gasiepgodoy/Open-Source-PLC/Hardware/KiCad Files/Components/3D/SM5819PL-TP--3DModel-STEP-56544.STEP

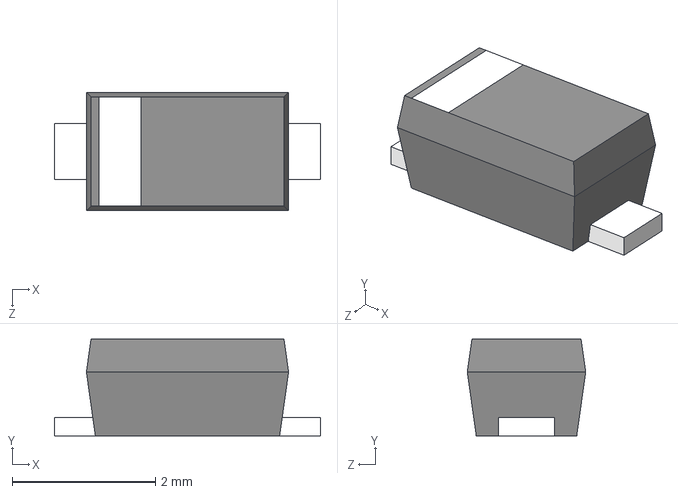
[picture p17: CAD file, 2024-05-21]
Hardware/KiCad Files/Components/3D/SM5819PL-TP--3DModel-STEP-56544.STEP
3.71 x 1.35 x 1.65 mm
