gasiepgodoy/Open-Source-PLC/Hardware/KiCad Files/Components/3D/74LCX14MTC.stp

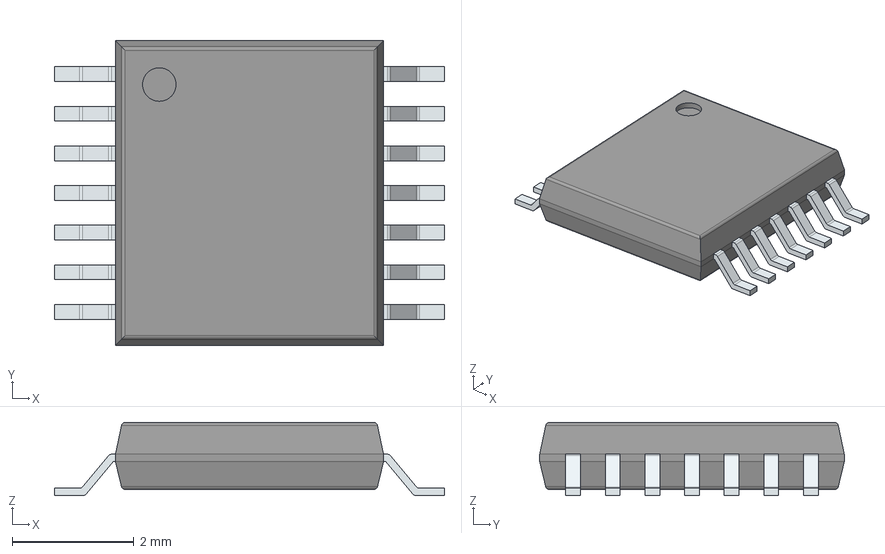
[picture p18: CAD file, 2024-05-21]
Hardware/KiCad Files/Components/3D/74LCX14MTC.stp
6.40 x 5.00 x 1.20 mm
PinsArrayLR
