gasiepgodoy/Open-Source-PLC/Hardware/KiCad Files/Components/3D/SN75LBC172A16DWR.stp

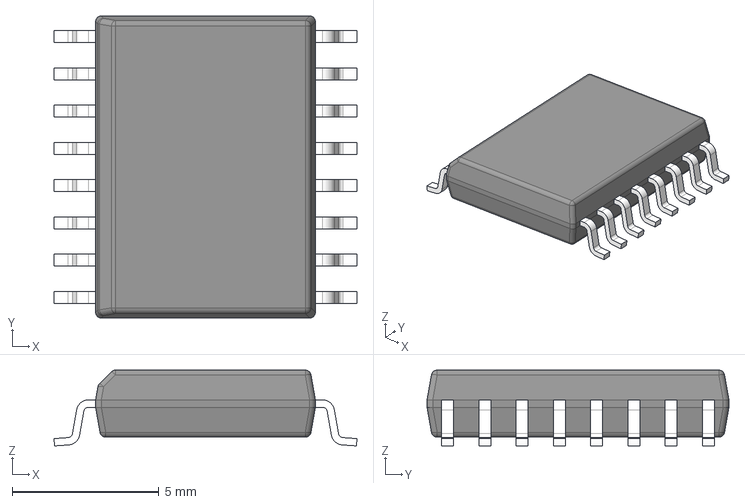
[picture p19: CAD file, 2024-05-21]
Hardware/KiCad Files/Components/3D/SN75LBC172A16DWR.stp
10.3 x 10.3 x 2.59 mm
BODY-SOIC
LEAD-DW0016 x 16
