gasiepgodoy/Open-Source-PLC/Hardware/KiCad Files/Components/3D/SC0915--3DModel-STEP-56544.STEP

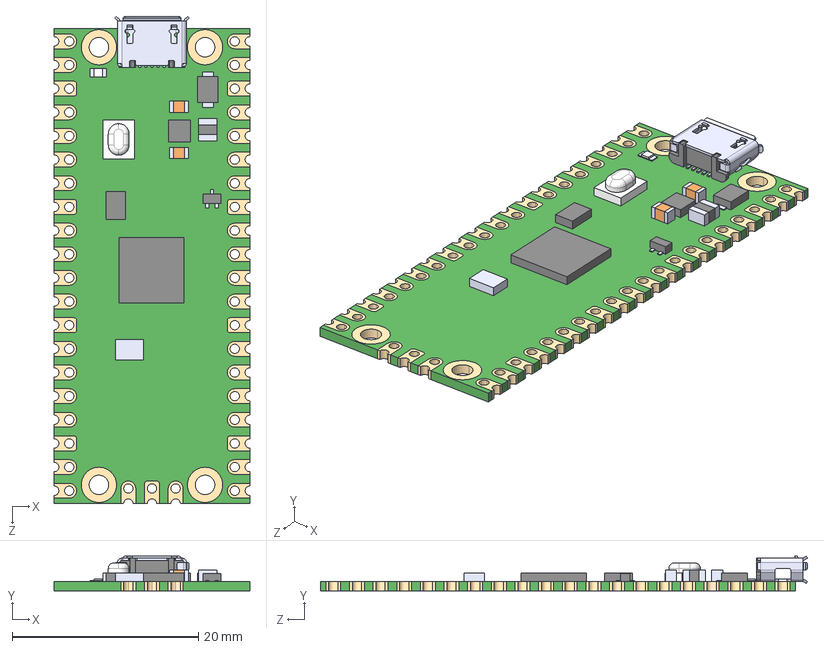
[picture p20: CAD file, 2024-05-21]
Hardware/KiCad Files/Components/3D/SC0915--3DModel-STEP-56544.STEP
21.0 x 3.73 x 52.3 mm
