gasiepgodoy/Open-Source-PLC/Hardware/KiCad Files/Components/3D/74LVX04M.STEP

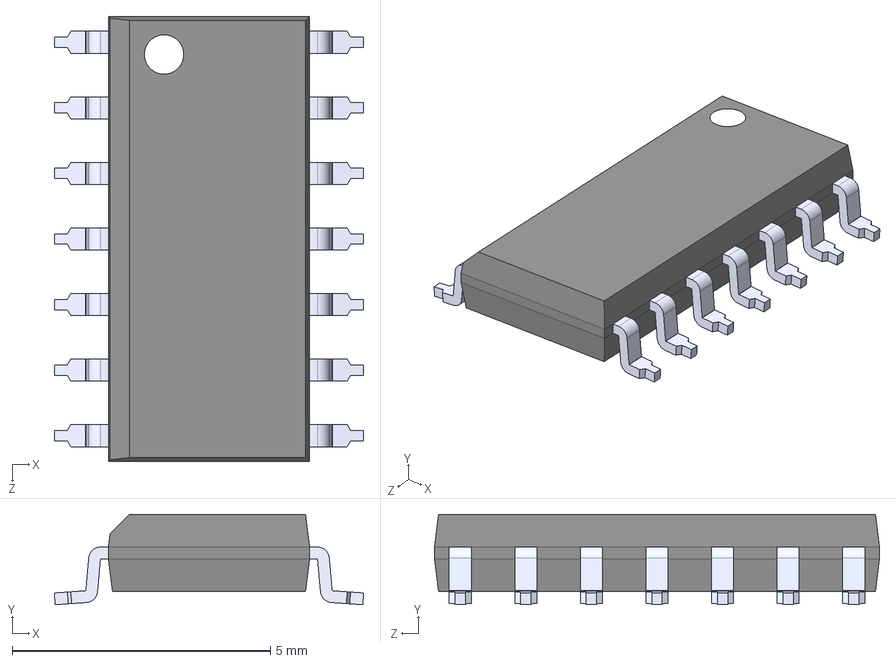
[picture p21: CAD file, 2024-05-21]
Hardware/KiCad Files/Components/3D/74LVX04M.STEP
5.99 x 1.75 x 8.62 mm
