gasiepgodoy/Open-Source-PLC/Hardware/KiCad Files/Components/3D/100SP1T2B4M6QE.step

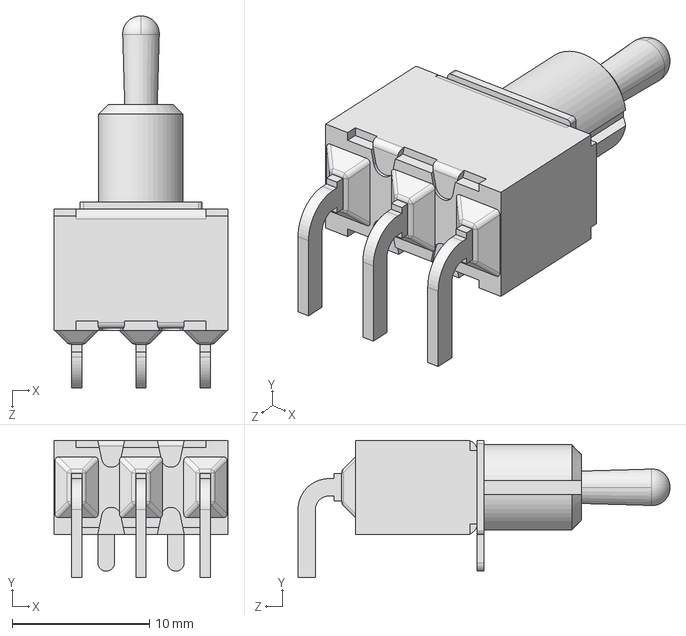
[picture p22: CAD file, 2024-05-21]
Hardware/KiCad Files/Components/3D/100SP1T2B4M6QE.step
12.7 x 10.0 x 27.2 mm
