gasiepgodoy/Open-Source-PLC/Hardware/KiCad Files/Components/3D/MBR0530T1G.stp

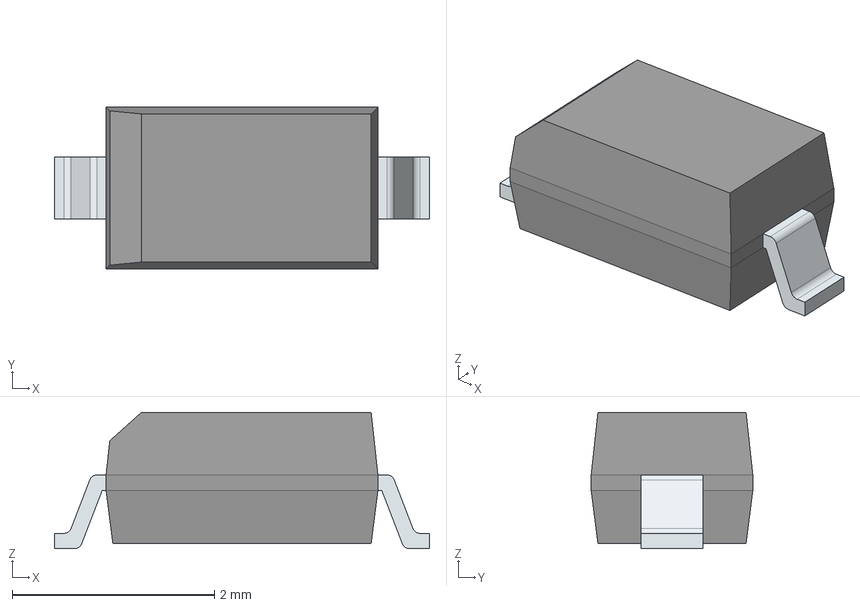
[picture p23: CAD file, 2024-05-21]
Hardware/KiCad Files/Components/3D/MBR0530T1G.stp
3.71 x 1.60 x 1.35 mm
FilletPinL
FilletPinR
