gasiepgodoy/Open-Source-PLC/Hardware/KiCad Files/Components/3D/MEM2075-00-140-01-A.stp

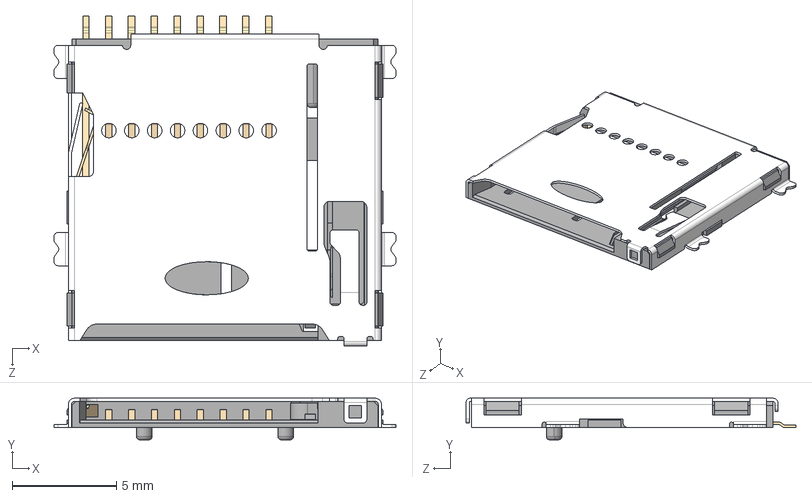
[picture p24: CAD file, 2024-05-21]
Hardware/KiCad Files/Components/3D/MEM2075-00-140-01-A.stp
16.4 x 2.00 x 15.9 mm
