gasiepgodoy/Open-Source-PLC/Hardware/KiCad Files/Components/3D/CRM2512-JW-302ELF.STEP

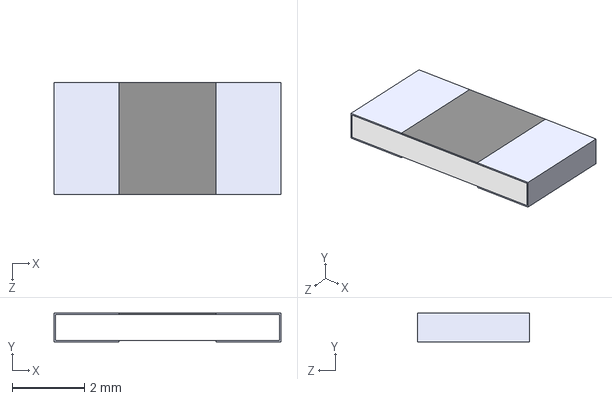
[picture p25: CAD file, 2024-05-21]
Hardware/KiCad Files/Components/3D/CRM2512-JW-302ELF.STEP
6.30 x 0.8 x 3.10 mm
