gasiepgodoy/Open-Source-PLC/Hardware/KiCad Files/Components/3D/TLP292-4_LGBTP,E.stp

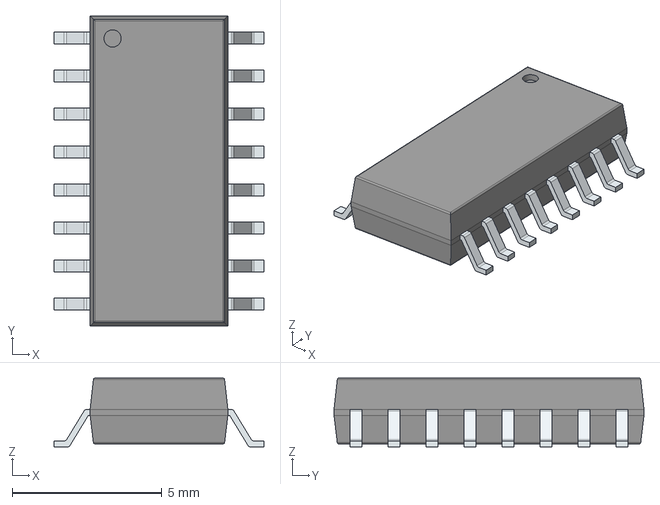
[picture p26: CAD file, 2024-05-21]
Hardware/KiCad Files/Components/3D/TLP292-4_LGBTP,E.stp
7.00 x 10.3 x 2.30 mm
PinsArrayLR
