gasiepgodoy/Open-Source-PLC/Hardware/KiCad Files/Components/3D/DMP6350SQ-7.stp

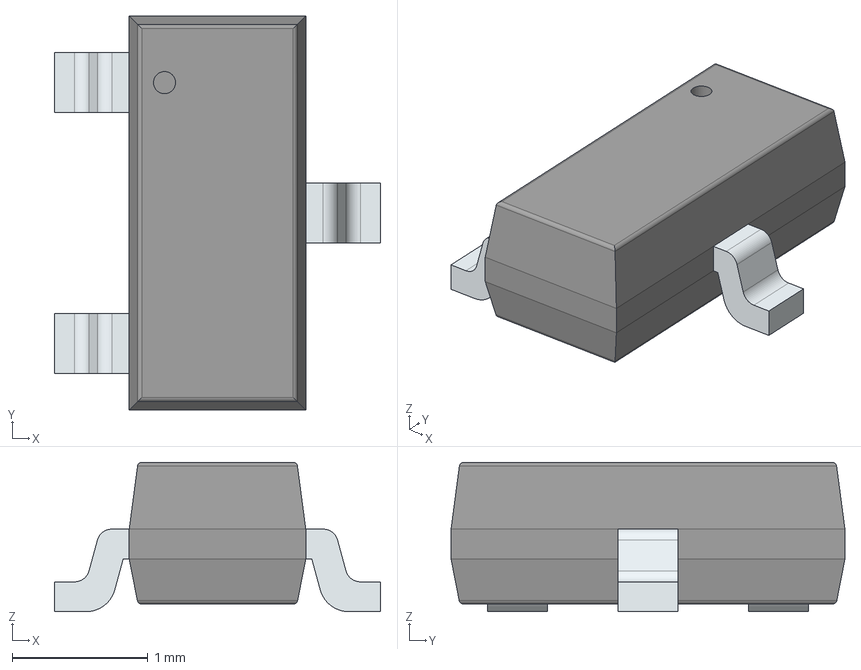
[picture p27: CAD file, 2024-05-21]
Hardware/KiCad Files/Components/3D/DMP6350SQ-7.stp
2.40 x 2.90 x 1.10 mm
PinsArrayL
FilletPinR
