gasiepgodoy/Open-Source-PLC/Hardware/KiCad Files/Components/3D/PH1-03-UA.stp

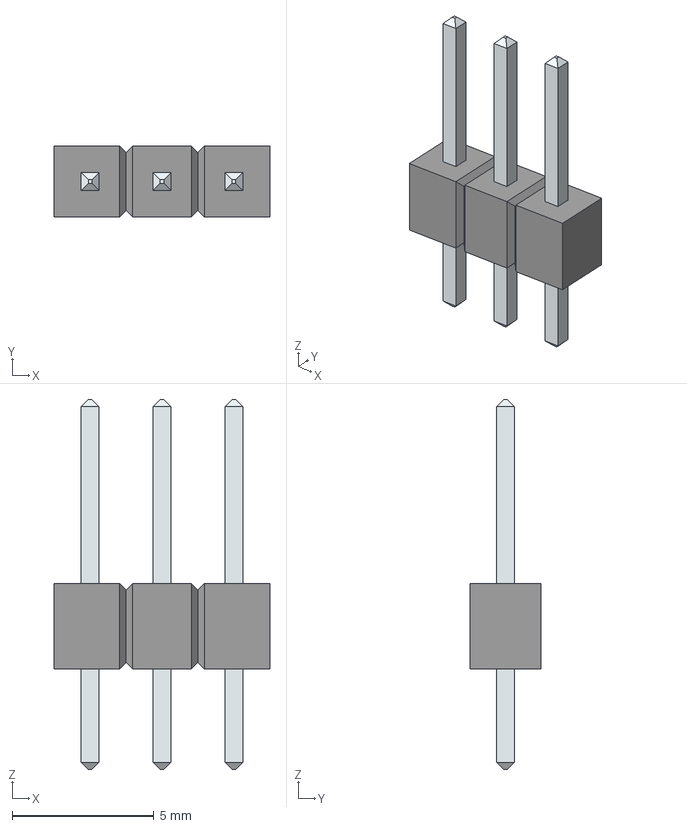
[picture p28: CAD file, 2024-05-21]
Hardware/KiCad Files/Components/3D/PH1-03-UA.stp
7.62 x 2.50 x 13.1 mm
LeadsArray
