gasiepgodoy/Open-Source-PLC/Hardware/KiCad Files/Components/3D/C1005X7R1E103K050BB.stp

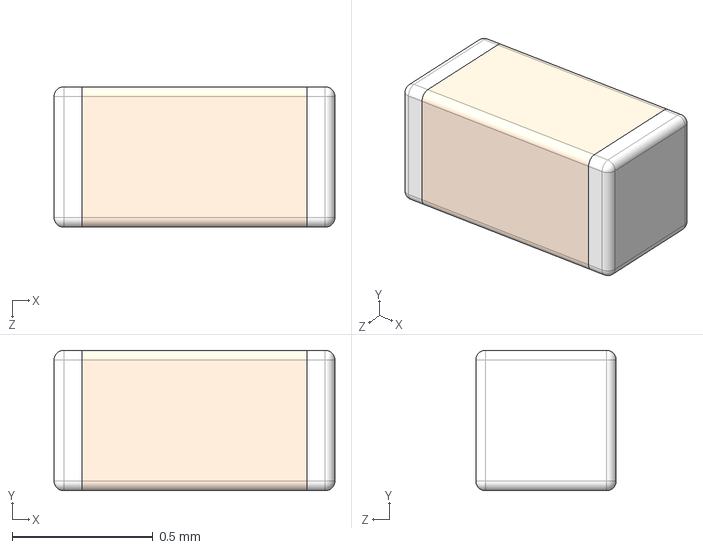
[picture p29: CAD file, 2024-05-21]
Hardware/KiCad Files/Components/3D/C1005X7R1E103K050BB.stp
1.00 x 0.5 x 0.5 mm
