gasiepgodoy/Open-Source-PLC/Hardware/KiCad Files/Components/3D/TNPW1206250RBEEN07.stp

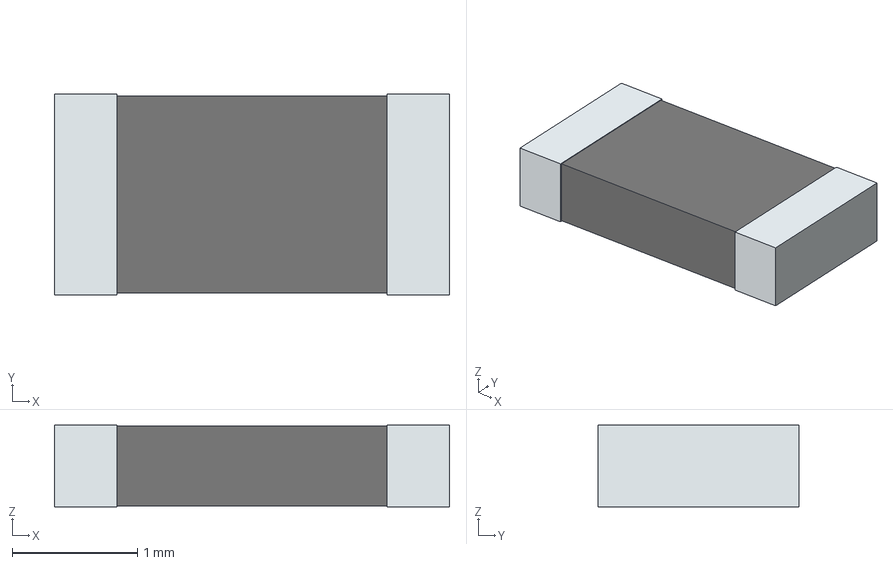
[picture p30: CAD file, 2024-05-21]
Hardware/KiCad Files/Components/3D/TNPW1206250RBEEN07.stp
3.15 x 1.60 x 0.65 mm
term1
term2
