gasiepgodoy/Open-Source-PLC/Hardware/KiCad Files/Components/3D/BLM18PG330SN1D.stp

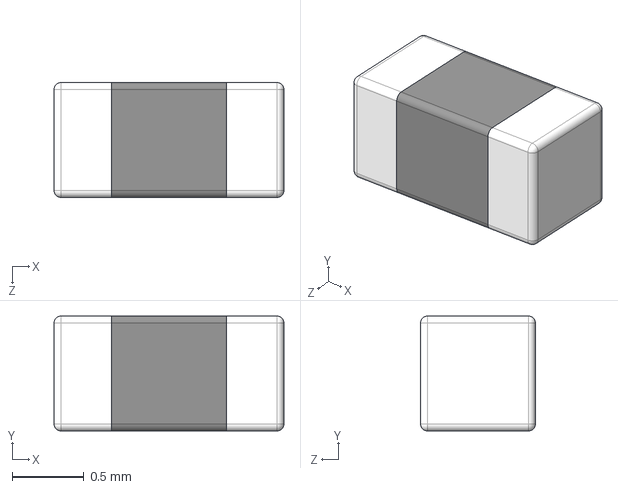
[picture p31: CAD file, 2024-05-21]
Hardware/KiCad Files/Components/3D/BLM18PG330SN1D.stp
1.60 x 0.8 x 0.8 mm
