gasiepgodoy/Open-Source-PLC/Hardware/KiCad Files/Components/3D/0603ESDA2-TR2.stp

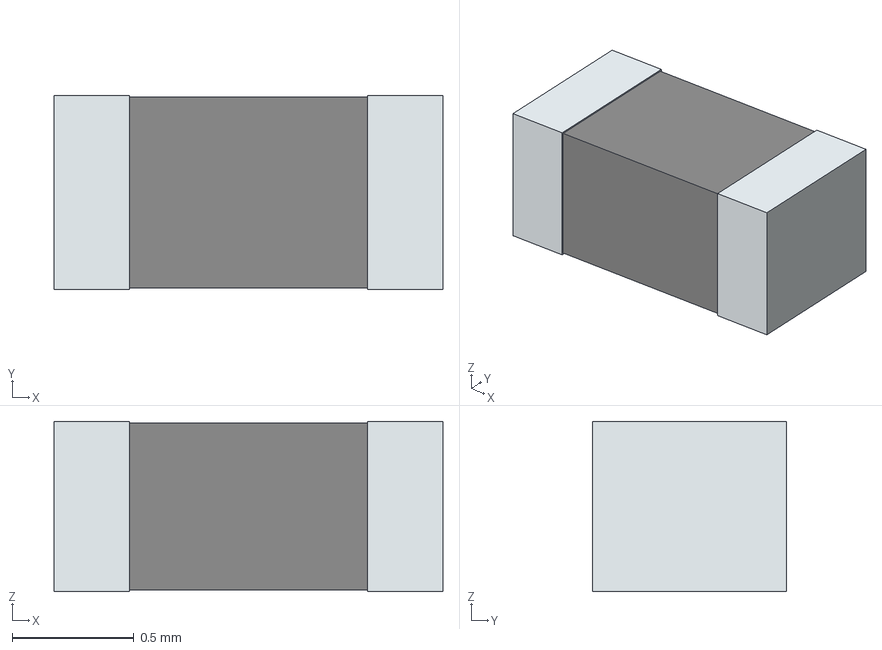
[picture p32: CAD file, 2024-05-21]
Hardware/KiCad Files/Components/3D/0603ESDA2-TR2.stp
1.60 x 0.8 x 0.7 mm
term1
term2
