gasiepgodoy/Open-Source-PLC/Hardware/KiCad Files/Components/3D/ADM3222ARUZ.stp

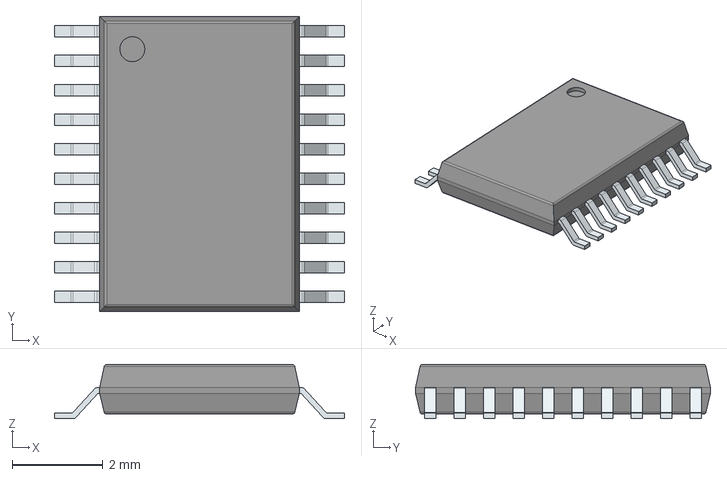
[picture p33: CAD file, 2024-05-21]
Hardware/KiCad Files/Components/3D/ADM3222ARUZ.stp
6.40 x 6.50 x 1.20 mm
PinsArrayLR
