gasiepgodoy/Open-Source-PLC/Hardware/KiCad Files/Components/3D/DDZ20ASF-7.stp

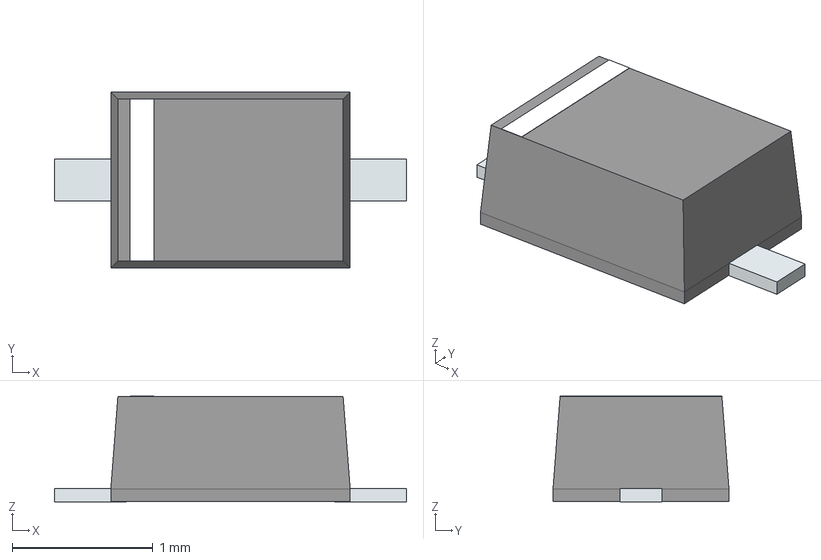
[picture p34: CAD file, 2024-05-21]
Hardware/KiCad Files/Components/3D/DDZ20ASF-7.stp
2.50 x 1.25 x 0.75 mm
PinKIdent
PinK
PinA
