gasiepgodoy/Open-Source-PLC/Hardware/KiCad Files/Components/3D/1SMA10CAT3G.stp

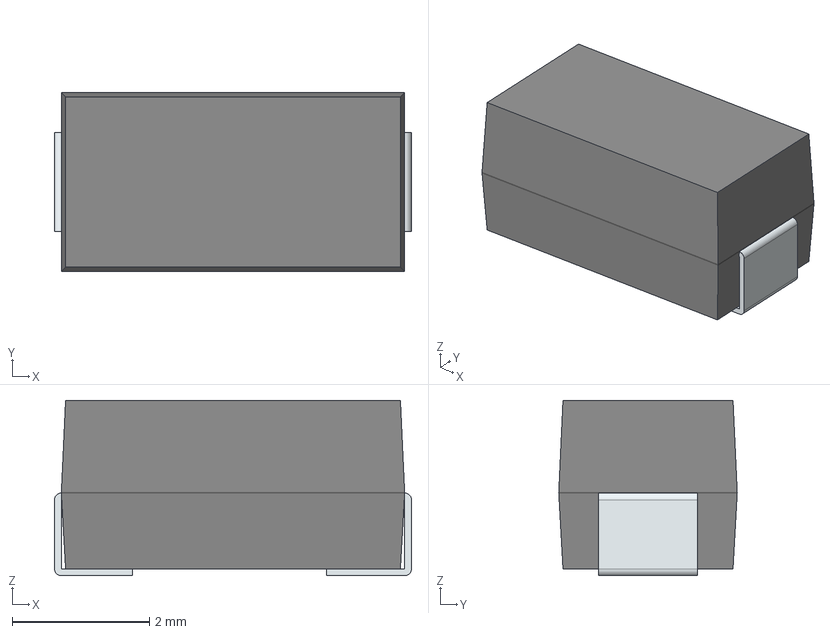
[picture p35: CAD file, 2024-05-21]
Hardware/KiCad Files/Components/3D/1SMA10CAT3G.stp
5.21 x 2.60 x 2.56 mm
FilletPin1
FilletPin2
