gasiepgodoy/Open-Source-PLC/Hardware/KiCad Files/Components/3D/UWX1C101MCL1GB.stp

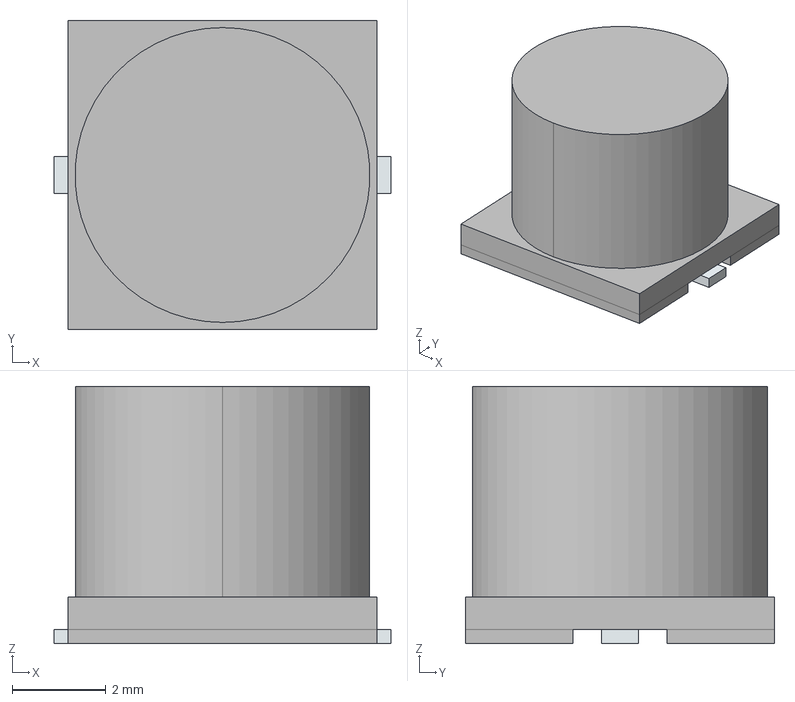
[picture p36: CAD file, 2024-05-21]
Hardware/KiCad Files/Components/3D/UWX1C101MCL1GB.stp
7.20 x 6.60 x 5.50 mm
solidBody
solidLead
solidBody1
