gasiepgodoy/Open-Source-PLC/Hardware/KiCad Files/Components/3D/DMG1029SV-7.stp

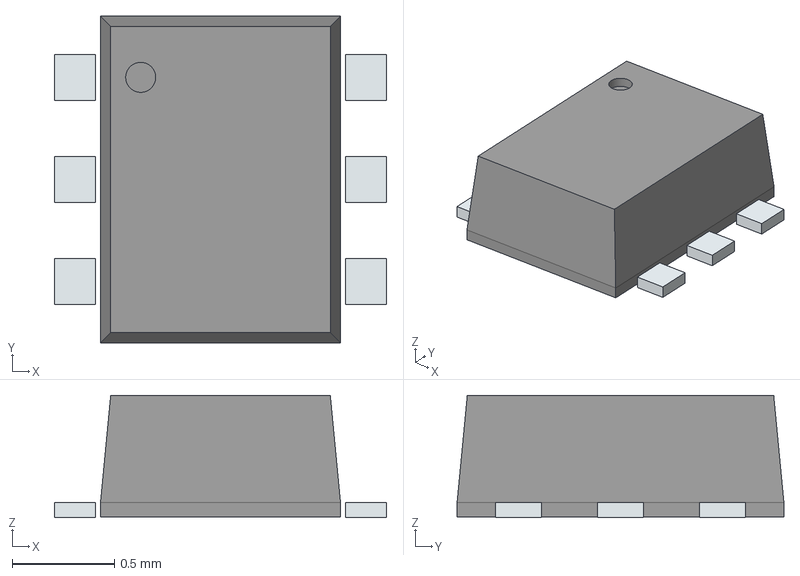
[picture p37: CAD file, 2024-05-21]
Hardware/KiCad Files/Components/3D/DMG1029SV-7.stp
1.62 x 1.60 x 0.598 mm
PinsArrayL
PinsArrayR
