gasiepgodoy/Open-Source-PLC/Hardware/KiCad Files/Components/3D/ADM3485EARZ.stp

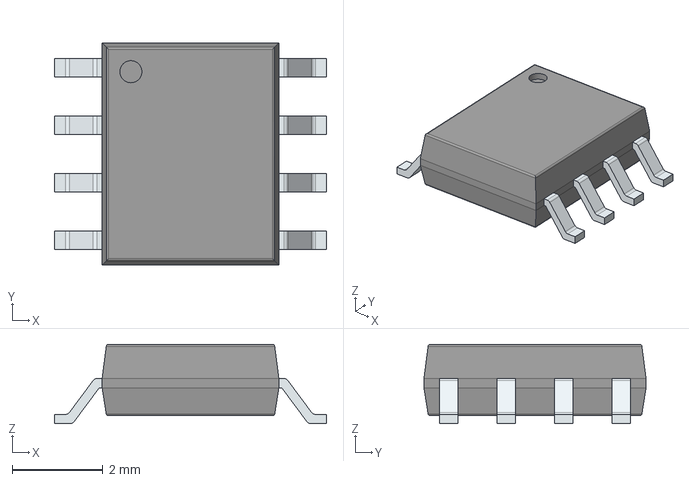
[picture p38: CAD file, 2024-05-21]
Hardware/KiCad Files/Components/3D/ADM3485EARZ.stp
6.00 x 4.90 x 1.75 mm
PinsArrayLR
