gasiepgodoy/Open-Source-PLC/Hardware/KiCad Files/Components/3D/GRM155R71H104KE14D.stp

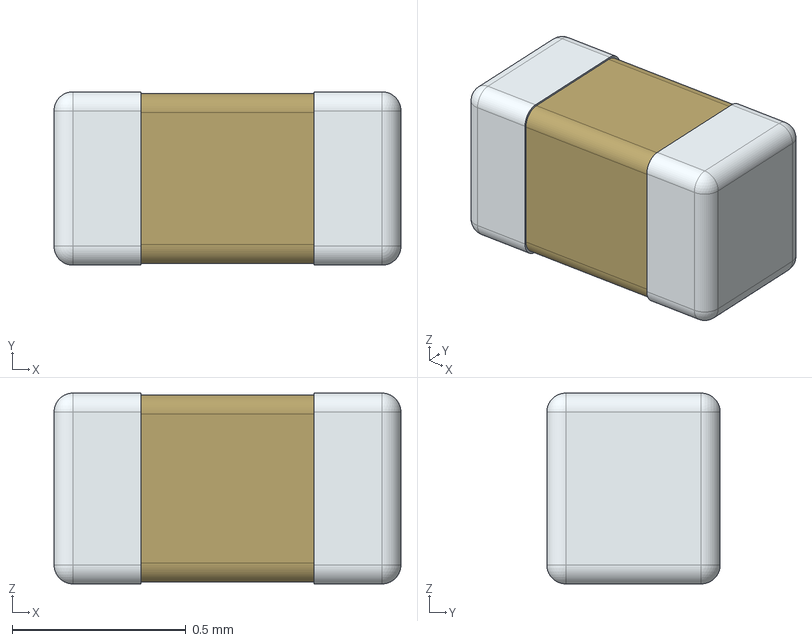
[picture p39: CAD file, 2024-05-21]
Hardware/KiCad Files/Components/3D/GRM155R71H104KE14D.stp
1.00 x 0.5 x 0.55 mm
