gasiepgodoy/Open-Source-PLC/Hardware/KiCad Files/Components/3D/P6SMB6.8CA.stp

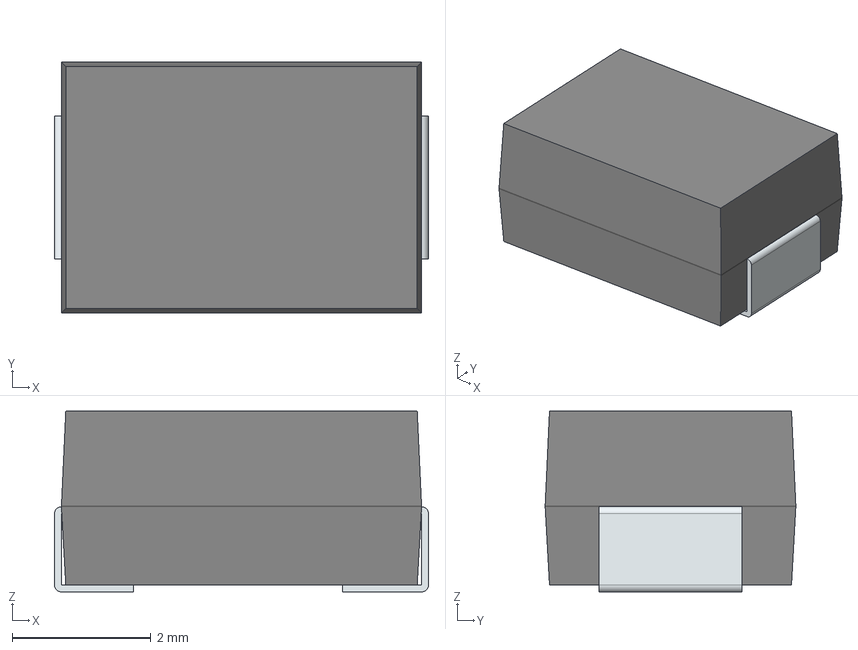
[picture p40: CAD file, 2024-05-21]
Hardware/KiCad Files/Components/3D/P6SMB6.8CA.stp
5.40 x 3.62 x 2.61 mm
FilletPin1
FilletPin2
