gasiepgodoy/Open-Source-PLC/Hardware/KiCad Files/Components/3D/B1100-13-F.stp

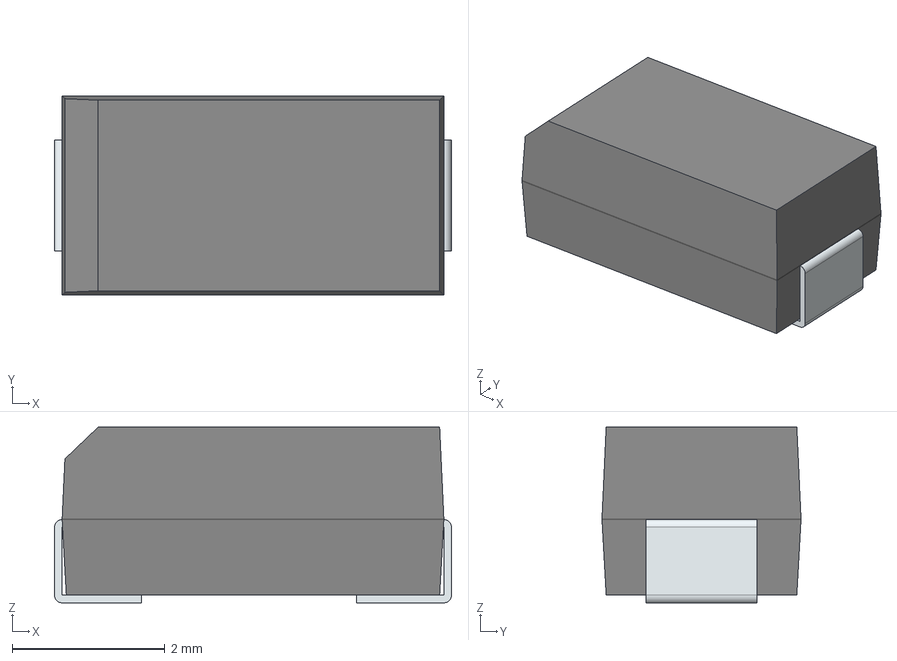
[picture p41: CAD file, 2024-05-21]
Hardware/KiCad Files/Components/3D/B1100-13-F.stp
5.20 x 2.60 x 2.30 mm
FilletPin1
FilletPin2
