gasiepgodoy/Open-Source-PLC/Hardware/KiCad Files/Components/3D/ERJ-6ENF5761V.stp

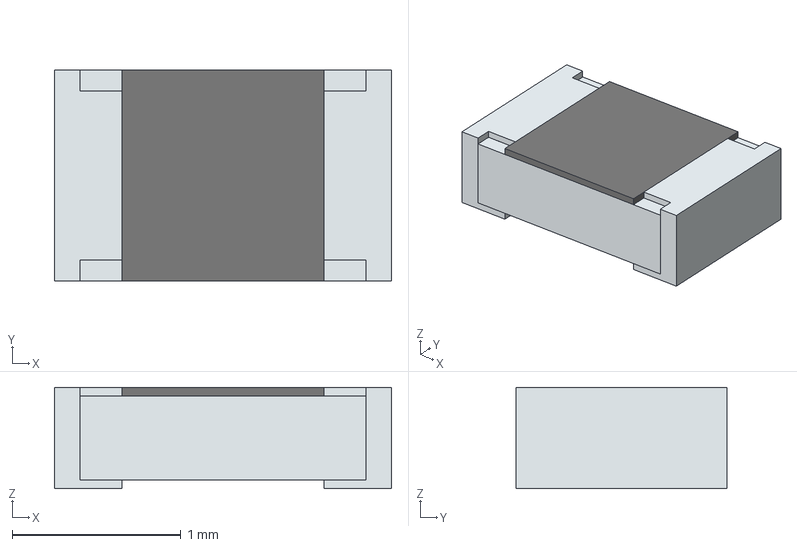
[picture p42: CAD file, 2024-05-21]
Hardware/KiCad Files/Components/3D/ERJ-6ENF5761V.stp
2.00 x 1.25 x 0.6 mm
solidBody
Terminal
solidTop
