gasiepgodoy/Open-Source-PLC/Hardware/KiCad Files/Components/3D/SN74LVC1G125DBVR.STEP

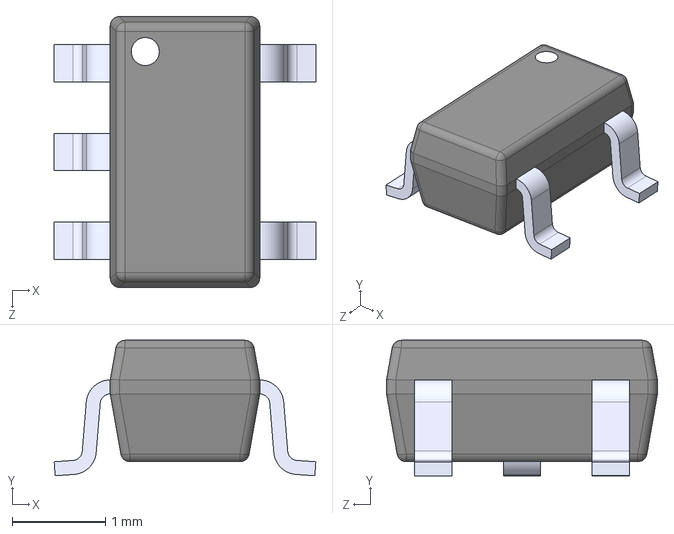
[picture p43: CAD file, 2024-05-21]
Hardware/KiCad Files/Components/3D/SN74LVC1G125DBVR.STEP
2.80 x 1.45 x 2.90 mm
