gasiepgodoy/Open-Source-PLC/Hardware/KiCad Files/Components/3D/0ZCF0100AF2A.stp

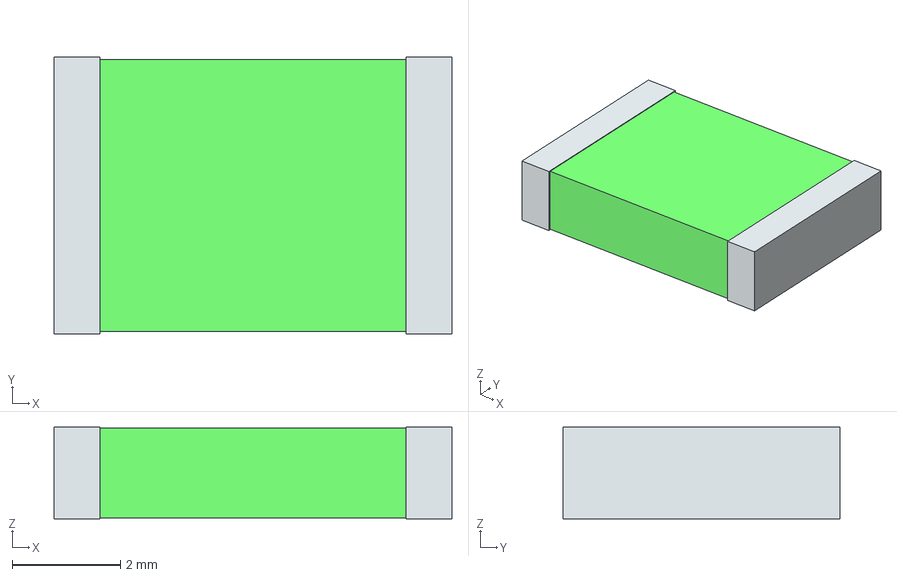
[picture p44: CAD file, 2024-05-21]
Hardware/KiCad Files/Components/3D/0ZCF0100AF2A.stp
7.36 x 5.12 x 1.70 mm
term1
term2
