gasiepgodoy/Open-Source-PLC/Hardware/KiCad Files/Components/3D/FOD2742B.stp

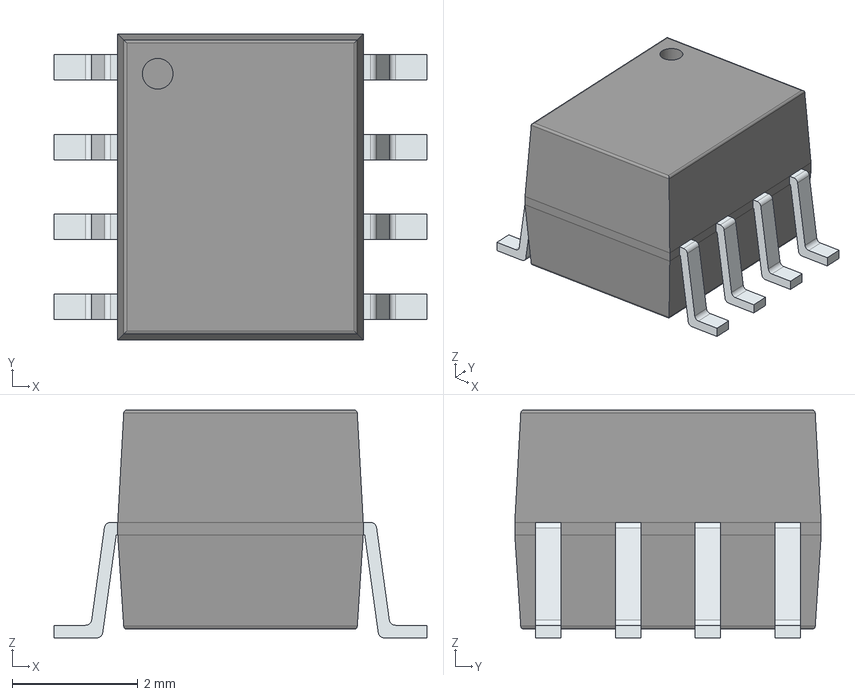
[picture p45: CAD file, 2024-05-21]
Hardware/KiCad Files/Components/3D/FOD2742B.stp
5.94 x 4.88 x 3.63 mm
PinsArrayLR
