gasiepgodoy/Open-Source-PLC/Hardware/KiCad Files/Components/3D/LTV-356T--3DModel-STEP-510211.STEP

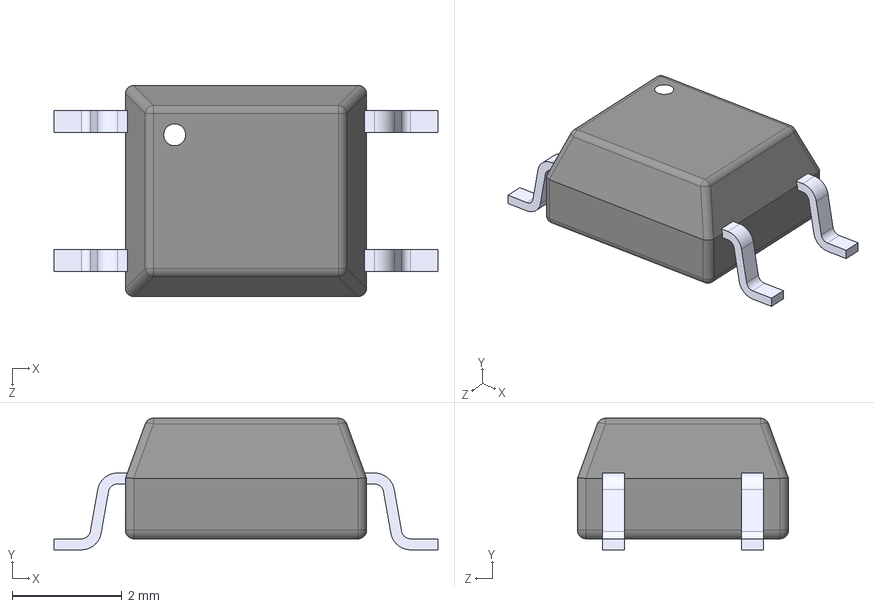
[picture p46: CAD file, 2024-05-21]
Hardware/KiCad Files/Components/3D/LTV-356T--3DModel-STEP-510211.STEP
7.00 x 2.40 x 3.85 mm
