gasiepgodoy/Open-Source-PLC/Hardware/KiCad Files/Components/3D/DLW5BTM142TQ2B.stp

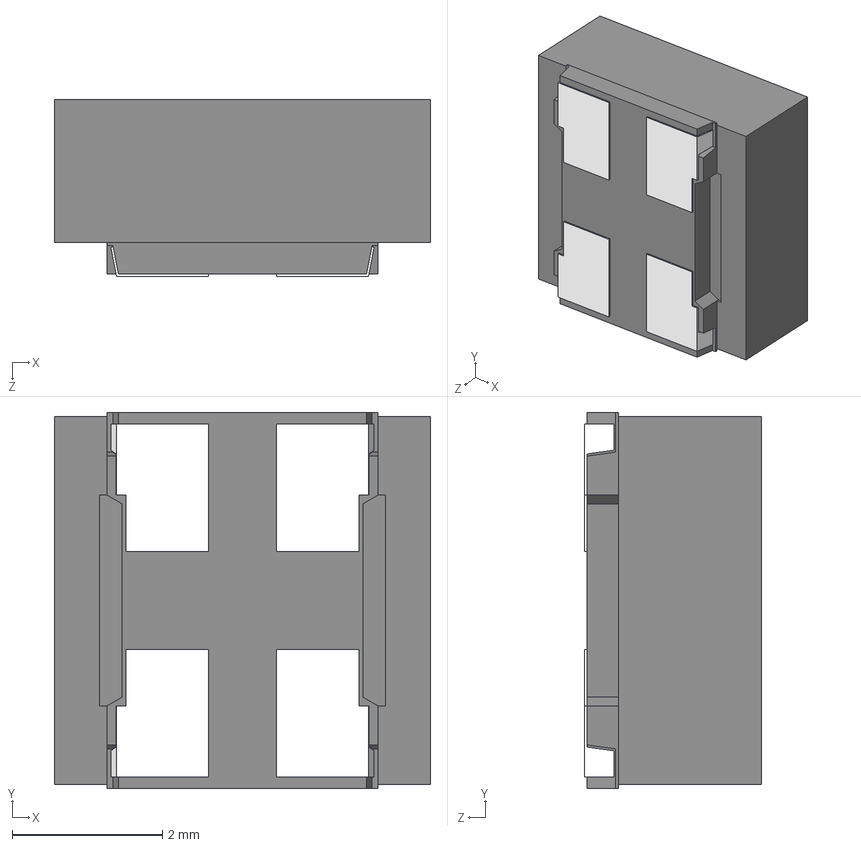
[picture p47: CAD file, 2024-05-21]
Hardware/KiCad Files/Components/3D/DLW5BTM142TQ2B.stp
5.00 x 5.00 x 2.35 mm
