gasiepgodoy/Open-Source-PLC/Hardware/KiCad Files/Components/3D/MMBT2907A-7-F.stp

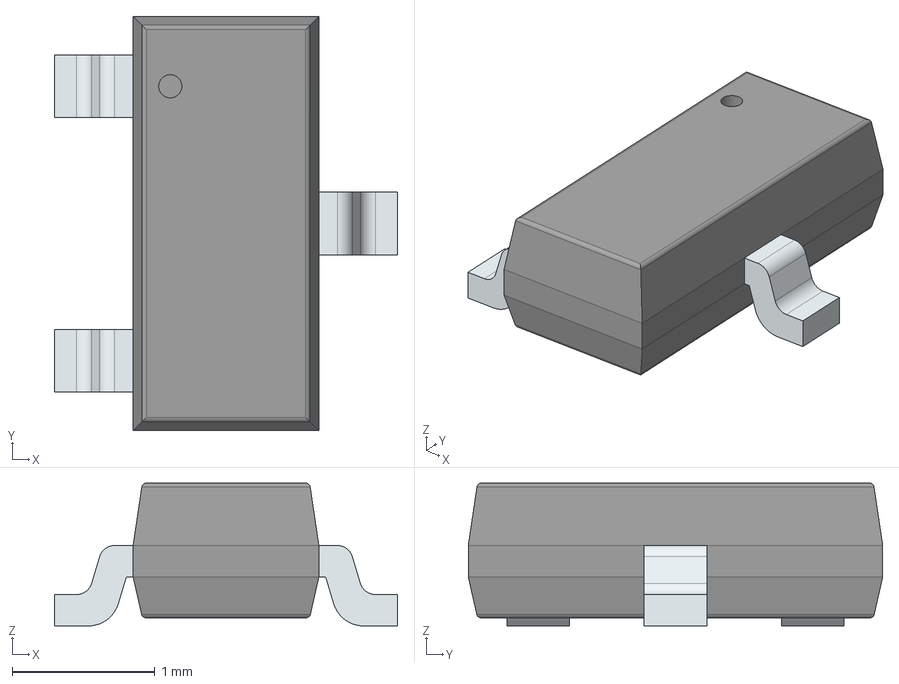
[picture p48: CAD file, 2024-05-21]
Hardware/KiCad Files/Components/3D/MMBT2907A-7-F.stp
2.40 x 2.90 x 1.00 mm
PinsArrayL
FilletPinR
