gasiepgodoy/Open-Source-PLC/Hardware/KiCad Files/Components/3D/SI8640AB-B-IS.STEP

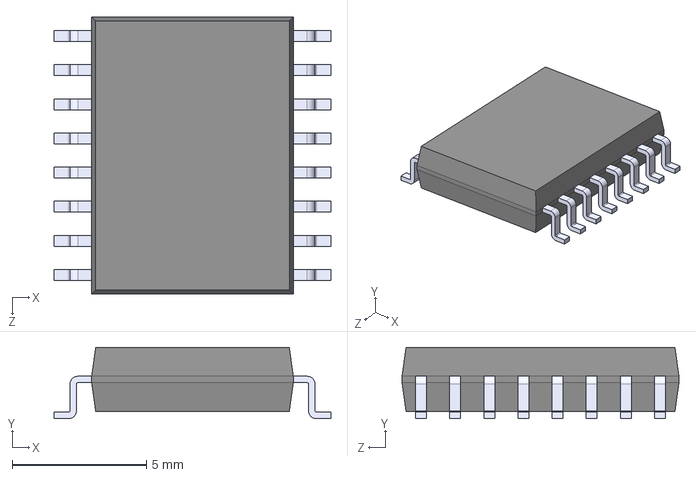
[picture p49: CAD file, 2024-05-21]
Hardware/KiCad Files/Components/3D/SI8640AB-B-IS.STEP
10.3 x 2.65 x 10.3 mm
