gasiepgodoy/Open-Source-PLC/Hardware/KiCad Files/Components/3D/SN74AHC08PW.stp

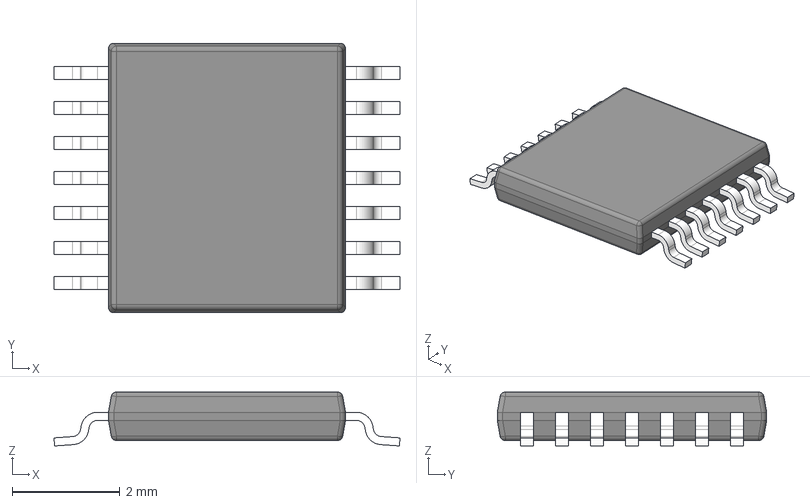
[picture p50: CAD file, 2024-05-21]
Hardware/KiCad Files/Components/3D/SN74AHC08PW.stp
6.42 x 5.00 x 1.00 mm
BODY-SO
LEAD-SO x 14
THERMALPAD-SO
PIN1-ID
