gasiepgodoy/Open-Source-PLC/Hardware/KiCad Files/Components/3D/GJ821BR61E106KE11L.stp

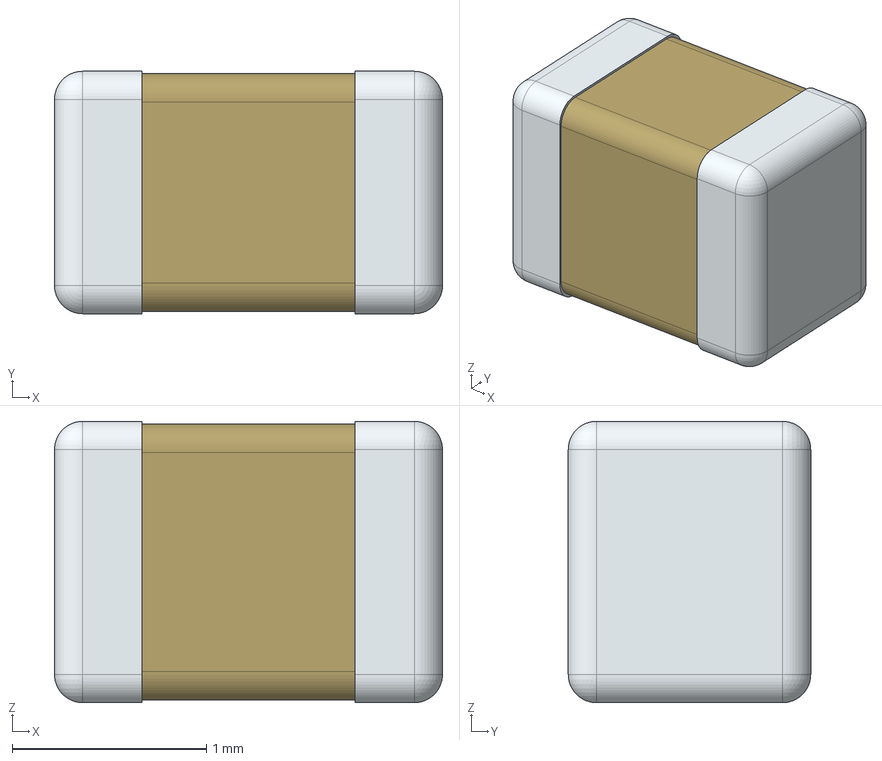
[picture p51: CAD file, 2024-05-21]
Hardware/KiCad Files/Components/3D/GJ821BR61E106KE11L.stp
2.00 x 1.25 x 1.45 mm
