gasiepgodoy/Open-Source-PLC/Hardware/KiCad Files/Components/3D/ERA-2AED331X.stp

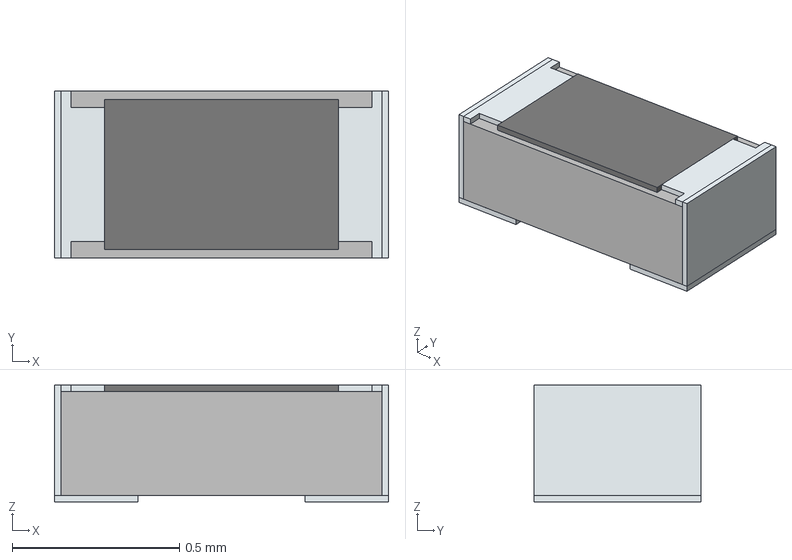
[picture p52: CAD file, 2024-05-21]
Hardware/KiCad Files/Components/3D/ERA-2AED331X.stp
1.00 x 0.5 x 0.35 mm
solidBody
solidTop
solidTerminal1
solidTerminal2
solidTerminal3
