gasiepgodoy/Open-Source-PLC/Hardware/KiCad Files/Components/3D/ECJ-2FB1E475M.stp

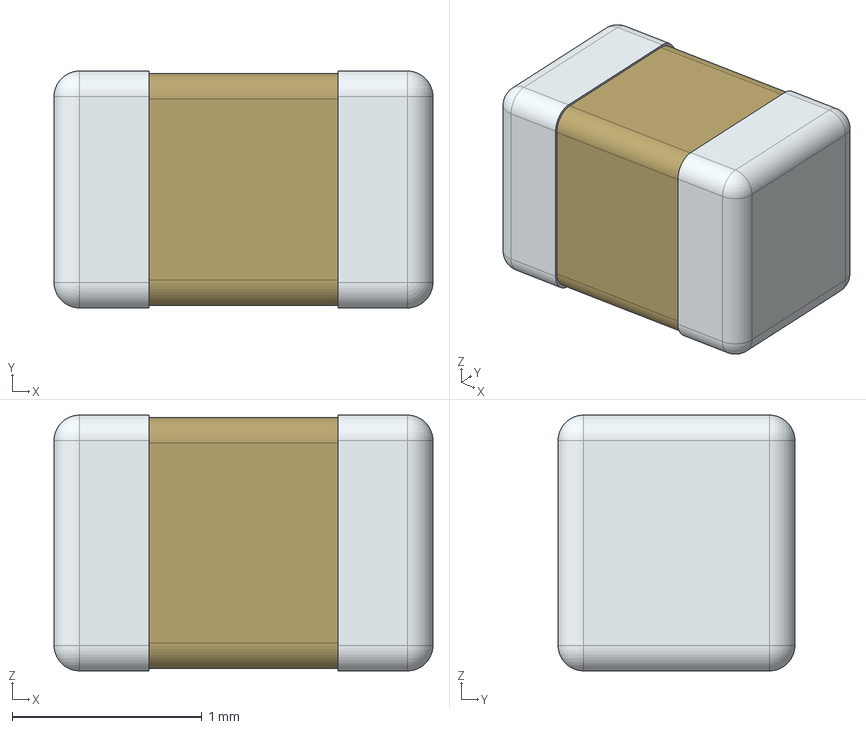
[picture p53: CAD file, 2024-05-21]
Hardware/KiCad Files/Components/3D/ECJ-2FB1E475M.stp
2.00 x 1.25 x 1.35 mm
