gasiepgodoy/Open-Source-PLC/Hardware/KiCad Files/Components/3D/SRR1240-101M.step

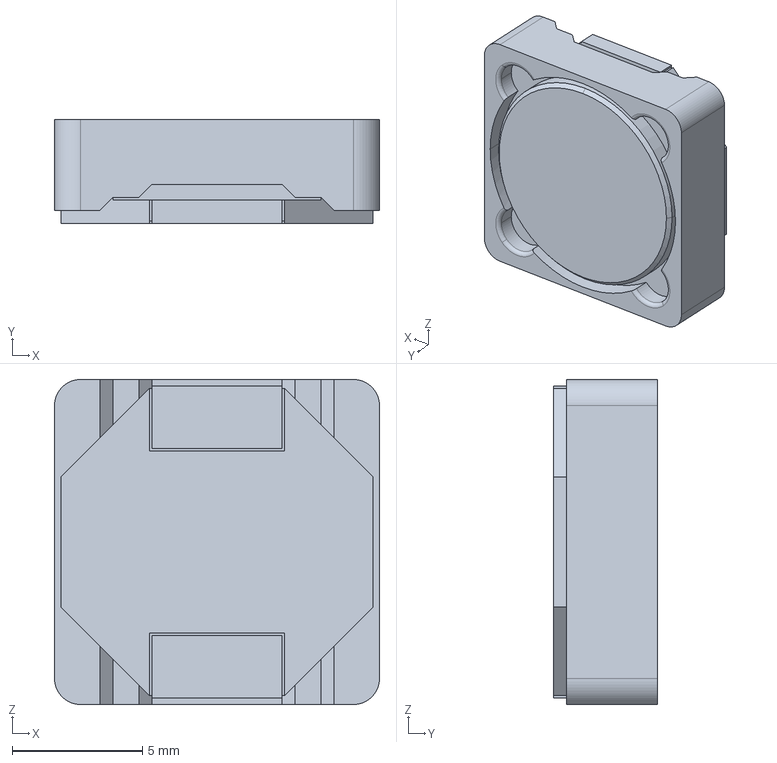
[picture p54: CAD file, 2024-05-21]
Hardware/KiCad Files/Components/3D/SRR1240-101M.step
12.5 x 4.00 x 12.5 mm
