gasiepgodoy/Open-Source-PLC/Hardware/KiCad Files/Components/3D/ZDO_SP4022_LTF.step

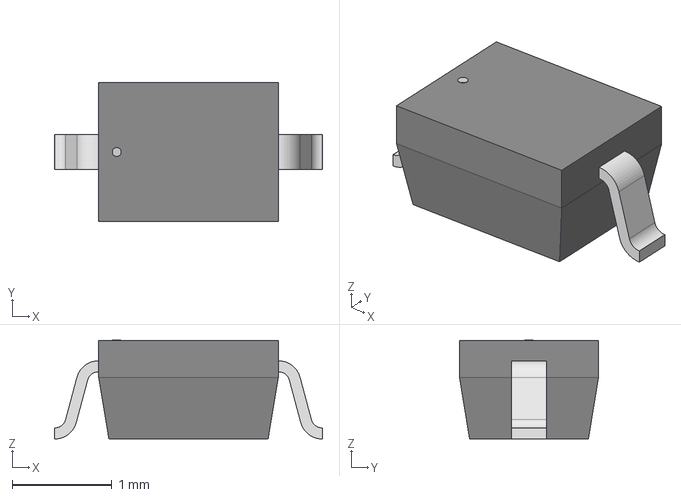
[picture p55: CAD file, 2024-05-21]
Hardware/KiCad Files/Components/3D/ZDO_SP4022_LTF.step
2.69 x 1.40 x 0.993 mm
