gasiepgodoy/Open-Source-PLC/Hardware/KiCad Files/Components/3D/ST26C32ABTR.stp

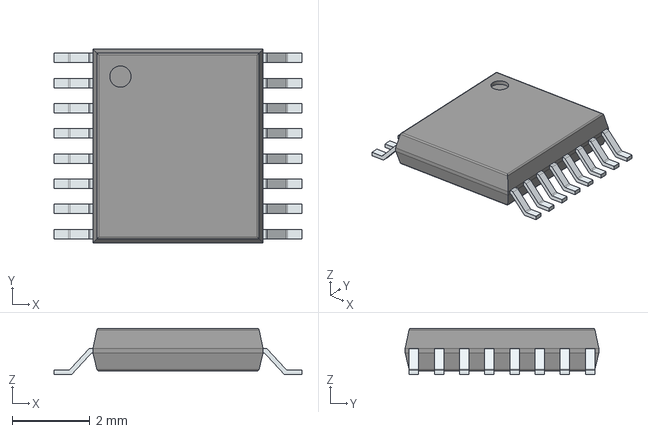
[picture p56: CAD file, 2024-05-21]
Hardware/KiCad Files/Components/3D/ST26C32ABTR.stp
6.40 x 5.00 x 1.20 mm
PinsArrayLR
