gasiepgodoy/Open-Source-PLC/Hardware/KiCad Files/Components/3D/L7805CD2T-TR.STEP

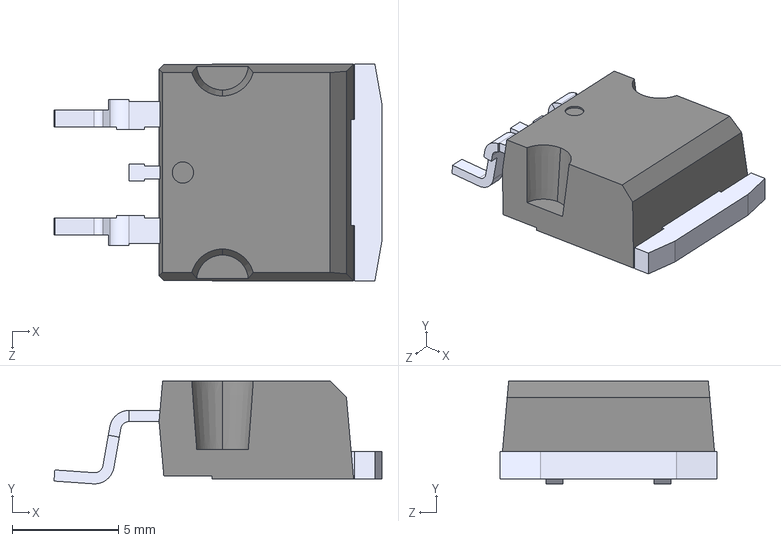
[picture p57: CAD file, 2024-05-21]
Hardware/KiCad Files/Components/3D/L7805CD2T-TR.STEP
15.4 x 4.83 x 10.2 mm
