gasiepgodoy/Open-Source-PLC/Hardware/KiCad Files/Components/3D/B240A-13-F.STEP

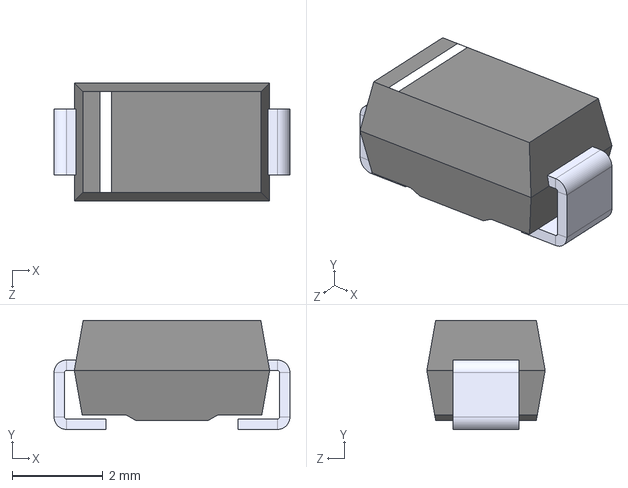
[picture p58: CAD file, 2024-05-21]
Hardware/KiCad Files/Components/3D/B240A-13-F.STEP
5.20 x 2.40 x 2.60 mm
