gasiepgodoy/Open-Source-PLC/Hardware/KiCad Files/Components/3D/M24C01-RDW6TP.STEP

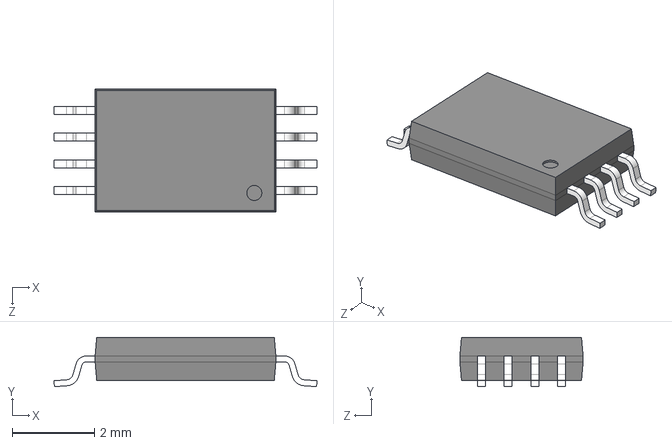
[picture p59: CAD file, 2024-05-21]
Hardware/KiCad Files/Components/3D/M24C01-RDW6TP.STEP
6.40 x 1.20 x 3.00 mm
