gasiepgodoy/Open-Source-PLC/Hardware/KiCad Files/Components/3D/TL1105RF250Q--3DModel-STEP-520916.STEP

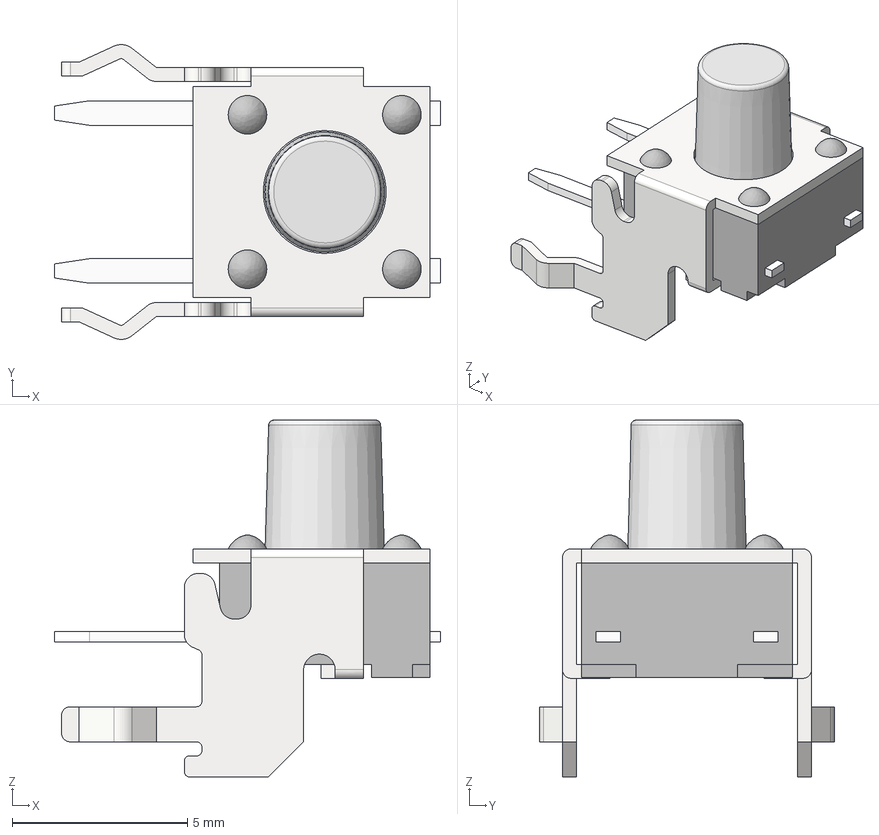
[picture p60: CAD file, 2024-05-21]
Hardware/KiCad Files/Components/3D/TL1105RF250Q--3DModel-STEP-520916.STEP
11.0 x 8.40 x 10.2 mm
