gasiepgodoy/Open-Source-PLC/Hardware/KiCad Files/Components/3D/MBRS340T3G.stp

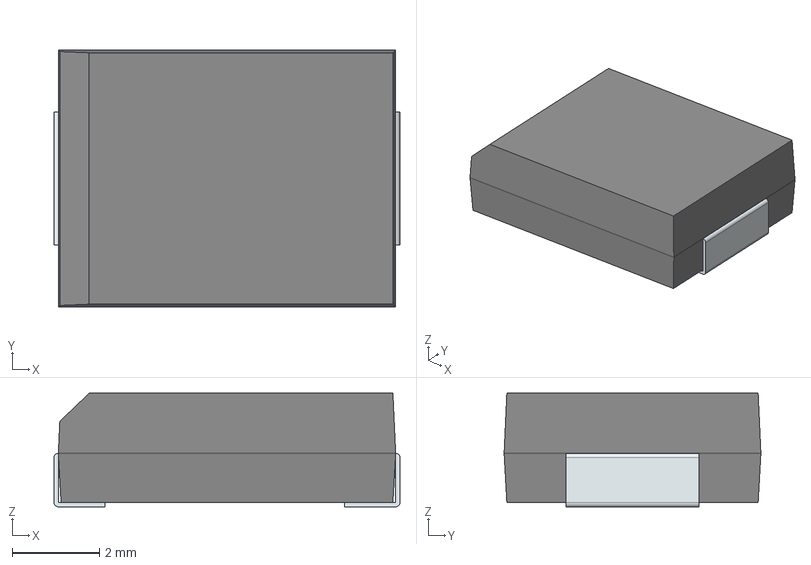
[picture p61: CAD file, 2024-05-21]
Hardware/KiCad Files/Components/3D/MBRS340T3G.stp
7.95 x 5.90 x 2.61 mm
FilletPin1
FilletPin2
