gasiepgodoy/Open-Source-PLC/Hardware/KiCad Files/Components/3D/SRU1063-220Y.stp

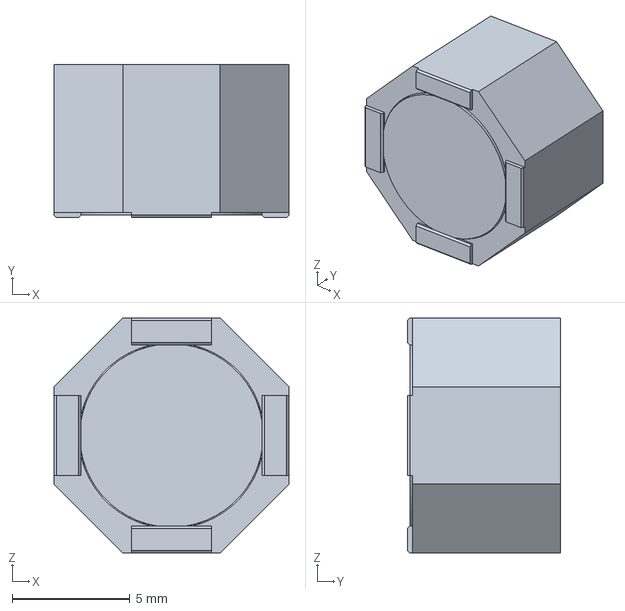
[picture p62: CAD file, 2024-05-21]
Hardware/KiCad Files/Components/3D/SRU1063-220Y.stp
10.0 x 6.50 x 10.0 mm
