gasiepgodoy/Open-Source-PLC/Hardware/KiCad Files/Components/3D/LM3485MMX_NOPB.stp

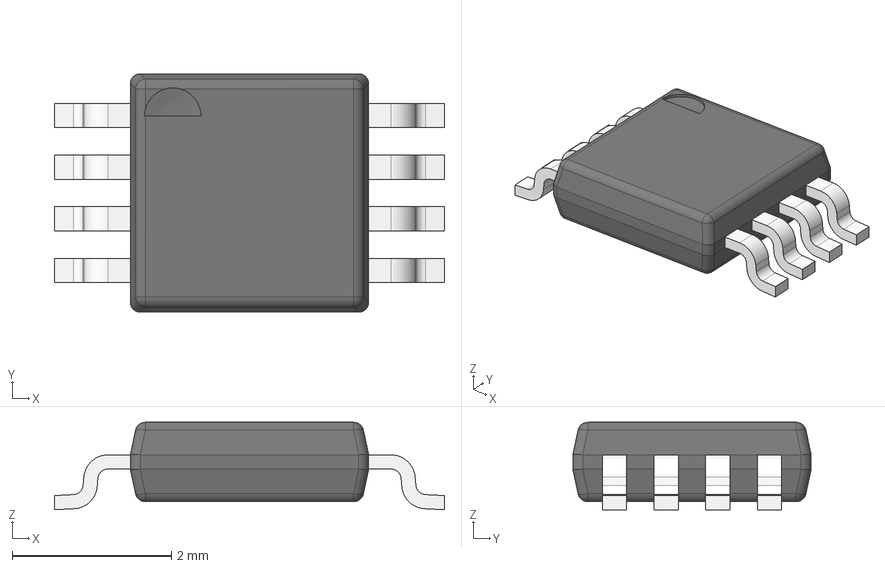
[picture p63: CAD file, 2024-05-21]
Hardware/KiCad Files/Components/3D/LM3485MMX_NOPB.stp
4.90 x 3.00 x 1.10 mm
BODY_MUA08A
LEAD_MUA08A x 8
