gasiepgodoy/Open-Source-PLC/Hardware/KiCad Files/Components/3D/FDMS4435BZ.stp

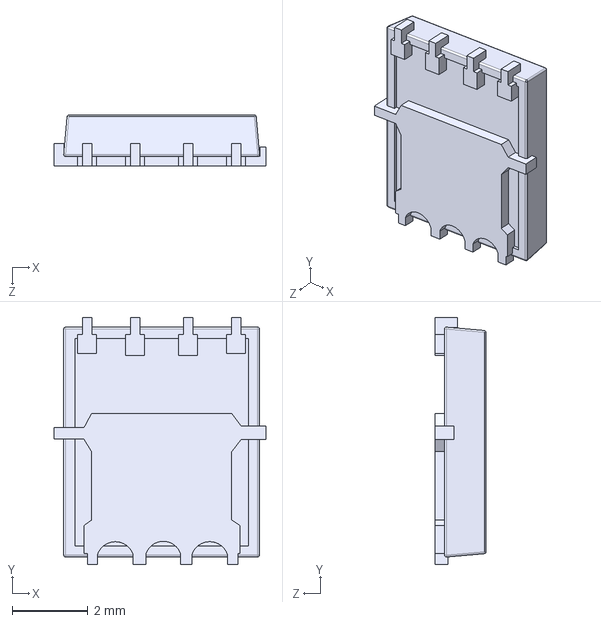
[picture p64: CAD file, 2024-05-21]
Hardware/KiCad Files/Components/3D/FDMS4435BZ.stp
5.61 x 6.53 x 1.35 mm
