gasiepgodoy/Open-Source-PLC/Hardware/KiCad Files/Components/3D/RK73H1ETTP10R0F.stp

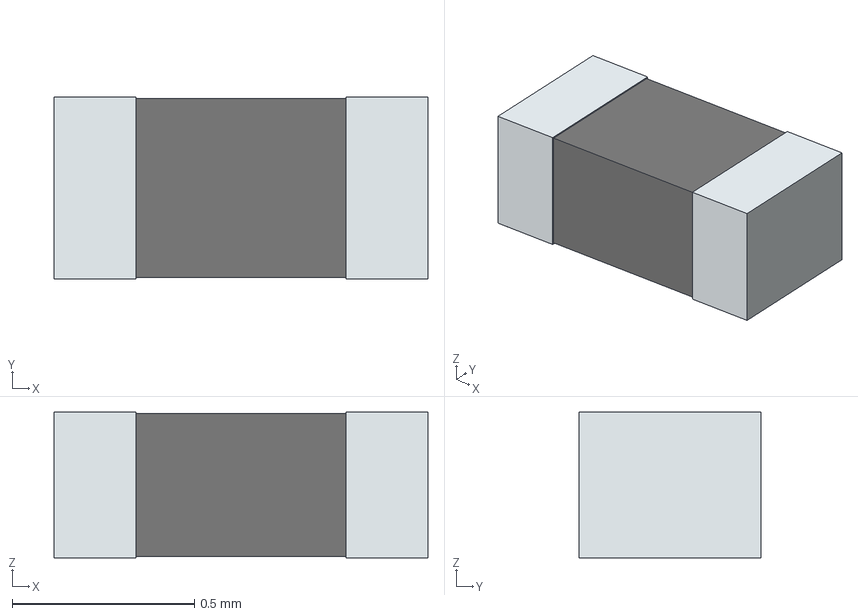
[picture p65: CAD file, 2024-05-21]
Hardware/KiCad Files/Components/3D/RK73H1ETTP10R0F.stp
1.02 x 0.5 x 0.4 mm
term1
term2
