gasiepgodoy/Open-Source-PLC/Hardware/KiCad Files/Components/3D/200MSP2T3B2M6QE--3DModel-STEP-520916.STEP

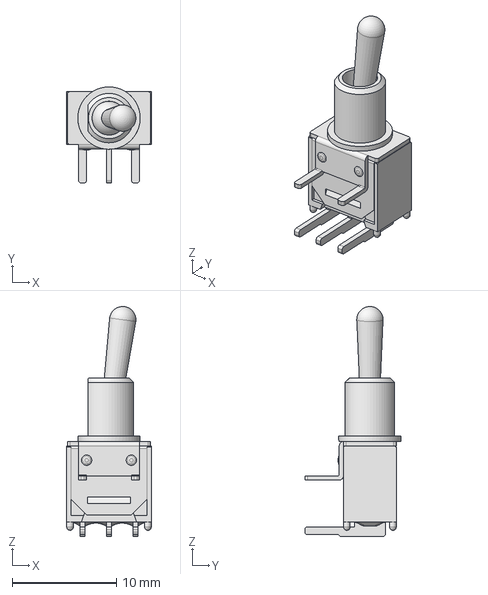
[picture p66: CAD file, 2024-05-21]
Hardware/KiCad Files/Components/3D/200MSP2T3B2M6QE--3DModel-STEP-520916.STEP
8.13 x 9.25 x 22.1 mm
