gasiepgodoy/Open-Source-PLC/Hardware/KiCad Files/Components/3D/2N7002DW.STEP

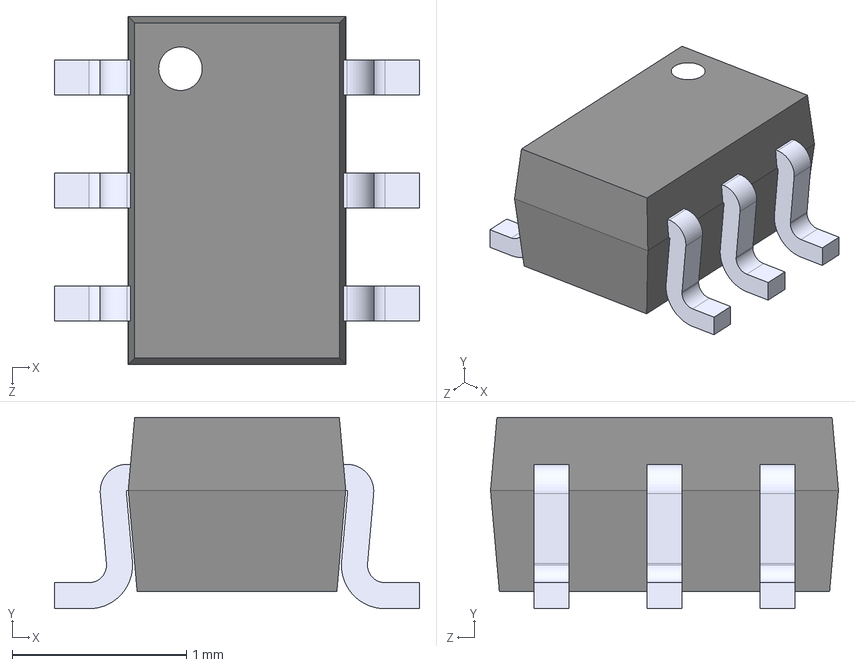
[picture p67: CAD file, 2024-05-21]
Hardware/KiCad Files/Components/3D/2N7002DW.STEP
2.10 x 1.10 x 2.00 mm
