gasiepgodoy/Open-Source-PLC/Hardware/KiCad Files/Components/3D/Si8641AB-B-IS1.stp

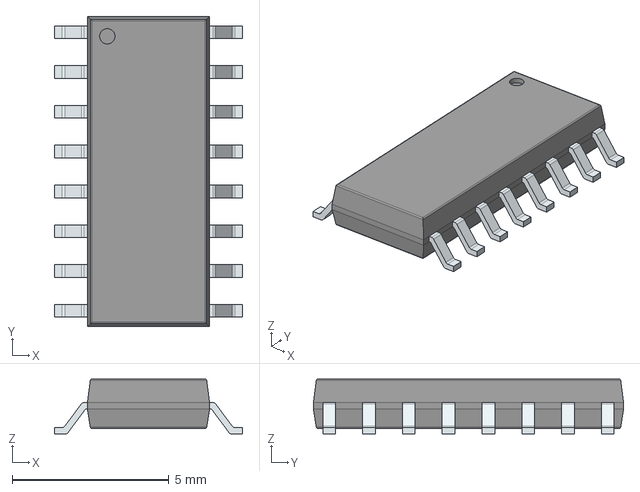
[picture p68: CAD file, 2024-05-21]
Hardware/KiCad Files/Components/3D/Si8641AB-B-IS1.stp
6.00 x 9.90 x 1.75 mm
PinsArrayLR
