gasiepgodoy/Open-Source-PLC/Hardware/KiCad Files/Components/3D/POWERFLAT_3P3X3P3_STM.step

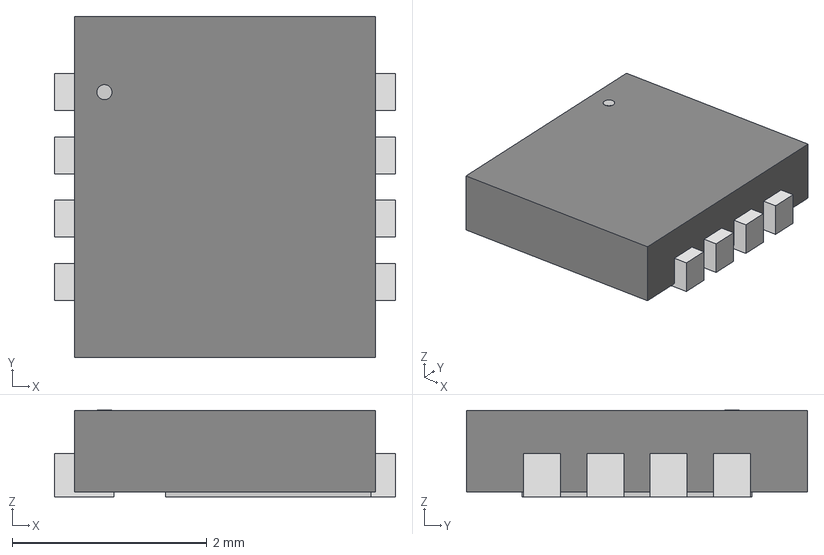
[picture p69: CAD file, 2024-05-21]
Hardware/KiCad Files/Components/3D/POWERFLAT_3P3X3P3_STM.step
3.51 x 3.51 x 0.892 mm
