gasiepgodoy/Open-Source-PLC/Hardware/KiCad Files/Components/3D/SN74LVC541APWR.stp

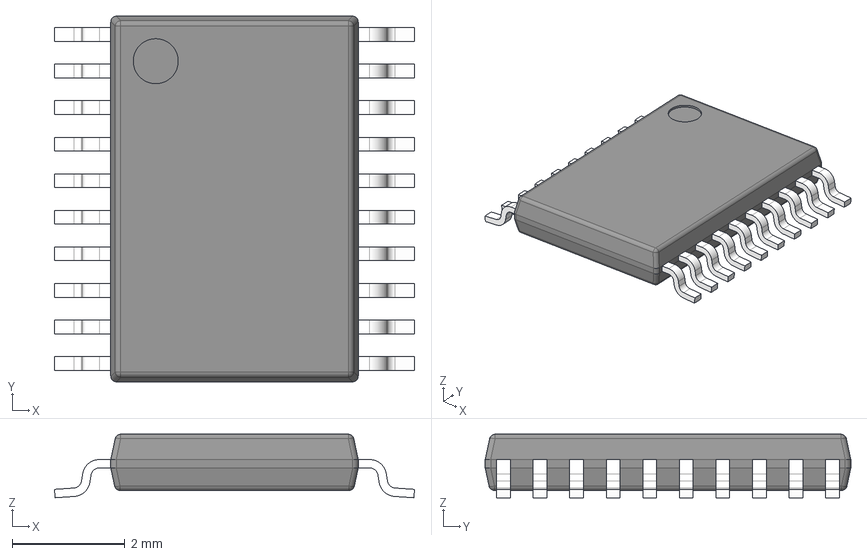
[picture p70: CAD file, 2024-05-21]
Hardware/KiCad Files/Components/3D/SN74LVC541APWR.stp
6.40 x 6.50 x 1.13 mm
BODY-TSSOP
LEAD-TSSOP x 20
PIN1
