gasiepgodoy/Open-Source-PLC/Hardware/KiCad Files/Components/3D/STL9P3LLH6.STEP

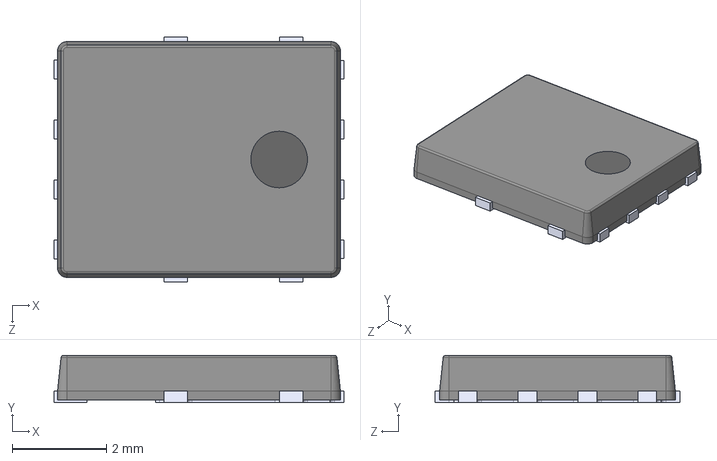
[picture p71: CAD file, 2024-05-21]
Hardware/KiCad Files/Components/3D/STL9P3LLH6.STEP
6.15 x 1.00 x 5.20 mm
