gasiepgodoy/Open-Source-PLC/Hardware/KiCad Files/Components/3D/HSMS-C197.STEP

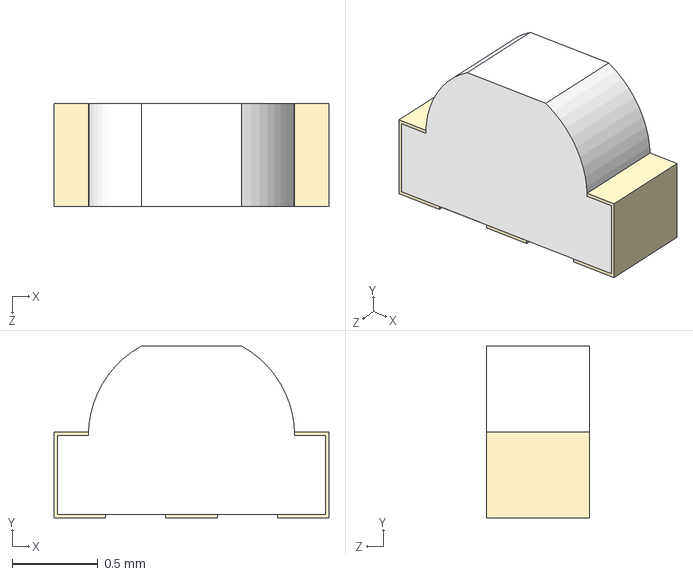
[picture p72: CAD file, 2024-05-21]
Hardware/KiCad Files/Components/3D/HSMS-C197.STEP
1.60 x 1.00 x 0.6 mm
