gasiepgodoy/Open-Source-PLC/Hardware/KiCad Files/Components/3D/0603ZD105KAT2A.stp

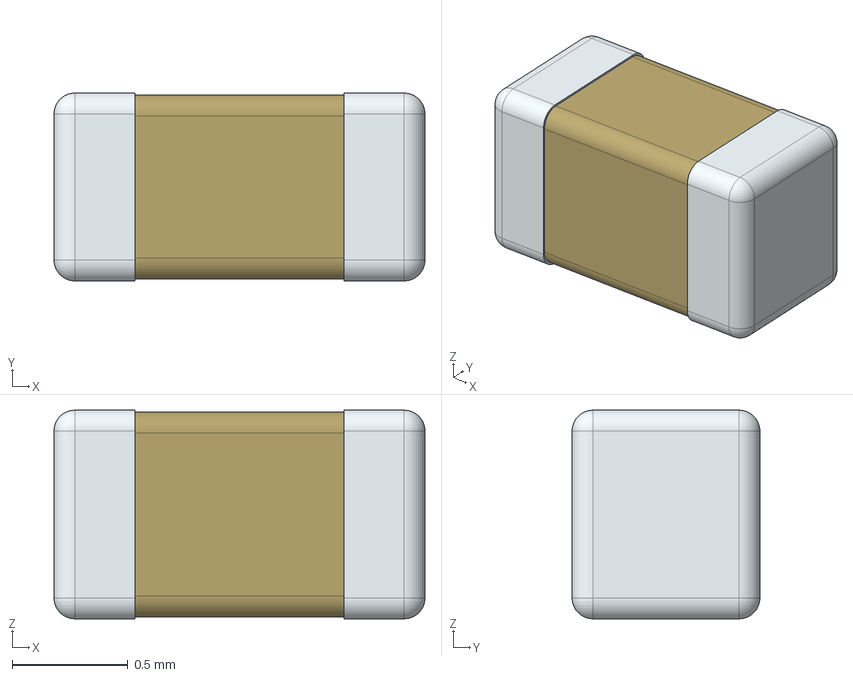
[picture p73: CAD file, 2024-05-21]
Hardware/KiCad Files/Components/3D/0603ZD105KAT2A.stp
1.60 x 0.81 x 0.9 mm
