gasiepgodoy/Open-Source-PLC/Hardware/KiCad Files/Components/3D/BLM15HG102SN1D.stp

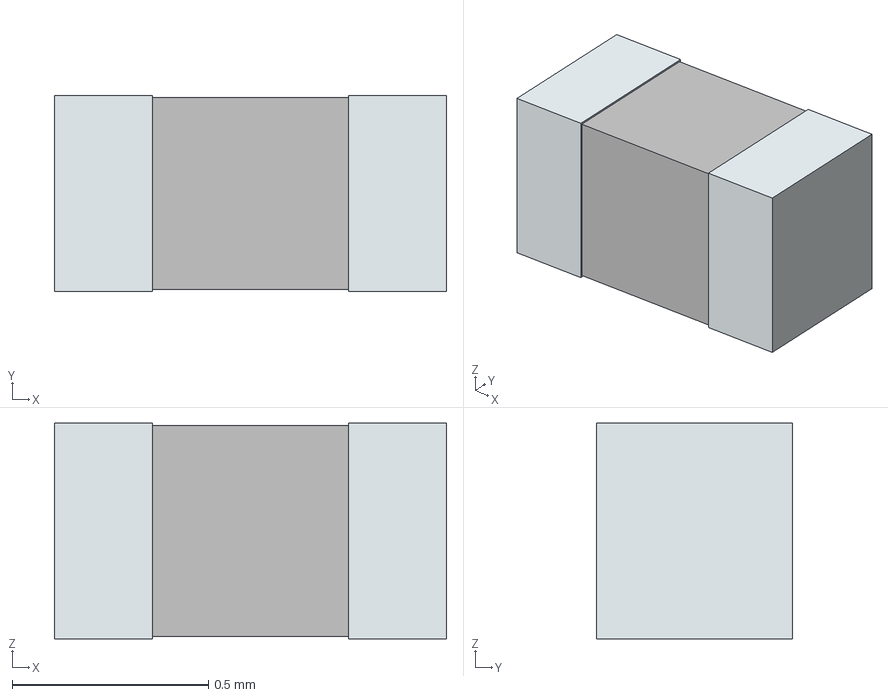
[picture p74: CAD file, 2024-05-21]
Hardware/KiCad Files/Components/3D/BLM15HG102SN1D.stp
1.00 x 0.5 x 0.55 mm
term1
term2
