gasiepgodoy/Open-Source-PLC/Hardware/KiCad Files/Components/3D/SRU2016-2R2Y.stp

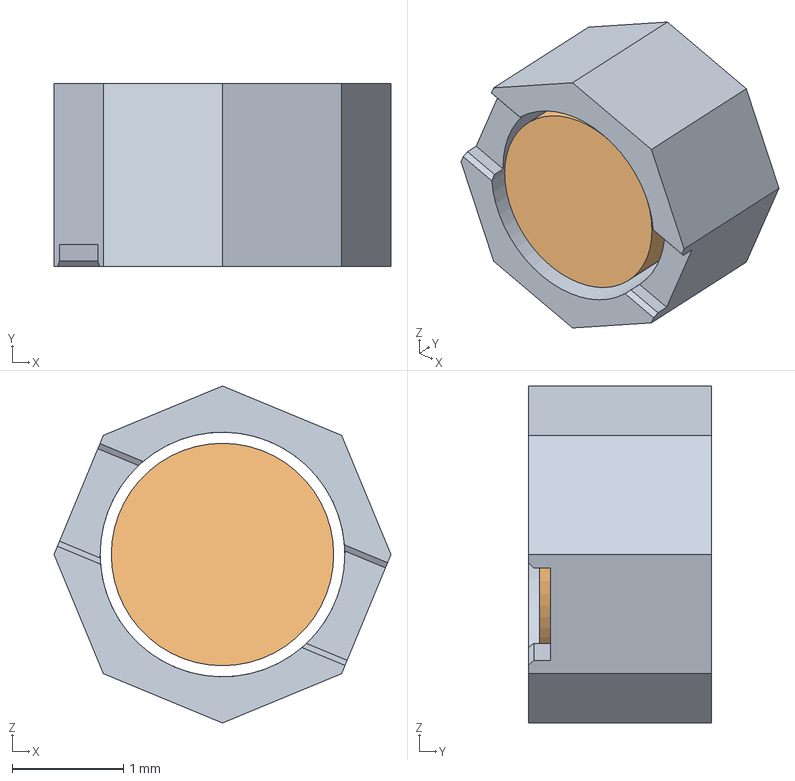
[picture p75: CAD file, 2024-05-21]
Hardware/KiCad Files/Components/3D/SRU2016-2R2Y.stp
3.03 x 1.65 x 3.03 mm
