gasiepgodoy/Open-Source-PLC/Hardware/KiCad Files/Components/3D/RR1220P-682-D.stp

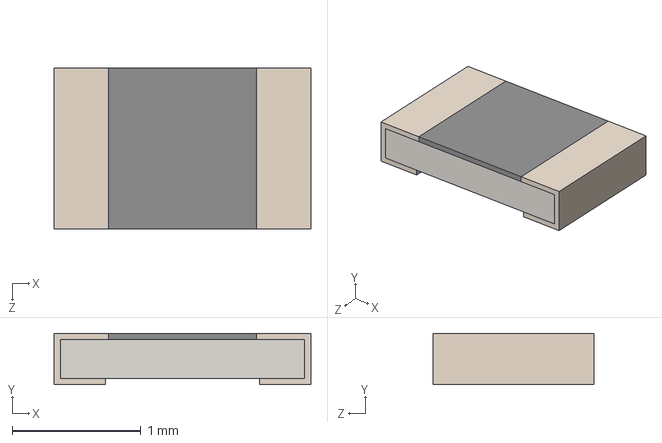
[picture p76: CAD file, 2024-05-21]
Hardware/KiCad Files/Components/3D/RR1220P-682-D.stp
2.00 x 0.4 x 1.25 mm
