gasiepgodoy/Open-Source-PLC/Hardware/KiCad Files/Components/3D/RB1-125BAG1A.stp

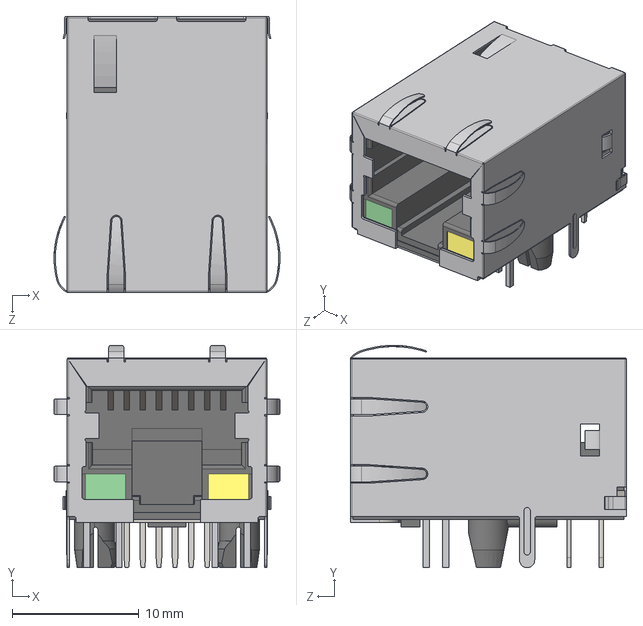
[picture p77: CAD file, 2024-05-21]
Hardware/KiCad Files/Components/3D/RB1-125BAG1A.stp
17.8 x 17.5 x 21.8 mm
