gasiepgodoy/Open-Source-PLC/Hardware/KiCad Files/Components/3D/RC0805JR-071K2L.stp

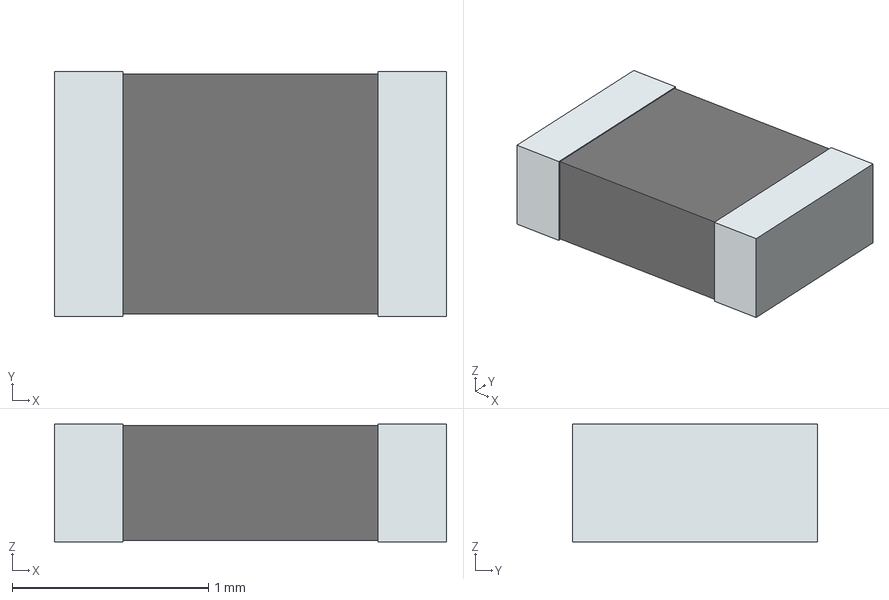
[picture p78: CAD file, 2024-05-21]
Hardware/KiCad Files/Components/3D/RC0805JR-071K2L.stp
2.00 x 1.25 x 0.6 mm
term1
term2
