gasiepgodoy/Open-Source-PLC/Hardware/KiCad Files/Components/3D/SN74HC165PW.stp

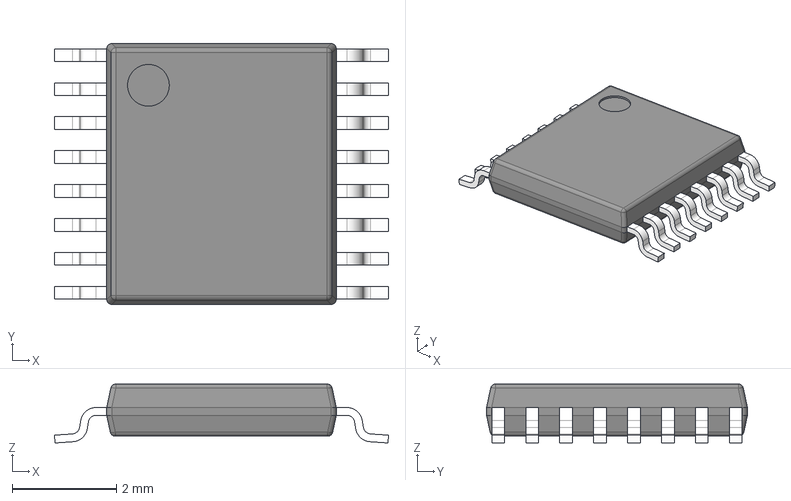
[picture p79: CAD file, 2024-05-21]
Hardware/KiCad Files/Components/3D/SN74HC165PW.stp
6.40 x 5.00 x 1.13 mm
BODY-TSSOP
LEAD-TSSOP x 16
PIN1
