gasiepgodoy/Open-Source-PLC/Hardware/KiCad Files/Components/3D/GRM188R61A106KE69J.stp

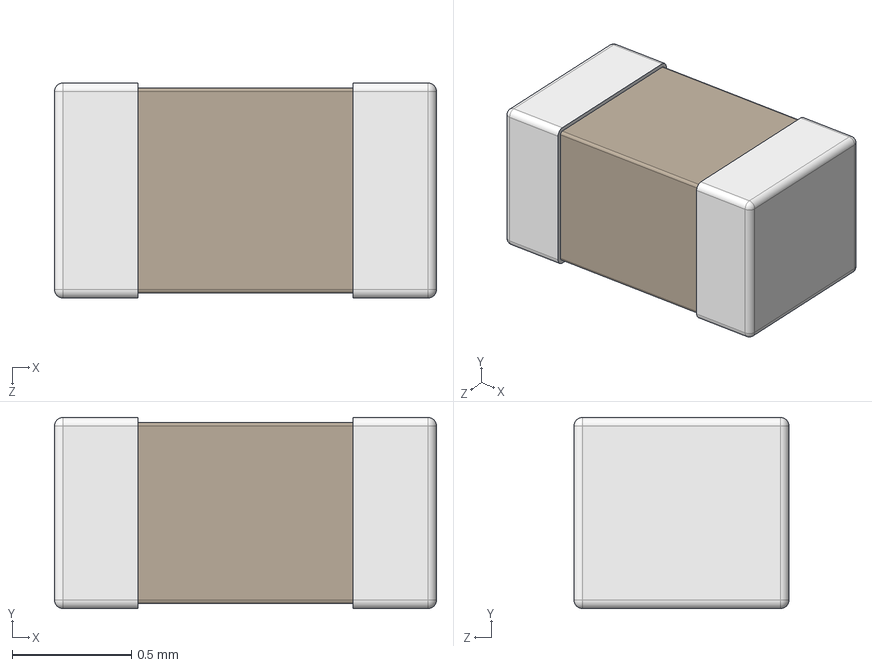
[picture p80: CAD file, 2024-05-21]
Hardware/KiCad Files/Components/3D/GRM188R61A106KE69J.stp
1.60 x 0.8 x 0.9 mm
