gasiepgodoy/Open-Source-PLC/Hardware/KiCad Files/Components/3D/AZ943-1CH-24DE.stp

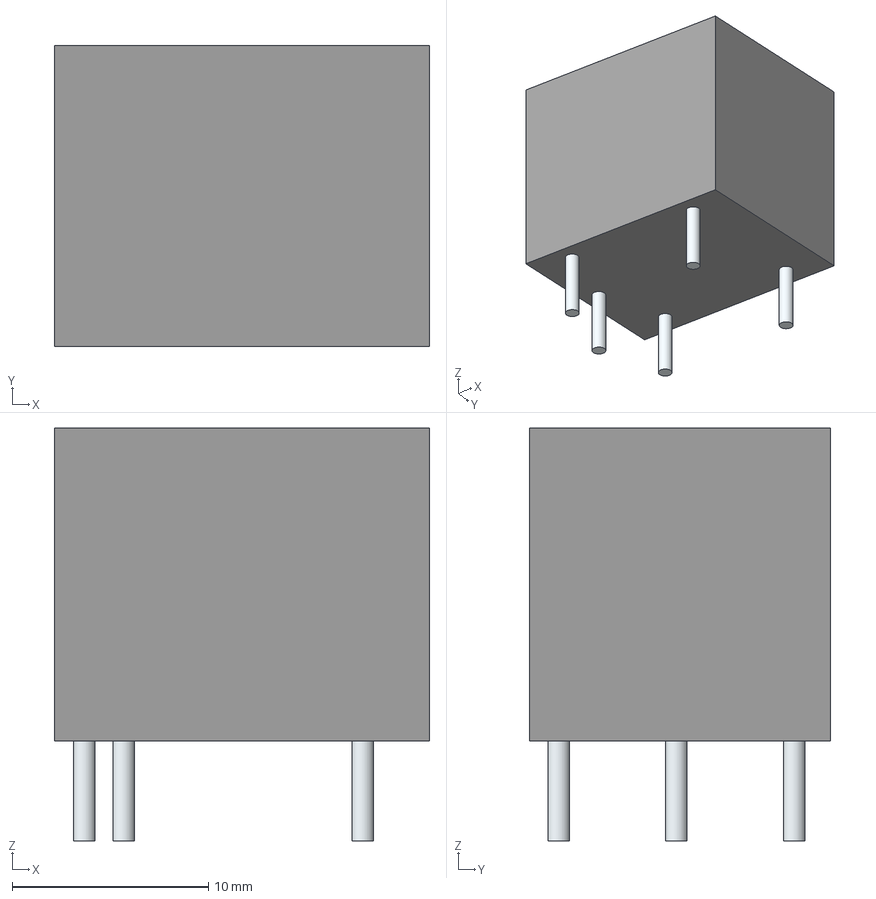
[picture p81: CAD file, 2024-05-21]
Hardware/KiCad Files/Components/3D/AZ943-1CH-24DE.stp
19.1 x 15.3 x 21.1 mm
Leads
