gasiepgodoy/Open-Source-PLC/Hardware/KiCad Files/Components/3D/VLS4020CX.stp

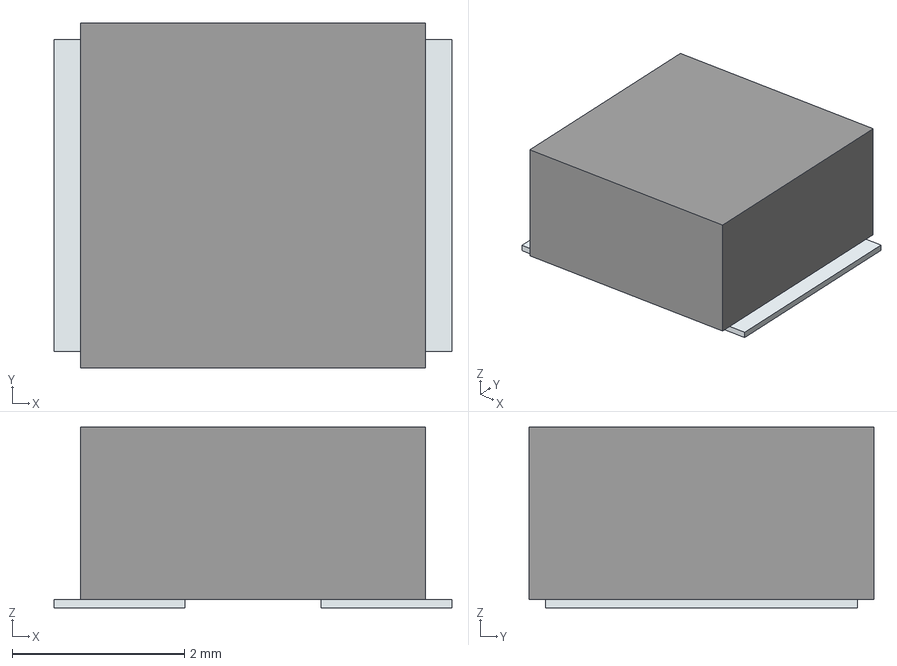
[picture p82: CAD file, 2024-05-21]
Hardware/KiCad Files/Components/3D/VLS4020CX.stp
4.62 x 4.00 x 2.10 mm
Pins
