gasiepgodoy/Open-Source-PLC/Hardware/KiCad Files/Components/3D/GRM188R71H103KA01D.stp

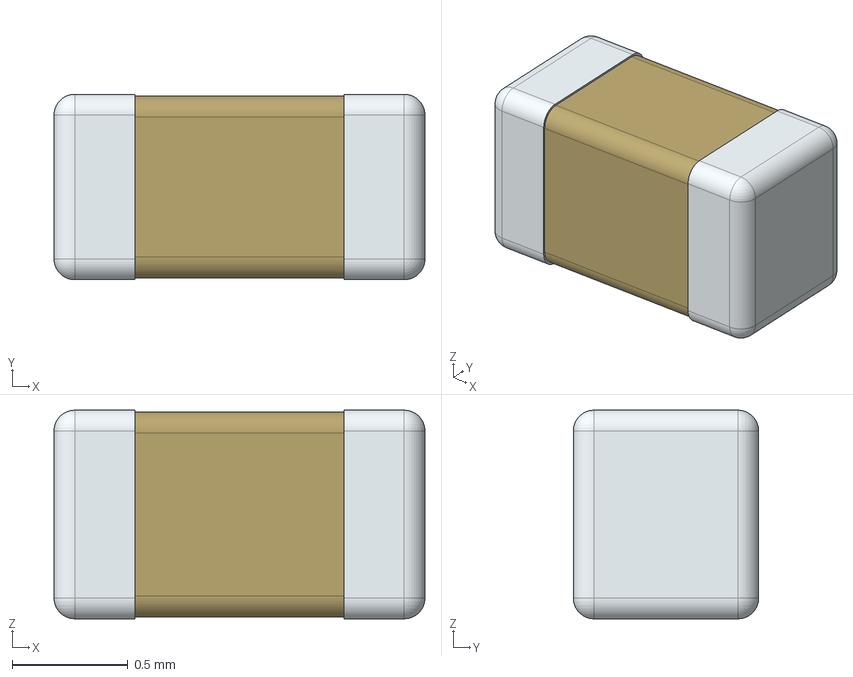
[picture p83: CAD file, 2024-05-21]
Hardware/KiCad Files/Components/3D/GRM188R71H103KA01D.stp
1.60 x 0.8 x 0.9 mm
