gasiepgodoy/Open-Source-PLC/Hardware/KiCad Files/Components/3D/LT6654AHS6-4.096TRMPBF.stp

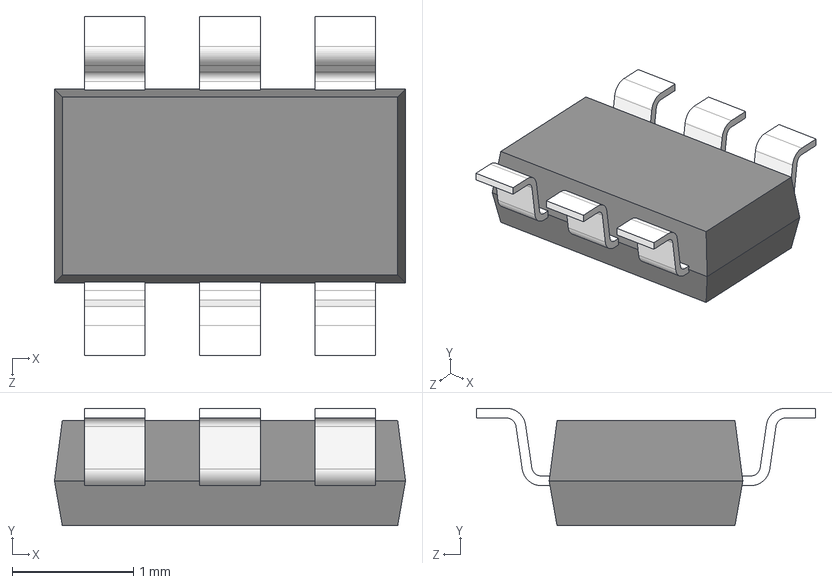
[picture p84: CAD file, 2024-05-21]
Hardware/KiCad Files/Components/3D/LT6654AHS6-4.096TRMPBF.stp
2.90 x 0.97 x 2.80 mm
