gasiepgodoy/Open-Source-PLC/Hardware/KiCad Files/Components/3D/AP3402KTTR-G1.stp

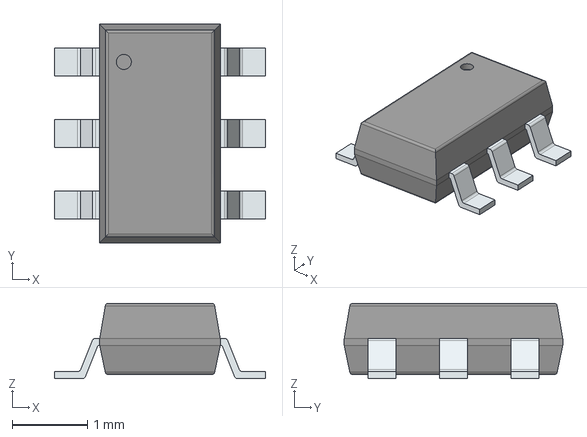
[picture p85: CAD file, 2024-05-21]
Hardware/KiCad Files/Components/3D/AP3402KTTR-G1.stp
2.80 x 2.90 x 1.00 mm
PinsArrayLR
