gasiepgodoy/Open-Source-PLC/Hardware/KiCad Files/Components/3D/RR1220P-4751-D-M.stp

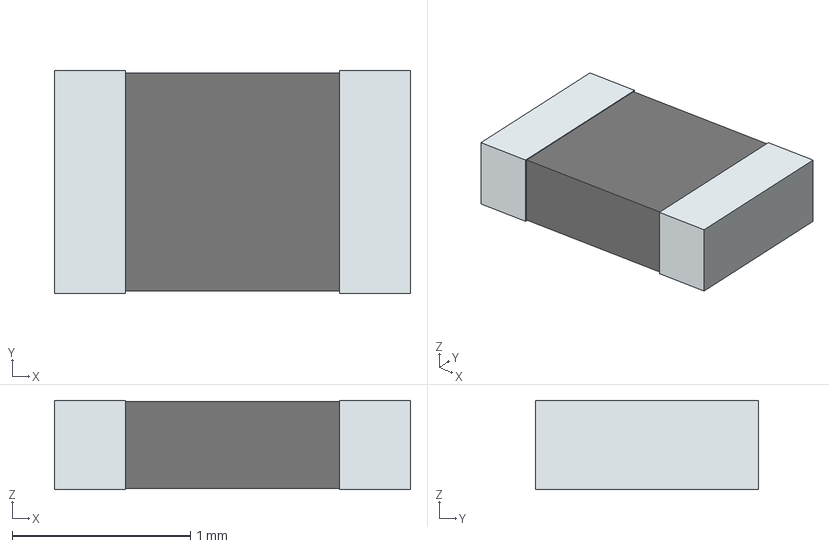
[picture p86: CAD file, 2024-05-21]
Hardware/KiCad Files/Components/3D/RR1220P-4751-D-M.stp
2.00 x 1.25 x 0.5 mm
term1
term2
