gasiepgodoy/Open-Source-PLC/Hardware/KiCad Files/Components/3D/74LVX32M.stp

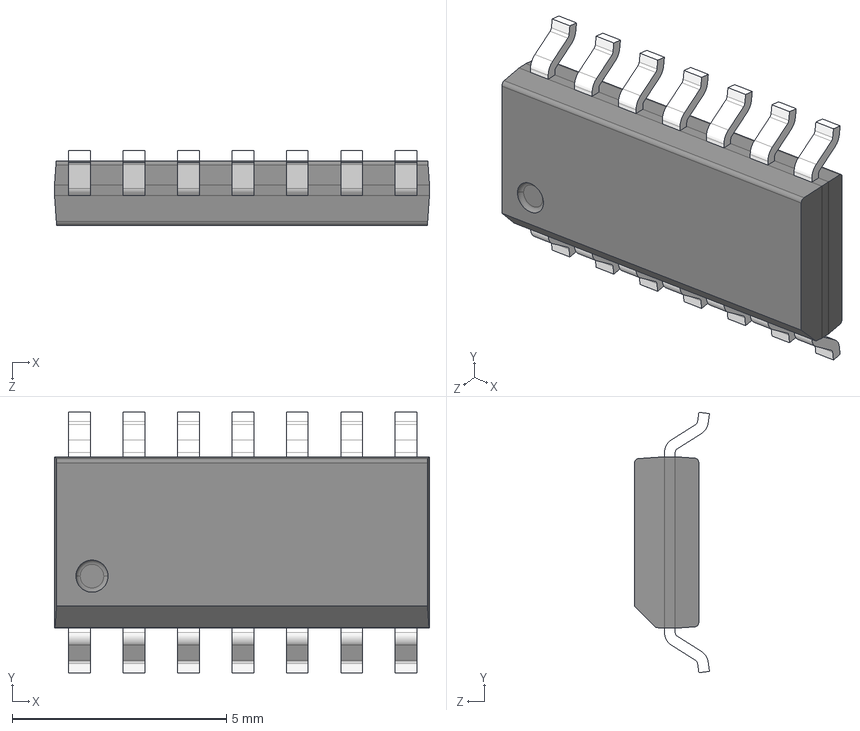
[picture p87: CAD file, 2024-05-21]
Hardware/KiCad Files/Components/3D/74LVX32M.stp
8.75 x 6.08 x 1.75 mm
