gasiepgodoy/Open-Source-PLC/Hardware/KiCad Files/Components/3D/VLS4015CX-220M-H.stp

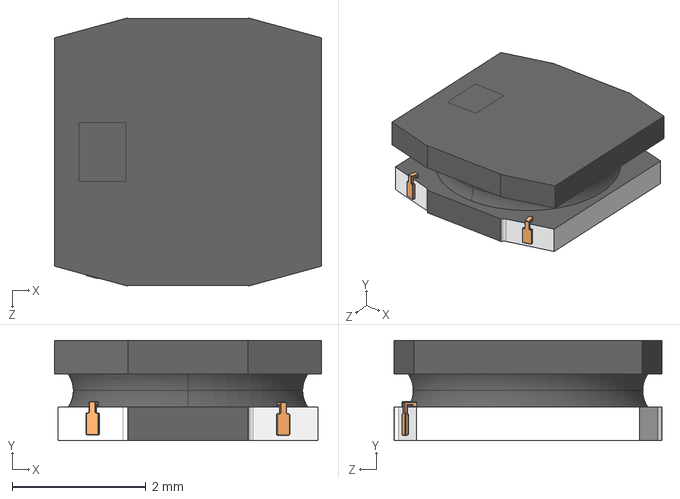
[picture p88: CAD file, 2024-05-21]
Hardware/KiCad Files/Components/3D/VLS4015CX-220M-H.stp
4.00 x 1.50 x 4.02 mm
