gasiepgodoy/Open-Source-PLC/Hardware/KiCad Files/Project/Analog_input.kicad_sch

## KiCad design Hardware/KiCad Files/Project/Analog_input.kicad_sch (2024-05-21)

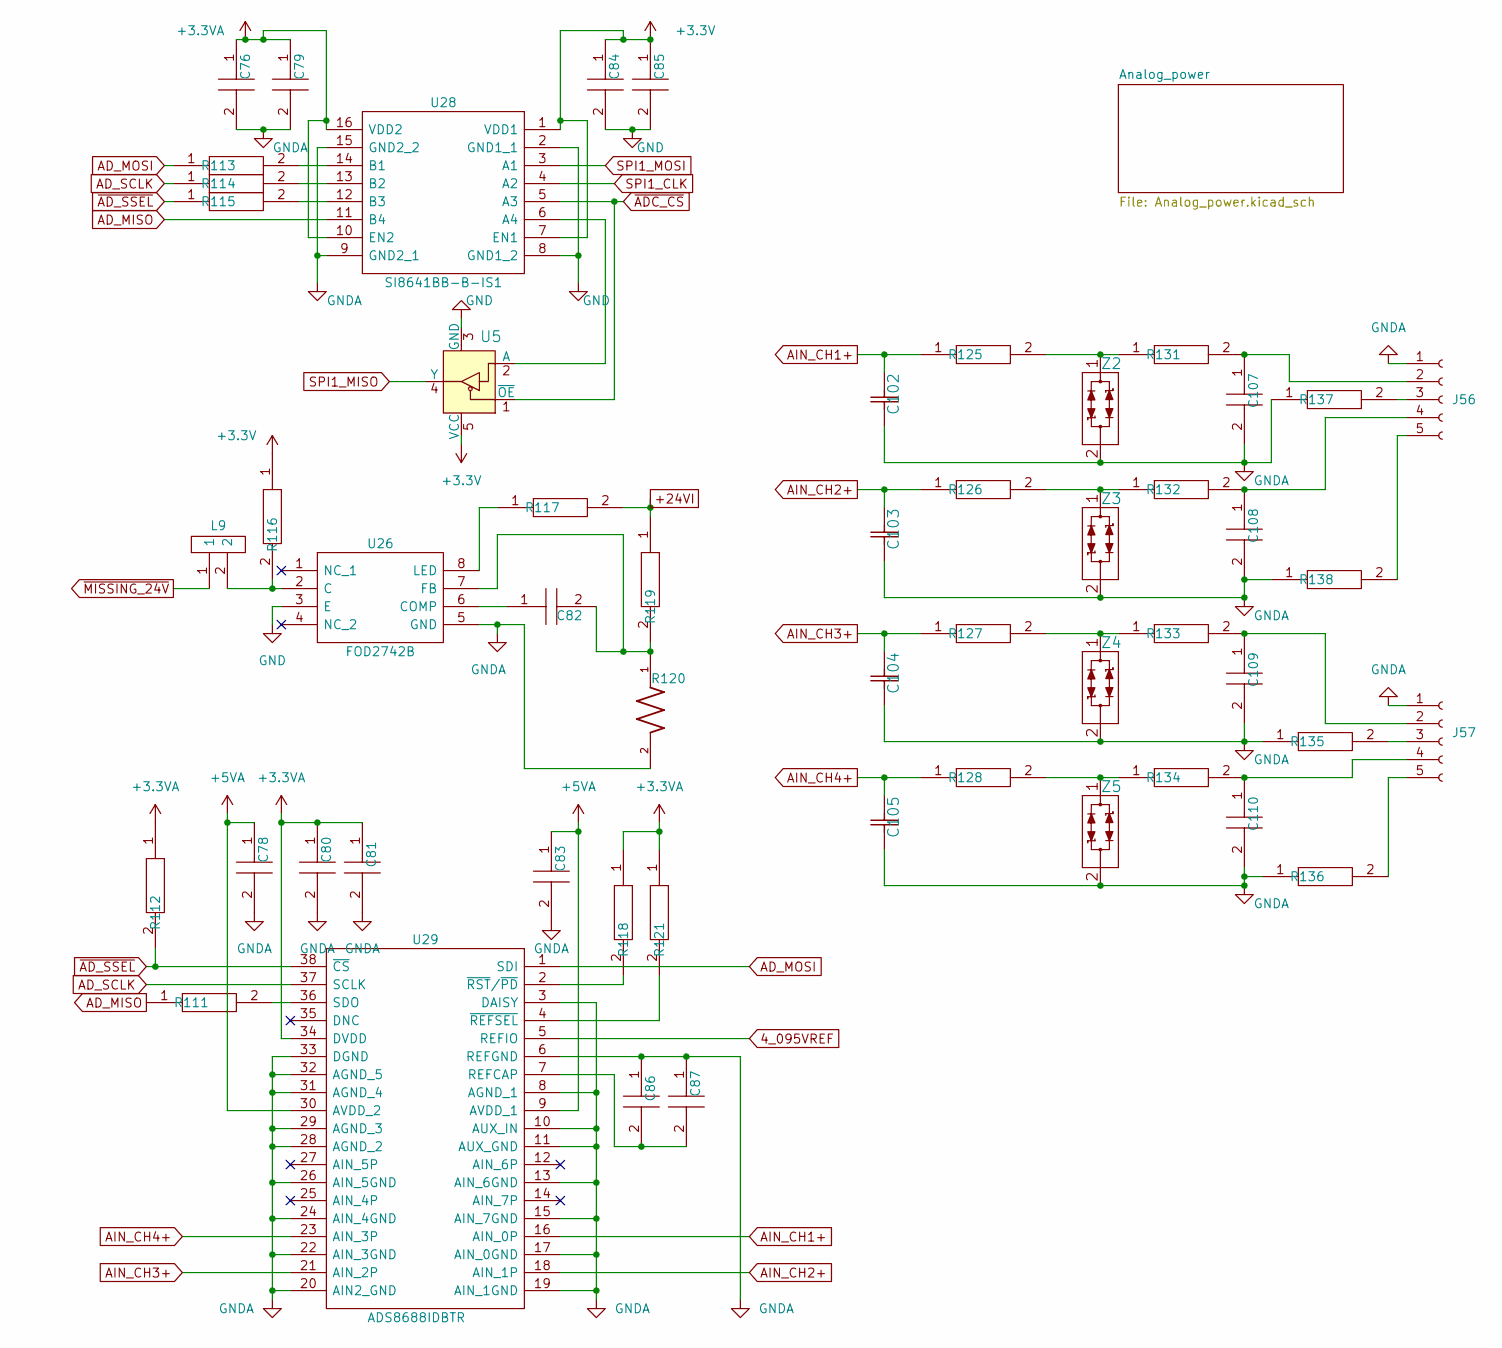
[picture p104: schematic Analog_input.kicad_sch]

Parts:
C76, C78, C80, C83, C85, C87: 0603ZD105KAT2A; C_0603_1608Metric; Manufacturer_Part_Number 0603ZD105KAT2A; Mouser Part Number 581-0603ZD105K
C79, C82, C84, C107, C108, C109, C110: GRM155R71H104KE14D; C_0402_1005Metric; Manufacturer_Part_Number GRM155R71H104KE14D; Mouser Part Number 81-GRM155R71H104KE4D
C81: GRM188R61A106KE69J; C_0603_1608Metric; Manufacturer_Part_Number GRM188R61A106KE69J; Mouser Part Number 81-GRM188R61A106KE9J
C86: CL31A226KAHNNNE; C_1206_3216Metric_Pad1.33x1.80mm_HandSolder; Manufacturer_Part_Number CL31A226KAHNNNE; Mouser Part Number 81-GRM31CR61E226KE5L
C102, C103, C104, C105: CC0603KRX7R9BB102; C_0603_1608Metric; Manufacturer_Part_Number CC0603KRX7R9BB102
J56, J57: 284512-5; SHDRRA5W82P0X350_1X5_1980X920X745P
L9: BLM21AG471SN1D; BLM21AG102BH1J; Manufacturer_Part_Number BLM21AG471SN1D; Mouser Part Number 81-BLM21AG471SN1D
R111, R113, R114, R115: RC0603FR-0733RL; R_0603_1608Metric; Manufacturer_Part_Number RC0603FR-0733RL
R112, R118, R121: ERJ-3EKF4992V; R_0603_1608Metric; Manufacturer_Part_Number ERJ-3EKF4992V; Mouser Part Number 667-ERJ-3EKF4992V
R116: RR1220P-4751-D-M; R_0805_2012Metric; Manufacturer_Part_Number RR1220P-4751-D-M
R117, R119: RR1220P-682-D; R_0805_2012Metric; Manufacturer_Part_Number RR1220P-682-D
R120: RR1220P-1151-D-M; R_0805_2012Metric
R125, R126, R127, R128: ERJ-3EKF1001V; R_0603_1608Metric; Manufacturer_Part_Number ERJ-3EKF1001V; Mouser Part Number 667-ERJ-3EKF1001V
R131, R132, R133, R134: ERJ-6ENF1000V; R_0805_2012Metric; Manufacturer_Part_Number ERJ-6ENF1000V; Mouser Part Number 667-ERJ-6ENF1000V
R135, R136, R137, R138: TNPW1206250RBEEN; R_0402_1005Metric_Pad0.72x0.64mm_HandSolder
U5: SN74LVC1G125DBVR; SOT-753; MPN SN74LVC1G125DBVR; Digi-Key_PN 296-11603-1-ND
U26: FOD2742B; SOIC127P594X363-8N; Manufacturer_Part_Number FOD2742B; Mouser Part Number 512-FOD2742B
U28: SI8641BB-B-IS1; SOIC127P600X175-16N; Manufacturer_Part_Number SI8641BB-B-IS1; Mouser Part Number 634-SI8641AB-B-IS1
U29: ADS8688IDBTR; SOP50P640X120-38N; Manufacturer_Part_Number ADS8688IDBTR; Mouser Part Number 595-ADS8688IDBTR
Z2, Z3, Z4, Z5: SP4022-01FTG-C

Connections:
4_095VREF: U29.5 (REFIO)
+3.3V: C84.1, C85.1, R116.1, U5.5 (VCC), U28.1 (VDD1), U28.7 (EN1)
+3.3VA: C76.1, C79.1, C80.1, C81.1, R112.1, R118.1, R121.1, U28.10 (EN2), U28.16 (VDD2), U29.34 (DVDD)
+5VA: C78.1, C83.1, U29.9 (AVDD_1), U29.30 (AVDD_2)
+24VI: R117.2, R119.1
AD_MISO: R111.1, U28.11 (B4)
AD_MOSI: R113.1, U29.1 (SDI)
AD_SCLK: R114.1, U29.37 (SCLK)
AIN_CH1+: C102.1, R125.1, U29.16 (AIN_0P)
AIN_CH2+: C103.1, R126.1, U29.18 (AIN_1P)
AIN_CH3+: C104.1, R127.1, U29.21 (AIN_2P)
AIN_CH4+: C105.1, R128.1, U29.23 (AIN_3P)
GND: C84.2, C85.2, U5.3 (GND), U26.3 (E), U28.2 (GND1_1), U28.8 (GND1_2)
GNDA: C76.2, C78.2, C79.2, C80.2, C81.2, C83.2, C86.1, C87.1, C102.2, C103.2, C104.2, C105.2, C107.2, C108.2, C109.2, C110.2, J56.1, J57.1, R120.2, R135.1, R136.1, R137.1, R138.1, U26.5 (GND), U28.9 (GND2_1), U28.15 (GND2_2), U29.3 (DAISY), U29.6 (REFGND), U29.8 (AGND_1), U29.10 (AUX_IN), U29.11 (AUX_GND), U29.13 (AIN_6GND), U29.15 (AIN_7GND), U29.17 (AIN_0GND), U29.19 (AIN_1GND), U29.20 (AIN2_GND), U29.22 (AIN_3GND), U29.24 (AIN_4GND), U29.26 (AIN_5GND), U29.28 (AGND_2), U29.29 (AGND_3), U29.31 (AGND_4), U29.32 (AGND_5), U29.33 (DGND), Z2.2, Z3.2, Z4.2, Z5.2
unnamed: C82.1, U26.6 (COMP)
unnamed: C82.2, R119.2, R120.1, U26.7 (FB)
unnamed: C86.2, C87.2, U29.7 (REFCAP)
unnamed: C107.1, J56.2, R131.2
unnamed: C108.1, J56.4, R132.2
unnamed: C109.1, J57.2, R133.2
unnamed: C110.1, J57.4, R134.2
unnamed: J56.3, R137.2
unnamed: J56.5, R138.2
unnamed: J57.3, R135.2
unnamed: J57.5, R136.2
unnamed: L9.2, R116.2, U26.2 (C)
unnamed: R111.2, U29.36 (SDO)
unnamed: R113.2, U28.14 (B1)
unnamed: R114.2, U28.13 (B2)
unnamed: R115.2, U28.12 (B3)
unnamed: R117.1, U26.8 (LED)
unnamed: R118.2, U29.2 (~RST/~PD)
unnamed: R121.2, U29.4 (~REFSEL)
unnamed: R125.2, R131.1, Z2.1
unnamed: R126.2, R132.1, Z3.1
unnamed: R127.2, R133.1, Z4.1
unnamed: R128.2, R134.1, Z5.1
unnamed: U5.2 (A), U28.6 (A4)
SPI1_CLK: U28.4 (A2)
SPI1_MISO: U5.4 (Y)
SPI1_MOSI: U28.3 (A1)
~ADC_CS: U5.1 (~OE), U28.5 (A3)
~AD_SSEL: R112.2, R115.1, U29.38 (~CS)
~MISSING_24V: L9.1
