gasiepgodoy/Open-Source-PLC/Hardware/KiCad Files/Project/Analog_power.kicad_sch

## KiCad design Hardware/KiCad Files/Project/Analog_power.kicad_sch (2024-05-21)

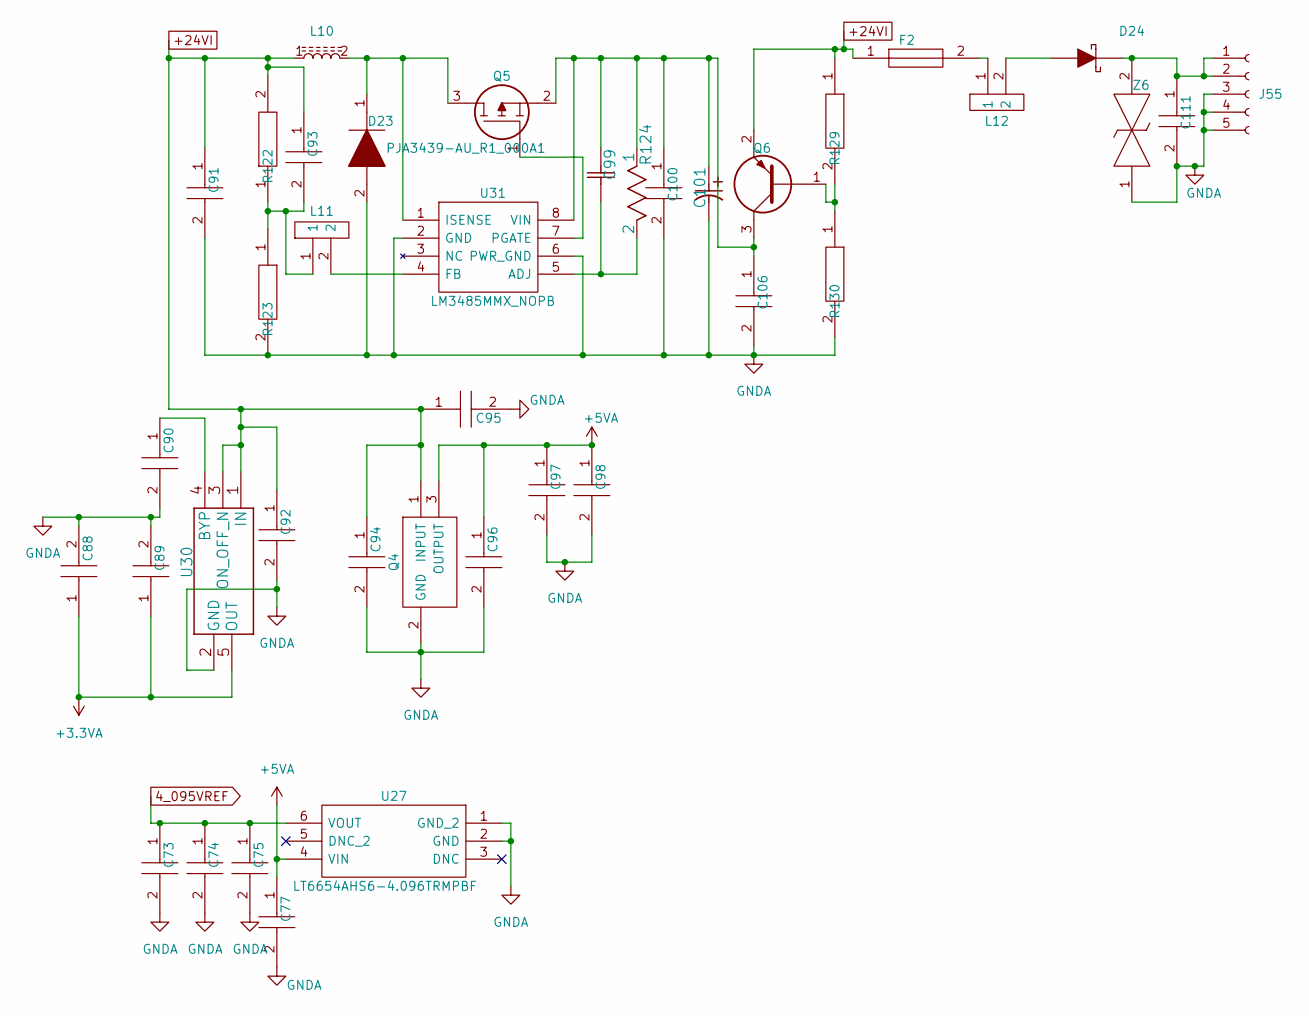
[picture p105: schematic Analog_power.kicad_sch]

Parts:
C73, C77, C100, C106: GRM155R71H104KE14D; C_0402_1005Metric; Manufacturer_Part_Number GRM155R71H104KE14D; Mouser Part Number 81-GRM155R71H104KE4D
C74, C75: CC0603KRX5R6BB475; C_0603_1608Metric; Manufacturer_Part_Number LMK107BJ475KA-T; Mouser Part Number 963-LMK107BJ475KA-T
C88, C98: 0603ZD105KAT2A; C_0603_1608Metric; Manufacturer_Part_Number 0603ZD105KAT2A; Mouser Part Number 581-0603ZD105K
C89, C92, C95, C97: 0805X475K250CT; C_0805_2012Metric; Manufacturer_Part_Number 0805X475K250CT; Mouser Part Number 667-ECJ-2FB1E475M
C90: C1005X7R1E103K050BB; C_0402_1005Metric; Manufacturer_Part_Number C1005X7R1E103K050BB; Mouser Part Number 810-C1005X7R1E103K
C91: UWX1C101MCL1GB; CP_Elec_6.3x5.4_Nichicon; Manufacturer_Part_Number UWX1C101MCL1GB; Mouser Part Number 647-UWX1C101MCL1
C93: 08055A471JAT2A; C_0805_2012Metric; Manufacturer_Part_Number 08055A471JAT2A; Mouser Part Number 581-08055A471J
C94, C96: GJ821BR61E106KE11L; CAPC2012X145N; Manufacturer_Part_Number GJ821BR61E106KE11L; Mouser Part Number 81-GJ821BR61E106KE1L
C99: CC0603KRX7R9BB102; C_0603_1608Metric; Manufacturer_Part_Number CC0603KRX7R9BB102
C101: UWD1H220MCL1GS; CP_Elec_6.3x5.8
C111: GCM21BR72A104KA37L; C_0805_2012Metric; Manufacturer_Part_Number GCM21BR72A104KA37L; Mouser Part Number 81-GCM21BR72A104KA7L
D23: B1100-13-F; DIOM5226X230N; Manufacturer_Part_Number B1100-13-F; Mouser Part Number 621-B1100-F
D24: B340-13-F; DO-214AC; Manufacturer_Part_Number B340-13-F; Mouser Part Number 863-MBRS340T3G
F2: 0ZCF0100AF2A; FUSC7451X170N; Manufacturer_Part_Number 0ZCF0100AF2A; Mouser Part Number 530-0ZCF0100AF2A
J55: 284512-5; SHDRRA5W82P0X350_1X5_1980X920X745P
L10: VLS4015CX-220M-H; VLS4015CX100MH
L11, L12: MPZ2012S331AT000; INDC2012X105N; Manufacturer_Part_Number MPZ2012S331AT; Mouser Part Number N/A
Q4: L7805CD2T-TR; L7805CD2T; Manufacturer_Part_Number L7805CD2T-TR; Mouser Part Number 511-L7805CD2T-TR
Q5: PJA3439-AU_R1_000A1; SOT95P237X112-3N; Manufacturer_Part_Number PJA3439-AU_R1_000A1; Mouser Part Number 512-FDN5618P
Q6: MMBT2907A-7-F; SOT96P240X100-3N; Manufacturer_Part_Number MMBT2907A-7-F; Mouser Part Number 621-MMBT2907A-F
R122: CPF0603B40K2E1; R_0603_1608Metric
R123, R129: RC0402FR-0710KL; R_0402_1005Metric_Pad0.72x0.64mm_HandSolder; Manufacturer_Part_Number RC0402FR-0710KL; Mouser Part Number 603-RC0402FR-0710KL
R124: ERJ-3EKF7502V; R_0603_1608Metric
R130: ERJ-3EKF4992V; R_0603_1608Metric; Manufacturer_Part_Number ERJ-3EKF4992V; Mouser Part Number 667-ERJ-3EKF4992V
U27: LT6654AHS6-4.096TRMPBF; SOT95P280X100-6N; Manufacturer_Part_Number LT6654AHS6-4.096TRMPBF
U30: LP2992IM5-3.3/NOPB; LP2992IM5-3.3&slash_NOPB
U31: LM3485MMX_NOPB; SOP65P490X110-8N; Manufacturer_Part_Number LM3485MMX/NOPB; Mouser Part Number 926-LM3485MMX/NOPB
Z6: SMAJ33CA-TR; DIONM5226X220N; Manufacturer_Part_Number SMAJ33CA-TR; Mouser Part Number 863-SZ1SMA33CAT3G

Connections:
4_095VREF: C73.1, C74.1, C75.1, U27.6 (VOUT)
+3.3VA: C88.1, C89.1, U30.5 (OUT)
+5VA: C77.1, C96.1, C97.1, C98.1, Q4.3 (OUTPUT), U27.4 (VIN)
+24VI: C91.1, C92.1, C93.1, C94.1, C95.1, F2.1, L10.1, Q4.1 (INPUT), Q6.2, R122.2, R129.1, U30.1 (IN), U30.3 (ON_OFF_N)
GNDA: C73.2, C74.2, C75.2, C77.2, C88.2, C89.2, C90.2, C91.2, C92.2, C94.2, C95.2, C96.2, C97.2, C98.2, C100.2, C101.2, C106.2, C111.2, D23.2, J55.3, J55.4, J55.5, Q4.2 (GND), R123.2, R130.2, U27.1 (GND_2), U27.2 (GND), U30.2 (GND), U31.2 (GND), U31.6 (PWR_GND), Z6.1
unnamed: C90.1, U30.4 (BYP)
unnamed: C93.2, L11.1, R122.1, R123.1
unnamed: C99.2, R124.2, U31.5 (ADJ)
unnamed: C99.1, C100.1, C101.1, C106.1, Q5.2, Q6.3, R124.1, U31.8 (VIN)
unnamed: C111.1, D24.K, J55.1, J55.2, Z6.2
unnamed: D23.1, L10.2, Q5.3, U31.1 (ISENSE)
unnamed: D24.A, L12.2
unnamed: F2.2, L12.1
unnamed: L11.2, U31.4 (FB)
unnamed: Q5.1, U31.7 (PGATE)
unnamed: Q6.1, R129.2, R130.1
