gasiepgodoy/Open-Source-PLC/Hardware/KiCad Files/Project/Communication.kicad_sch

## KiCad design Hardware/KiCad Files/Project/Communication.kicad_sch (2024-05-21)

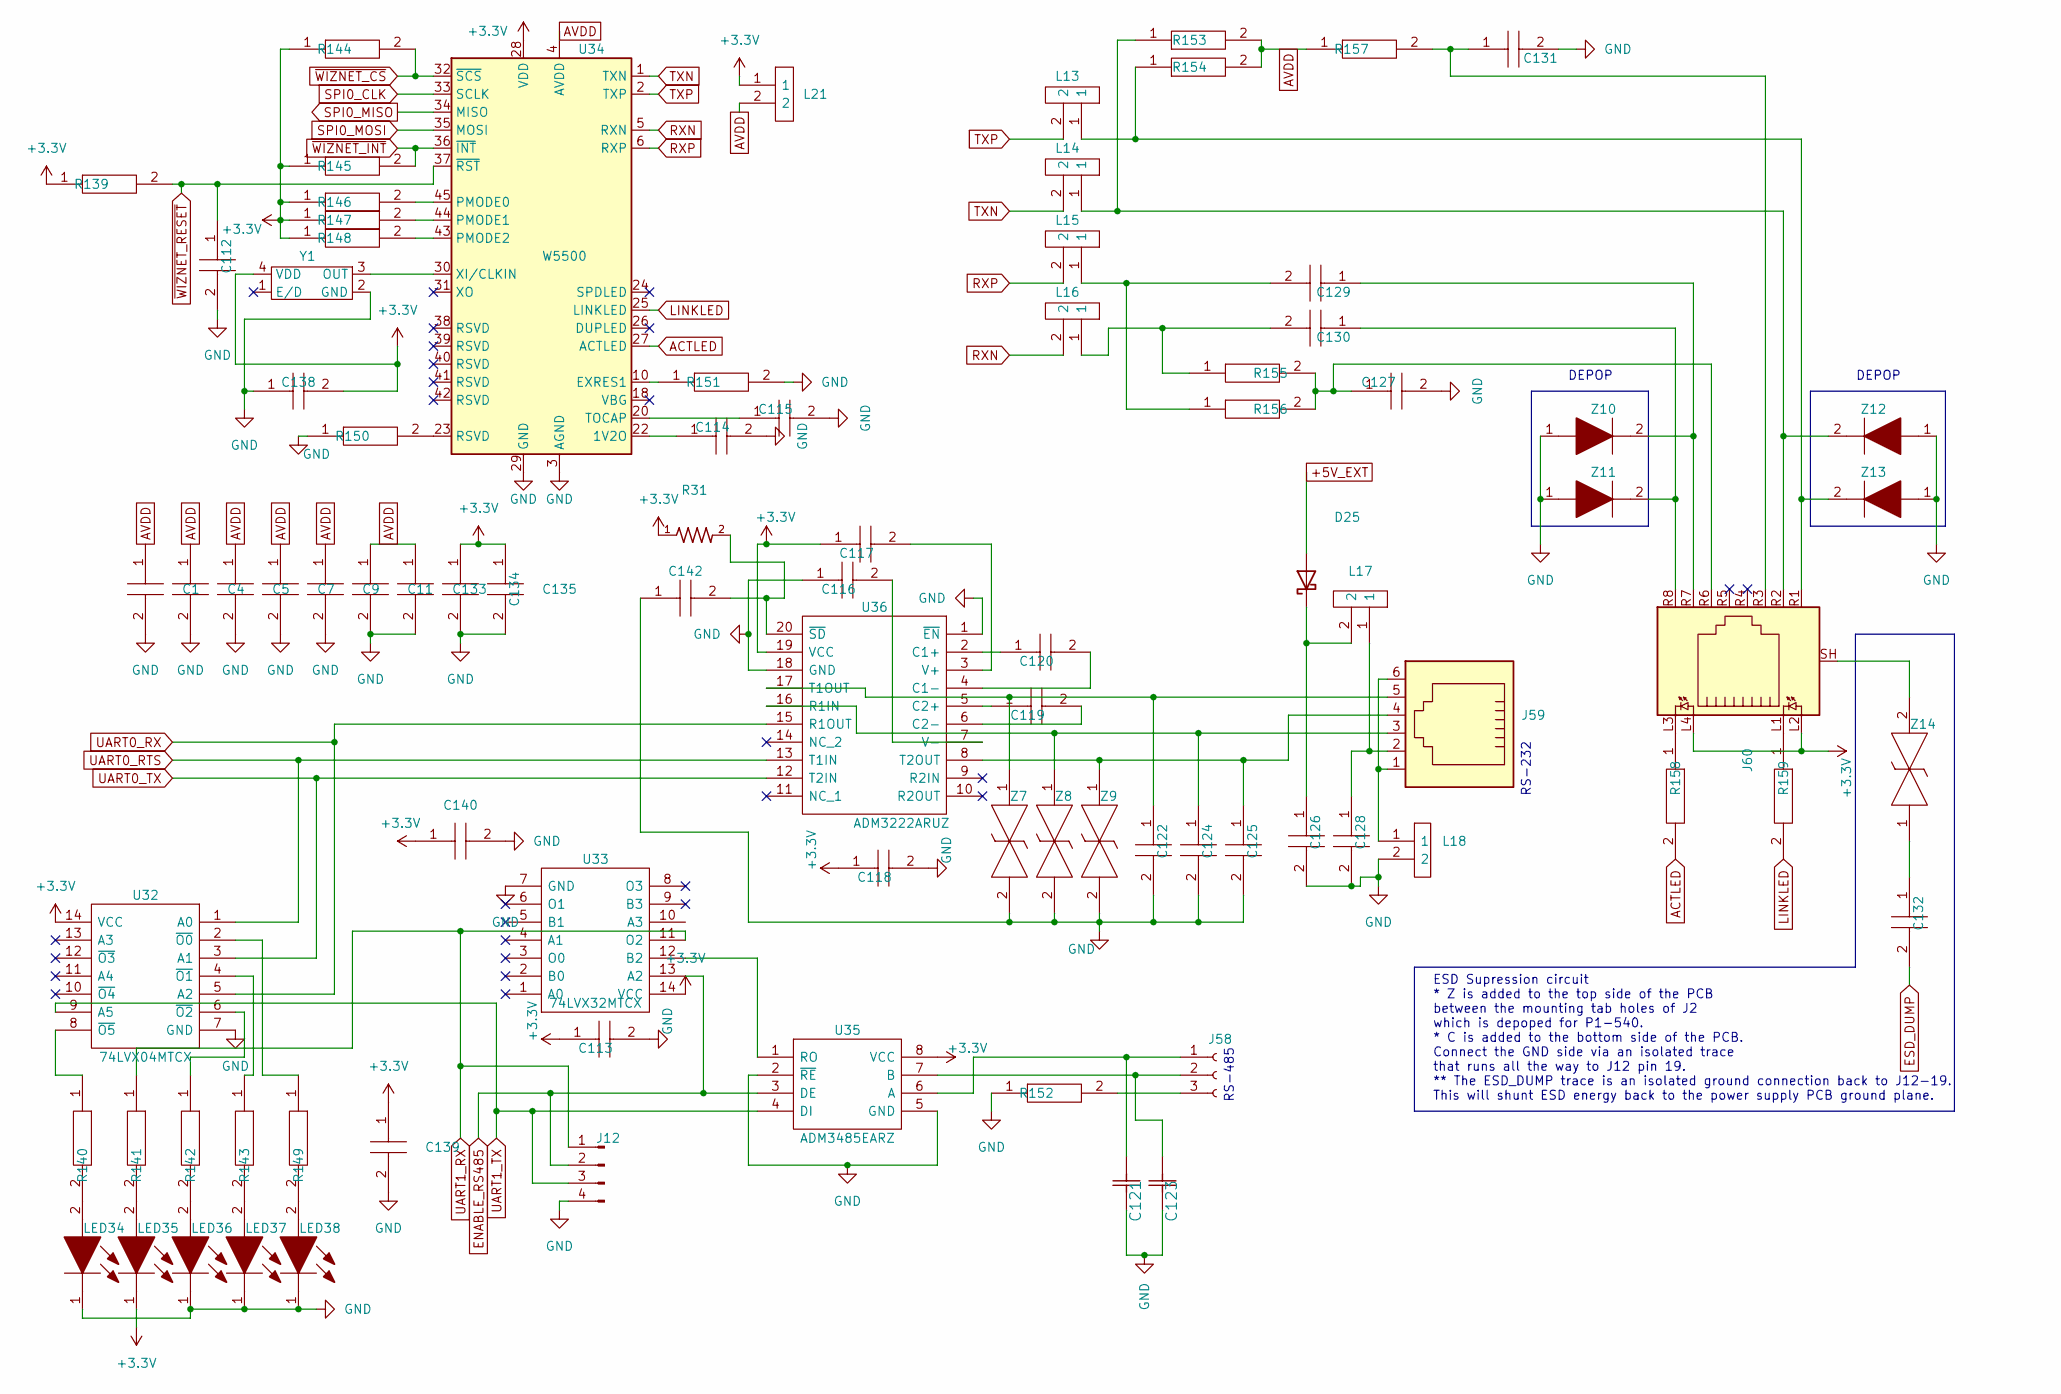
[picture p106: schematic Communication.kicad_sch]

Parts:
C1, C4, C5, C7, C9, C11, C112, C113, C116, C117, C118, C119, C120, C126, C128, C131, C135, C139, C140: GRM155R71H104KE14D; C_0402_1005Metric; Manufacturer_Part_Number GRM155R71H104KE14D; Mouser Part Number 81-GRM155R71H104KE4D
C114, C127, C129, C130, C138: C1005X7R1E103K050BB; C_0402_1005Metric; Manufacturer_Part_Number C1005X7R1E103K050BB; Mouser Part Number 810-C1005X7R1E103K
C115: CC0603KRX5R6BB475; C_0603_1608Metric; Manufacturer_Part_Number LMK107BJ475KA-T; Mouser Part Number 963-LMK107BJ475KA-T
C121, C123: CC0603KRX7R9BB102; C_0603_1608Metric; Manufacturer_Part_Number CC0603KRX7R9BB102
C122, C124, C125: CL10C470JB8NNNC; C_0402_1005Metric; Manufacturer_Part_Number GRM1552C1H470JZ01C; Mouser Part Number N/A
C132: 12061A222JAT2A; C_1206_3216Metric; Manufacturer_Part_Number 12061A222JAT2A; Mouser Part Number 581-12061A222JAT2A
C133, C134: GRM188R61A106KE69J; C_0603_1608Metric; Manufacturer_Part_Number GRM188R61A106KE69J; Mouser Part Number 81-GRM188R61A106KE9J
C142: 0603ZD105KAT2A; C_0603_1608Metric; Manufacturer_Part_Number 0603ZD105KAT2A; Mouser Part Number 581-0603ZD105K
D25: MBR0530-TP; D_SOD-123; Manufacturer_Part_Number MBR0530-TP; Mouser Part Number 863-MBR0530T1G
J12: PR20204VBNN; PinHeader_1x04_P2.54mm_Vertical
J58: 796644-3; TE_796644-3
J59: 1705950-1; RJ12_Amphenol_54601
J60: RB1-125BAG1A; RJ45_Female_RB1-125BAG1A
L13, L14, L15, L16: BLM18PG330SN1D; BLM18AG102BH1D; Manufacturer_Part_Number BLM18PG330SN1D; Mouser Part Number 81-BLM18PG330SN1D
L17, L18: BLM21PG600SN1D; BLM21AG102BH1J; Manufacturer_Part_Number BLM21PG600SN1D; Mouser Part Number 81-BLM21P600S
L21: BLM18BD221SN1D; BLM18AG102BH1D; Manufacturer_Part_Number BLM18BD221SN1D; Mouser Part Number 81-BLM18BD221SN1D
LED34, LED35, LED36, LED37, LED38: HSMG-C680; LEDC1608X60N; Manufacturer_Part_Number HSMG-C680
R31: ERA-3AEB104V; R_0603_1608Metric
R139, R144, R145, R146, R147, R148, R150: RC0402FR-0710KL; R_0402_1005Metric_Pad0.72x0.64mm_HandSolder; Manufacturer_Part_Number RC0402FR-0710KL; Mouser Part Number 603-RC0402FR-0710KL
R140, R141, R142, R143, R149: RC0603JR-07100RL; R_0603_1608Metric; Manufacturer_Part_Number RC0603JR-07100RL; Mouser Part Number 603-RC0603JR-07100RL
R151: RC0603FR-0712K4L; R_0603_1608Metric; Manufacturer_Part_Number RC0603FR-0712K4L; Mouser Part Number 603-RC0603FR-0712K4L
R152: RC0603JR-070RL; R_0603_1608Metric; Manufacturer_Part_Number RC0603JR-070RL; Mouser Part Number 603-RC0603JR-070RL
R153, R154, R155, R156: ERJ-3EKF49R9V; R_0603_1608Metric; Manufacturer_Part_Number ERJ-3EKF49R9V; Mouser Part Number 667-ERJ-3EKF49R9V
R157: RK73H1ETTP10R0F; R_0402_1005Metric_Pad0.72x0.64mm_HandSolder; Manufacturer_Part_Number RK73H1ETTP10R0F; Mouser Part Number 660-RK73H1ETTP10R0F
R158, R159: ERA-2AED331X; R_0402_1005Metric_Pad0.72x0.64mm_HandSolder; Manufacturer_Part_Number ERA-2AED331X
U32: 74LVX04MTCX; SOIC127P600X175-14N; Manufacturer_Part_Number 74LVX04M
U33: 74LVX32MTCX; SOIC127P600X175-14N; Manufacturer_Part_Number 74LVX32M; Mouser Part Number 512-74LVX32M
U34: W5500; LQFP-48_7x7mm_P0.5mm
U35: ADM3485EARZ; SOIC127P600X175-8N; Manufacturer_Part_Number ADM3485EARZ; Mouser Part Number 584-ADM3485EARZ
U36: ADM3222ARUZ; SOP65P640X120-20N; Manufacturer_Part_Number ADM3222ARUZ; Mouser Part Number 584-ADM3222ARUZ
Y1: OSC25M-3.3I/S5-25T; OSC25M
Z7, Z8, Z9: SMAJ10CA; DIONM5226X256N; Manufacturer_Part_Number SMAJ10CA
Z10, Z11, Z12, Z13: 0603ESDA2-TR2; DIONC1608X70N; Manufacturer_Part_Number 0603ESDA2-TR2; Mouser Part Number 504-0603ESDA2-TR2
Z14: P6SMB6.8CA; DIONM5436X261N; Manufacturer_Part_Number P6SMB6.8CA; Mouser Part Number 576-P6SMB6.8CA

Connections:
+3.3V: C113.1, C117.1, C118.1, C134.1, C135.1, C138.2, C139.1, C140.1, J60.L2, J60.L4, L21.1, LED35.1, R31.1, R139.1, R144.1, R145.1, R146.1, R147.1, R148.1, U32.14 (VCC), U33.14 (VCC), U34.28 (VDD), U35.8 (VCC), U36.19 (VCC), Y1.4 (VDD)
+5V_EXT: D25.2 (A)
ACTLED: R158.2, U34.27 (ACTLED)
AVDD: C1.1, C4.1, C5.1, C7.1, C9.1, C11.1, C133.1, L21.2, R153.2, R154.2, R157.1, U34.4 (AVDD), U34.8 (AVDD), U34.11 (AVDD), U34.15 (AVDD), U34.17 (AVDD), U34.21 (AVDD)
ENABLE_RS485: J12.2, U33.13 (A2), U35.3 (DE)
ESD_DUMP: C132.2
GND: C1.2, C4.2, C5.2, C7.2, C9.2, C11.2, C112.2, C113.2, C114.2, C115.2, C116.1, C118.2, C121.2, C122.2, C123.2, C124.2, C125.2, C126.2, C127.2, C128.2, C131.2, C133.2, C134.2, C135.2, C138.1, C139.2, C140.2, C142.1, J12.4, L18.2, LED34.1, LED36.1, LED37.1, LED38.1, R150.1, R151.2, R152.1, U32.7 (GND), U33.7 (GND), U34.3 (AGND), U34.9 (AGND), U34.14 (AGND), U34.16 (AGND), U34.19 (AGND), U34.29 (GND), U34.48 (AGND), U35.2 (~RE), U35.5 (GND), U36.1 (~EN), U36.18 (GND), Y1.2 (GND), Z7.2, Z8.2, Z9.2, Z10.1, Z11.1, Z12.1, Z13.1
LINKLED: R159.2, U34.25 (LINKLED)
unnamed: C114.1, U34.22 (1V2O)
unnamed: C115.1, U34.20 (TOCAP)
unnamed: C116.2, U36.7 (V-)
unnamed: C117.2, U36.3 (V+)
unnamed: C119.1, U36.5 (C2+)
unnamed: C119.2, U36.6 (C2-)
unnamed: C120.1, U36.2 (C1+)
unnamed: C120.2, U36.4 (C1-)
unnamed: C121.1, J58.1, U35.6 (A)
unnamed: C122.1, J59.5, U36.17 (T1OUT), Z7.1
unnamed: C123.1, J58.2, U35.7 (B)
unnamed: C124.1, J59.3, U36.16 (R1IN), Z8.1
unnamed: C125.1, J59.4, U36.8 (T2OUT), Z9.1
unnamed: C126.1, D25.1 (K), L17.2
unnamed: C127.1, J60.R6, R155.2, R156.2
unnamed: C128.1, J59.2, L17.1
unnamed: C129.1, J60.R7, Z10.2
unnamed: C129.2, L15.1, R156.1
unnamed: C130.1, J60.R8, Z11.2
unnamed: C130.2, L16.1, R155.1
unnamed: C131.1, J60.R3, R157.2
unnamed: C132.1, Z14.1
unnamed: C142.2, R31.2, U36.20 (~SD)
unnamed: J58.3, R152.2
unnamed: J59.1, J59.6, L18.1
unnamed: J60.L1, R159.1
unnamed: J60.L3, R158.1
unnamed: J60.R1, L13.1, R154.1, Z13.2
unnamed: J60.R2, L14.1, R153.1, Z12.2
unnamed: J60.SH, Z14.2
unnamed: LED34.2, R140.2
unnamed: LED35.2, R141.2
unnamed: LED36.2, R142.2
unnamed: LED37.2, R143.2
unnamed: LED38.2, R149.2
unnamed: R140.1, U32.8 (~O5)
unnamed: R142.1, U32.6 (~O2)
unnamed: R143.1, U32.4 (~O1)
unnamed: R146.2, U34.45 (PMODE0)
unnamed: R147.2, U34.44 (PMODE1)
unnamed: R148.2, U34.43 (PMODE2)
unnamed: R149.1, U32.2 (~O0)
unnamed: R150.2, U34.23 (RSVD)
unnamed: R151.1, U34.10 (EXRES1)
unnamed: U33.12 (B2), U35.1 (RO)
unnamed: U34.30 (XI/CLKIN), Y1.3 (OUT)
RXN: L16.2, U34.5 (RXN)
RXP: L15.2, U34.6 (RXP)
SPI0_CLK: U34.33 (SCLK)
SPI0_MISO: U34.34 (MISO)
SPI0_MOSI: U34.35 (MOSI)
TXN: L14.2, U34.1 (TXN)
TXP: L13.2, U34.2 (TXP)
UART0_RTS: U32.1 (A0), U36.13 (T1IN)
UART0_RX: U32.5 (A2), U36.15 (R1OUT)
UART0_TX: U32.3 (A1), U36.12 (T2IN)
UART1_RX: J12.1, R141.1, U33.11 (O2)
UART1_TX: J12.3, U32.9 (A5), U35.4 (DI)
~WIZNET_CS: R144.2, U34.32 (~SCS)
~WIZNET_INT: R145.2, U34.36 (~INT)
~WIZNET_RESET: C112.1, R139.2, U34.37 (~RST)

Notes on the sheet:
RS-485
RS-232
DEPOP
ESD Supression circuit * Z is added to the top side of the PCB between the mounting tab holes of J2 which is depoped for P1-540. * C is added to the bottom side of the PCB. Connect the GND side via an isolated trace that runs all the way to J12 pin 19. ** The ESD_DUMP trace is an isolated ground co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
