gasiepgodoy/Open-Source-PLC/Hardware/KiCad Files/Project/Control.kicad_sch

## KiCad design Hardware/KiCad Files/Project/Control.kicad_sch (2024-05-21)

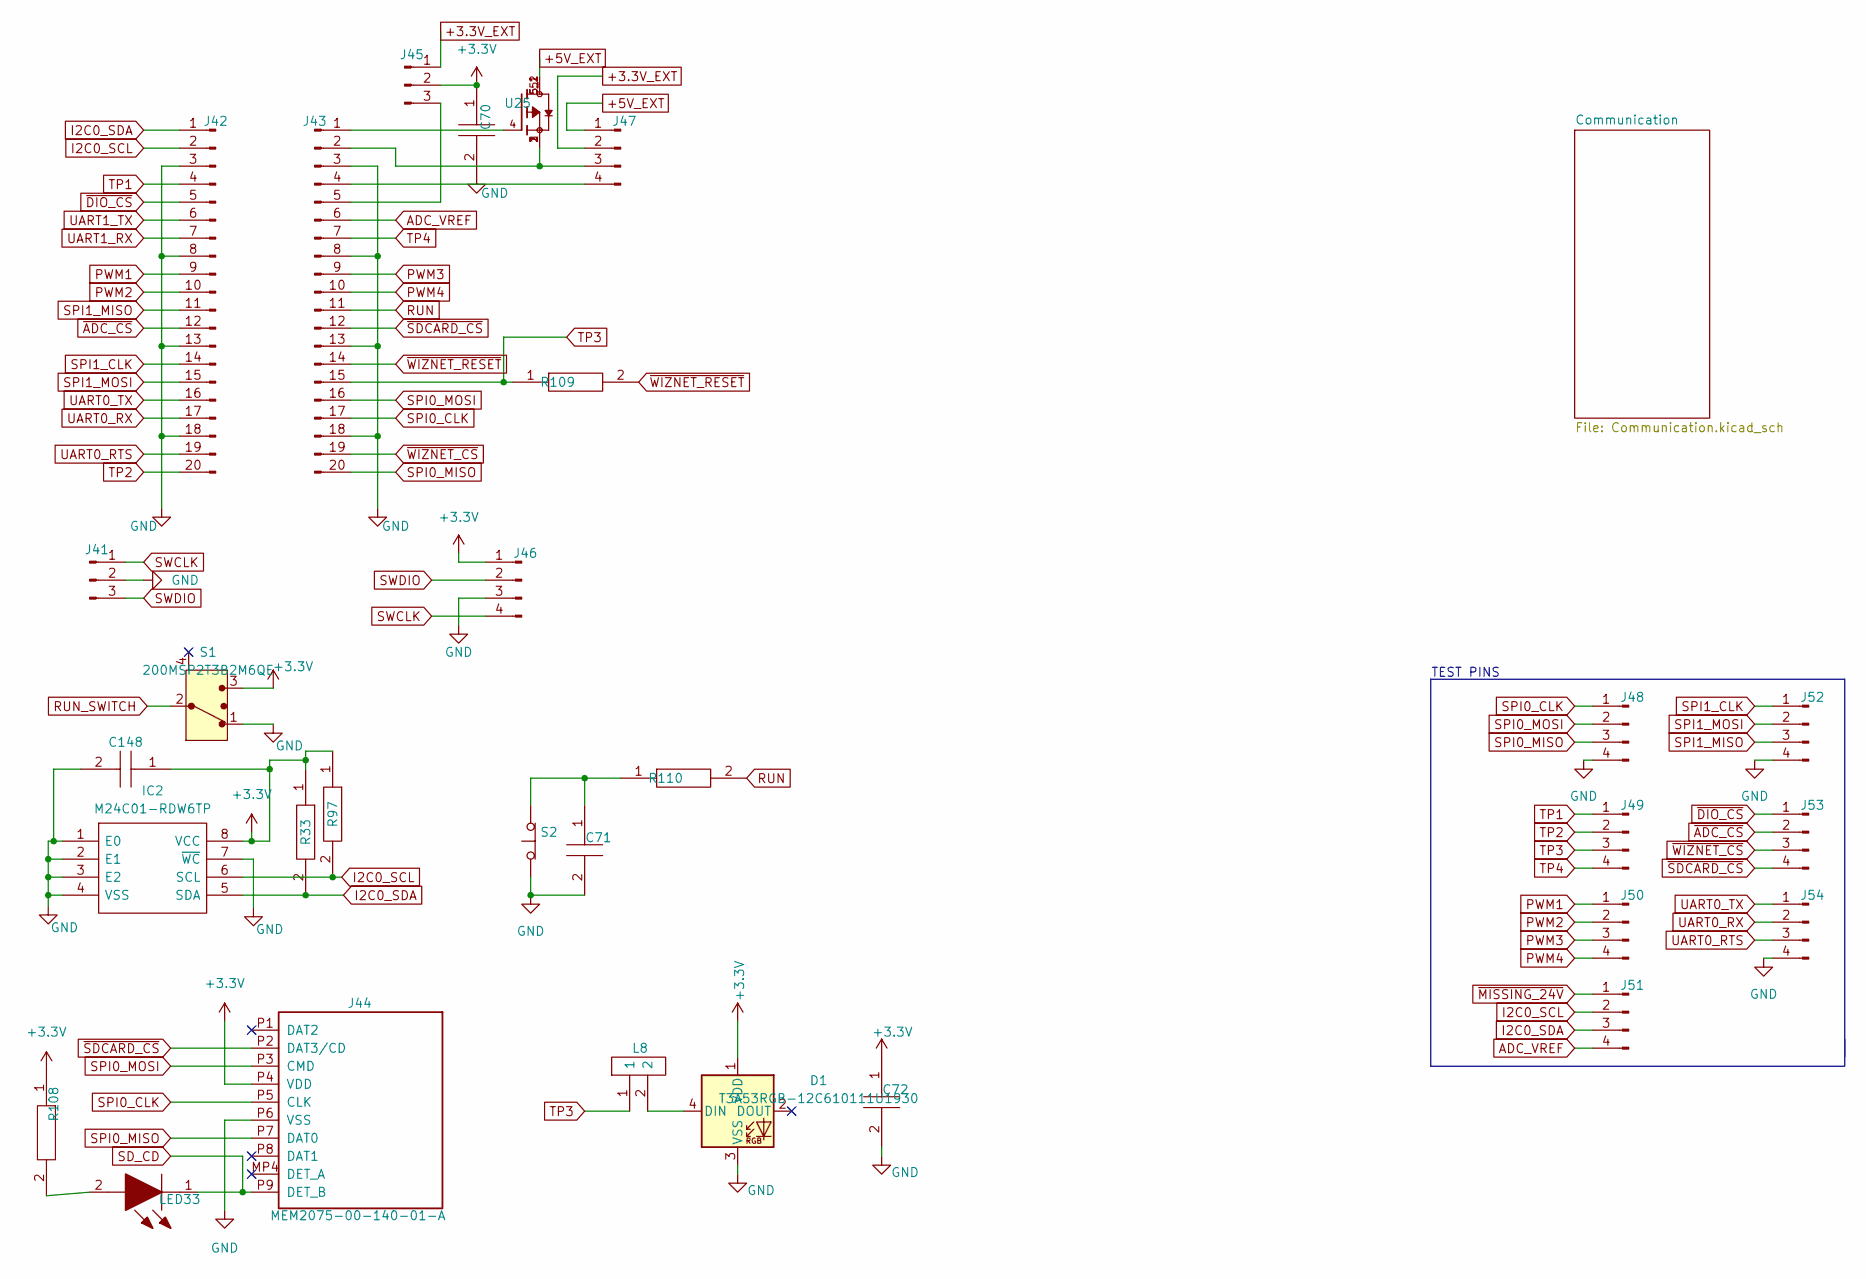
[picture p107: schematic Control.kicad_sch]

Parts:
C70, C71, C72, C148: GRM155R71H104KE14D; C_0402_1005Metric; Manufacturer_Part_Number GRM155R71H104KE14D; Mouser Part Number 81-GRM155R71H104KE4D
D1: T3A53RGB-12C610111U1930; LED_WS2812B_PLCC4_5.0x5.0mm_P3.2mm
IC2: M24C01-RDW6TP; SOP65P640X120-8N; Manufacturer_Part_Number M24C01-RDW6TP; Mouser Part Number 511-M24C01-RDW6TP
J41, J45: PH1-03-UA; PinHeader_1x03_P2.54mm_Vertical
J42, J43: PH1-20-UA; PinHeader_1x20_P2.54mm_Vertical
J44: MEM2075-00-140-01-A; MEM20750014001A
J46, J47, J48, J49, J50, J51, J52, J53, J54: PR20204VBNN; PinHeader_1x04_P2.54mm_Vertical
L8: BLM18BD221SN1D; BLM18AG102BH1D; Manufacturer_Part_Number BLM18BD221SN1D; Mouser Part Number 81-BLM18BD221SN1D
LED33: HSMG-C680; LEDC1608X60N; Manufacturer_Part_Number HSMG-C680
R33, R97: RR1220P-4751-D-M; R_0805_2012Metric; Manufacturer_Part_Number RR1220P-4751-D-M
R108: RC0402FR-07150RL; R_0402_1005Metric_Pad0.72x0.64mm_HandSolder; Manufacturer_Part_Number RC0402FR-07150RL; Mouser Part Number 603-RC0402FR-07150RL
R109: RC0603JR-070RL; R_0603_1608Metric; Manufacturer_Part_Number RC0603JR-070RL; Mouser Part Number 603-RC0603JR-070RL
R110: ERA-2AED331X; R_0402_1005Metric_Pad0.72x0.64mm_HandSolder; Manufacturer_Part_Number ERA-2AED331X
S1: 200MSP2T3B2M6QE; Toggle_Switch_200MSP2T3B2M6QE; MPN 100SP1T2B4M6QE; Digi-Key_PN EG2362-ND
S2: TL1105RF250Q
U25: STL9P3LLH6; TRANS_STL9P3LLH6; PARTREV 3

Connections:
+3.3V: C70.1, C72.1, C148.1, D1.1 (VDD), IC2.8 (VCC), J44.P4 (VDD), J45.2, J46.1, R33.1, R97.1, R108.1, S1.3
+3.3V_EXT: J45.1, J47.2
+5V_EXT: J47.1, U25.5, U25.5_1, U25.5_2
ADC_VREF: J43.6, J51.4
GND: C70.2, C71.2, C72.2, C148.2, D1.3 (VSS), IC2.1 (E0), IC2.2 (E1), IC2.3 (E2), IC2.4 (VSS), IC2.7 (~WC), J41.2, J42.3, J42.8, J42.13, J42.18, J43.3, J43.8, J43.13, J43.18, J44.P6 (VSS), J46.3, J48.4, J52.4, J54.4, S1.1, S2.1 (A)
I2C0_SCL: IC2.6 (SCL), J42.2, J51.2, R97.2
I2C0_SDA: IC2.5 (SDA), J42.1, J51.3, R33.2
unnamed: C71.1, R110.1, S2.2 (B)
unnamed: D1.4 (DIN), L8.2
unnamed: J43.1, U25.4
unnamed: J43.2, J47.3, U25.1, U25.2, U25.3
unnamed: J43.4, J47.4
unnamed: J43.5, J45.3
unnamed: LED33.2, R108.2
PWM1: J42.9, J50.1
PWM2: J42.10, J50.2
PWM3: J43.9, J50.3
PWM4: J43.10, J50.4
RUN: J43.11, R110.2
RUN_SWITCH: S1.2 (Com)
SD_CD: J44.P9 (DET_B), LED33.1
SPI0_CLK: J43.17, J44.P5 (CLK), J48.1
SPI0_MISO: J43.20, J44.P7 (DAT0), J48.3
SPI0_MOSI: J43.16, J44.P3 (CMD), J48.2
SPI1_CLK: J42.14, J52.1
SPI1_MISO: J42.11, J52.3
SPI1_MOSI: J42.15, J52.2
SWCLK: J41.1, J46.4
SWDIO: J41.3, J46.2
TP1: J42.4, J49.1
TP2: J42.20, J49.2
TP3: J43.15, J49.3, L8.1, R109.1
TP4: J43.7, J49.4
UART0_RTS: J42.19, J54.3
UART0_RX: J42.17, J54.2
UART0_TX: J42.16, J54.1
UART1_RX: J42.7
UART1_TX: J42.6
~ADC_CS: J42.12, J53.2
~DIO_CS: J42.5, J53.1
~MISSING_24V: J51.1
~SDCARD_CS: J43.12, J44.P2 (DAT3/CD), J53.4
~WIZNET_CS: J43.19, J53.3
~WIZNET_RESET: J43.14, R109.2

Notes on the sheet:
TEST PINS
