gasiepgodoy/Open-Source-PLC/Hardware/KiCad Files/Project/Digital Inputs.kicad_sch

## KiCad design Hardware/KiCad Files/Project/Digital Inputs.kicad_sch (2024-05-21)

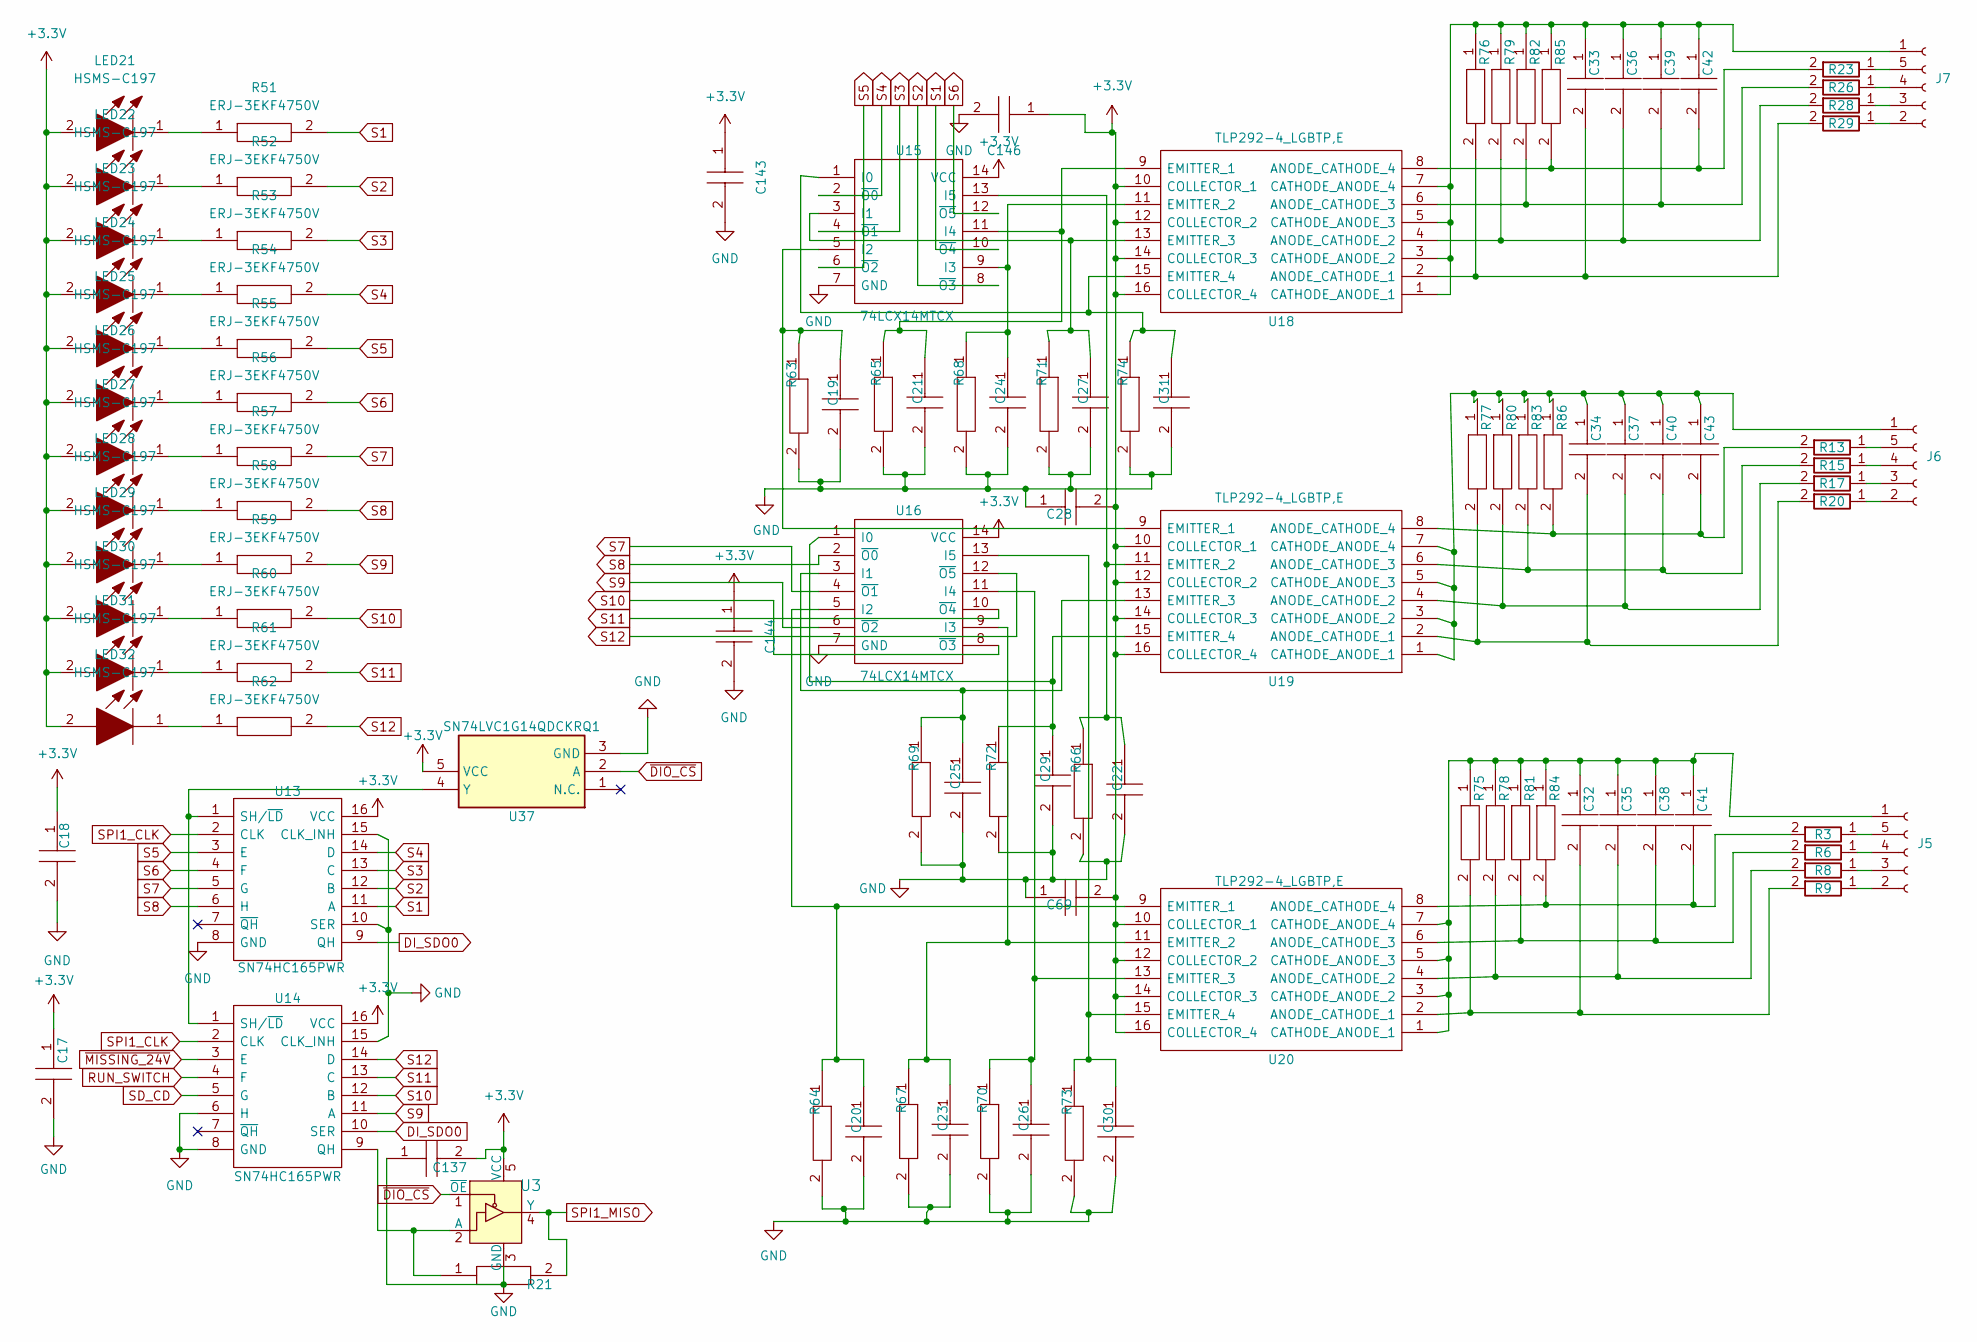
[picture p108: schematic Digital Inputs.kicad_sch]

Parts:
C17, C18, C19, C20, C21, C22, C23, C24, C25, C26, C27, C28, C29, C30, C31, C69, C137, C143, C144, C146: GRM155R71H104KE14D; C_0402_1005Metric; Manufacturer_Part_Number GRM155R71H104KE14D; Mouser Part Number 81-GRM155R71H104KE4D
C32, C33, C34, C35, C36, C37, C38, C39, C40, C41, C42, C43: GCM21BR72A104KA37L; C_0805_2012Metric; Manufacturer_Part_Number GCM21BR72A104KA37L; Mouser Part Number 81-GCM21BR72A104KA7L
J5, J6, J7: 284512-5; SHDRRA5W82P0X350_1X5_1980X920X745P
LED21, LED22, LED23, LED24, LED25, LED26, LED27, LED28, LED29, LED30, LED31, LED32: HSMS-C197; LEDC1608X60N; Manufacturer_Part_Number HSMS-C197
R3, R6, R8, R9, R13, R15, R17, R20, R23, R26, R28, R29: CRM2512-JW-302ELF; WF25P302JTL
R21: RC0603JR-070RL; R_0603_1608Metric; Manufacturer_Part_Number RC0603JR-070RL; Mouser Part Number 603-RC0603JR-070RL
R51, R52, R53, R54, R55, R56, R57, R58, R59, R60, R61, R62: ERJ-3EKF4750V; R_0603_1608Metric; Manufacturer_Part_Number ERJ-3EKF4750V; Mouser Part Number 667-ERJ-3EKF4750V
R63, R64, R65, R66, R67, R68, R69, R70, R71, R72, R73, R74: ERJ-3EKF1001V; R_0603_1608Metric; Manufacturer_Part_Number ERJ-3EKF1001V; Mouser Part Number 667-ERJ-3EKF1001V
R75, R76, R77, R78, R79, R80, R81, R82, R83, R84, R85, R86: RC0805JR-071K2L; R_0805_2012Metric; Manufacturer_Part_Number RC0805JR-071K2L; Mouser Part Number 603-RC0805JR-071K2L
U3: SN74LVC1G125DBVR; SOT-753; MPN SN74LVC1G125DBVR; Digi-Key_PN 296-11603-1-ND
U13, U14: SN74HC165PWR; SOP65P640X120-16N; Manufacturer_Part_Number SN74HC165PW; Mouser Part Number 595-SN74HC165PW
U15, U16: 74LCX14MTCX; SOP65P640X120-14N; Manufacturer_Part_Number 74LCX14MTC; Mouser Part Number 512-74LCX14MTC
U18, U19, U20: TLP292-4_LGBTP,E; SOIC127P700X230-16N; Manufacturer_Part_Number TLP292-4(LGBTP,E; Mouser Part Number 757-TLP292-4LGBTPE
U37: SN74LVC1G14QDCKRQ1; SOT65P210X110-5N; Manufacturer_Part_Number SN74LVC1G14QDCKRQ1; Mouser Part Number 595-74LVC1G14QDCKRQ1

Connections:
+3.3V: C17.1, C18.1, C28.2, C69.2, C137.2, C143.1, C144.1, C146.1, LED21.2, LED22.2, LED23.2, LED24.2, LED25.2, LED26.2, LED27.2, LED28.2, LED29.2, LED30.2, LED31.2, LED32.2, U3.5 (VCC), U13.16 (VCC), U14.16 (VCC), U15.14 (VCC), U16.14 (VCC), U18.10 (COLLECTOR_1), U18.12 (COLLECTOR_2), U18.14 (COLLECTOR_3), U18.16 (COLLECTOR_4), U19.10 (COLLECTOR_1), U19.12 (COLLECTOR_2), U19.14 (COLLECTOR_3), U19.16 (COLLECTOR_4), U20.10 (COLLECTOR_1), U20.12 (COLLECTOR_2), U20.14 (COLLECTOR_3), U20.16 (COLLECTOR_4), U37.5 (VCC)
DI_SDO0: U13.9 (QH), U14.10 (SER)
GND: C17.2, C18.2, C19.2, C20.2, C21.2, C22.2, C23.2, C24.2, C25.2, C26.2, C27.2, C28.1, C29.2, C30.2, C31.2, C69.1, C137.1, C143.2, C144.2, C146.2, R63.2, R64.2, R65.2, R66.2, R67.2, R68.2, R69.2, R70.2, R71.2, R72.2, R73.2, R74.2, U3.3 (GND), U13.8 (GND), U13.10 (SER), U13.15 (CLK_INH), U14.6 (H), U14.8 (GND), U14.15 (CLK_INH), U15.7 (GND), U16.7 (GND), U37.3 (GND)
unnamed: C19.1, R63.1, U15.5 (I2), U19.9 (EMITTER_1)
unnamed: C20.1, R64.1, U16.5 (I2), U20.9 (EMITTER_1)
unnamed: C21.1, R65.1, U15.11 (I4), U18.9 (EMITTER_1)
unnamed: C22.1, R66.1, U15.13 (I5), U19.11 (EMITTER_2)
unnamed: C23.1, R67.1, U16.9 (I3), U20.11 (EMITTER_2)
unnamed: C24.1, R68.1, U15.9 (I3), U18.11 (EMITTER_2)
unnamed: C25.1, R69.1, U16.3 (I1), U19.13 (EMITTER_3)
unnamed: C26.1, R70.1, U16.11 (I4), U20.13 (EMITTER_3)
unnamed: C27.1, R71.1, U15.3 (I1), U18.13 (EMITTER_3)
unnamed: C29.1, R72.1, U16.1 (I0), U19.15 (EMITTER_4)
unnamed: C30.1, R73.1, U16.13 (I5), U20.15 (EMITTER_4)
unnamed: C31.1, R74.1, U15.1 (I0), U18.15 (EMITTER_4)
unnamed: C32.1, C35.1, C38.1, C41.1, J5.1, R75.1, R78.1, R81.1, R84.1, U20.1 (CATHODE_ANODE_1), U20.3 (CATHODE_ANODE_2), U20.5 (CATHODE_ANODE_3), U20.7 (CATHODE_ANODE_4)
unnamed: C32.2, R9.2, R75.2, U20.2 (ANODE_CATHODE_1)
unnamed: C33.1, C36.1, C39.1, C42.1, J7.1, R76.1, R79.1, R82.1, R85.1, U18.1 (CATHODE_ANODE_1), U18.3 (CATHODE_ANODE_2), U18.5 (CATHODE_ANODE_3), U18.7 (CATHODE_ANODE_4)
unnamed: C33.2, R29.2, R76.2, U18.2 (ANODE_CATHODE_1)
unnamed: C34.1, C37.1, C40.1, C43.1, J6.1, R77.1, R80.1, R83.1, R86.1, U19.1 (CATHODE_ANODE_1), U19.3 (CATHODE_ANODE_2), U19.5 (CATHODE_ANODE_3), U19.7 (CATHODE_ANODE_4)
unnamed: C34.2, R20.2, R77.2, U19.2 (ANODE_CATHODE_1)
unnamed: C35.2, R8.2, R78.2, U20.4 (ANODE_CATHODE_2)
unnamed: C36.2, R28.2, R79.2, U18.4 (ANODE_CATHODE_2)
unnamed: C37.2, R17.2, R80.2, U19.4 (ANODE_CATHODE_2)
unnamed: C38.2, R6.2, R81.2, U20.6 (ANODE_CATHODE_3)
unnamed: C39.2, R26.2, R82.2, U18.6 (ANODE_CATHODE_3)
unnamed: C40.2, R15.2, R83.2, U19.6 (ANODE_CATHODE_3)
unnamed: C41.2, R3.2, R84.2, U20.8 (ANODE_CATHODE_4)
unnamed: C42.2, R23.2, R85.2, U18.8 (ANODE_CATHODE_4)
unnamed: C43.2, R13.2, R86.2, U19.8 (ANODE_CATHODE_4)
unnamed: J5.2 (Pin_5), R9.1
unnamed: J5.3 (Pin_4), R8.1
unnamed: J5.4 (Pin_3), R6.1
unnamed: J5.5 (Pin_2), R3.1
unnamed: J6.2 (Pin_5), R20.1
unnamed: J6.3 (Pin_4), R17.1
unnamed: J6.4 (Pin_3), R15.1
unnamed: J6.5 (Pin_2), R13.1
unnamed: J7.2 (Pin_5), R29.1
unnamed: J7.3 (Pin_4), R28.1
unnamed: J7.4 (Pin_3), R26.1
unnamed: J7.5 (Pin_2), R23.1
unnamed: LED21.1, R51.1
unnamed: LED22.1, R52.1
unnamed: LED23.1, R53.1
unnamed: LED24.1, R54.1
unnamed: LED25.1, R55.1
unnamed: LED26.1, R56.1
unnamed: LED27.1, R57.1
unnamed: LED28.1, R58.1
unnamed: LED29.1, R59.1
unnamed: LED30.1, R60.1
unnamed: LED31.1, R61.1
unnamed: LED32.1, R62.1
unnamed: R21.1, U3.2 (A), U14.9 (QH)
unnamed: U13.1 (SH/~LD), U14.1 (SH/~LD), U37.4 (Y)
RUN_SWITCH: U14.4 (F)
S1: R51.2, U13.11 (A), U15.10 (~O4)
S2: R52.2, U13.12 (B), U15.8 (~O3)
S3: R53.2, U13.13 (C), U15.4 (~O1)
S4: R54.2, U13.14 (D), U15.2 (~O0)
S5: R55.2, U13.3 (E), U15.6 (~O2)
S6: R56.2, U13.4 (F), U15.12 (~O5)
S7: R57.2, U13.5 (G), U16.4 (~O1)
S8: R58.2, U13.6 (H), U16.2 (~O0)
S9: R59.2, U14.11 (A), U16.6 (~O2)
S10: R60.2, U14.12 (B), U16.8 (~O3)
S11: R61.2, U14.13 (C), U16.10 (~O4)
S12: R62.2, U14.14 (D), U16.12 (~O5)
SD_CD: U14.5 (G)
SPI1_CLK: U13.2 (CLK), U14.2 (CLK)
SPI1_MISO: R21.2, U3.4 (Y)
~DIO_CS: U3.1 (~OE), U37.2 (A)
~MISSING_24V: U14.3 (E)
