gasiepgodoy/Open-Source-PLC/Hardware/KiCad Files/Project/Digital Outputs.kicad_sch

## KiCad design Hardware/KiCad Files/Project/Digital Outputs.kicad_sch (2024-05-21)

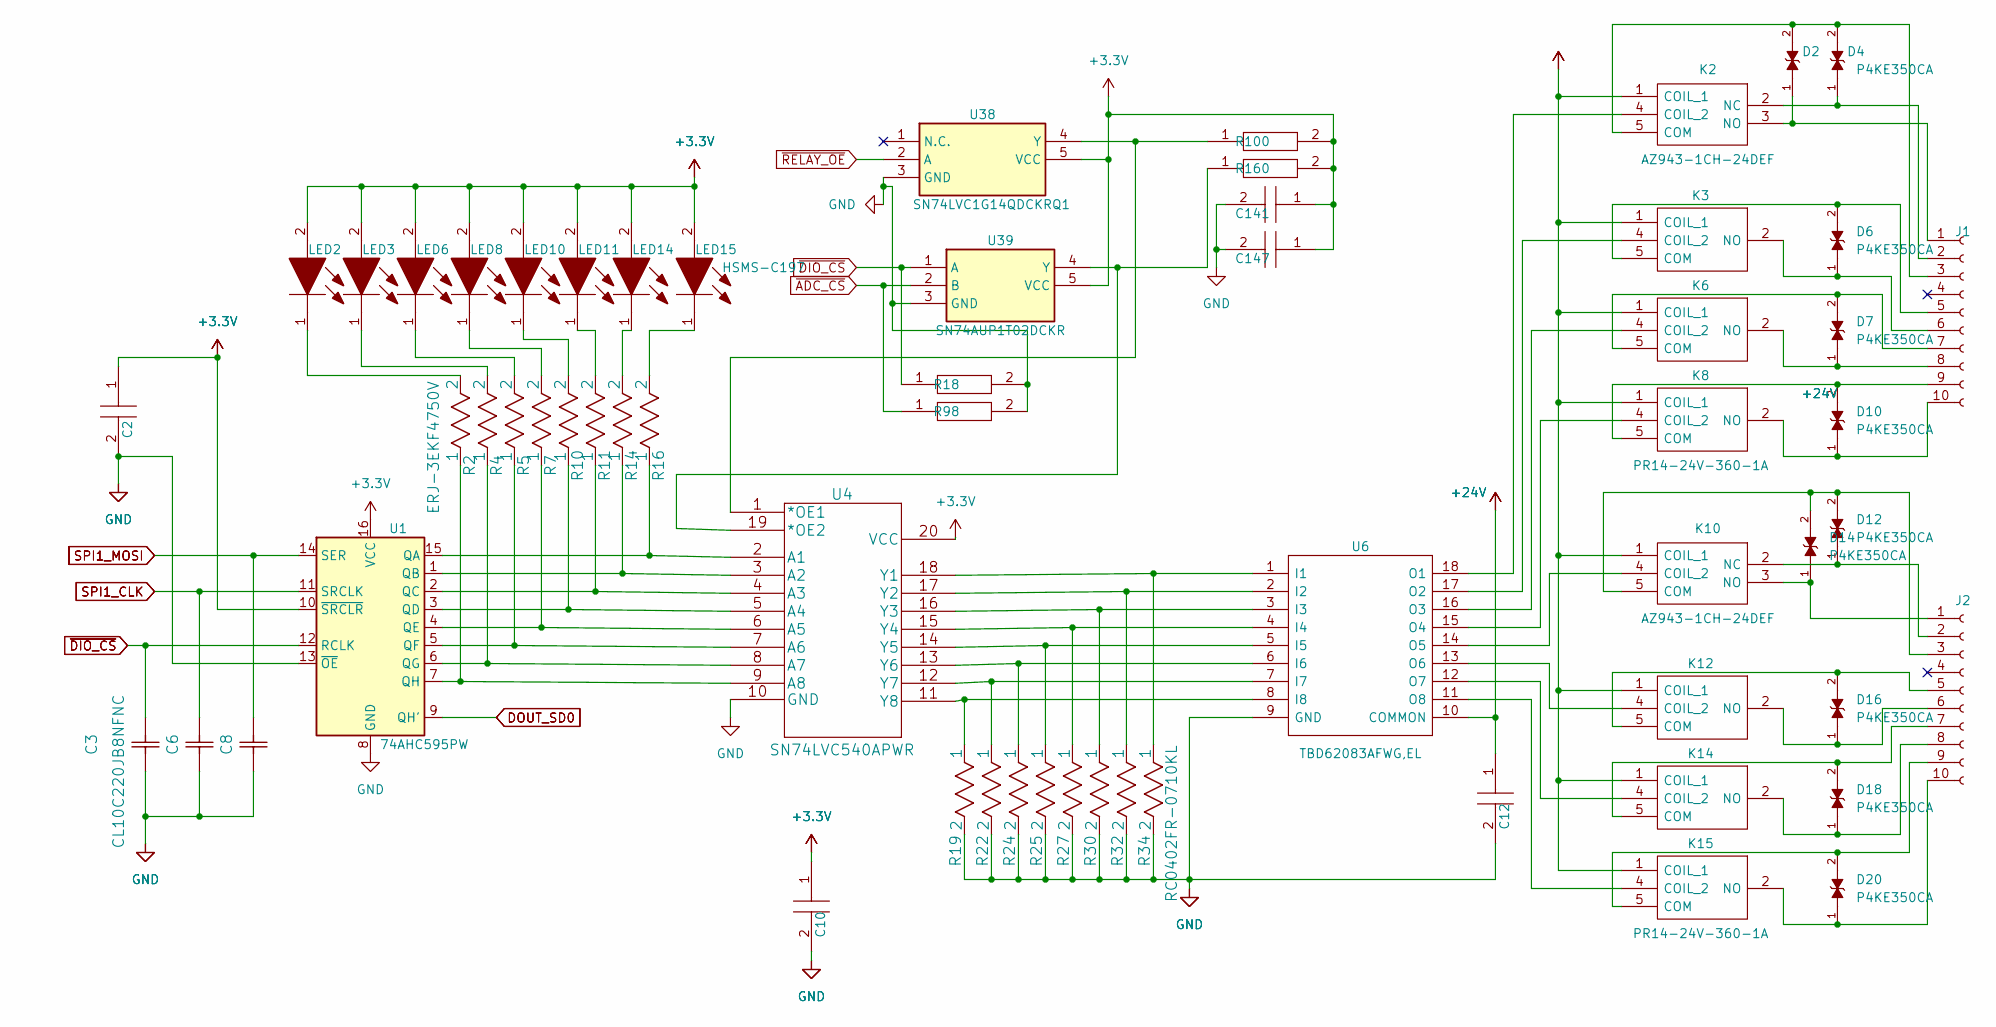
[picture p109: schematic Digital Outputs.kicad_sch]

Parts:
C2, C10, C12, C141, C147: GRM155R71H104KE14D; C_0402_1005Metric; Manufacturer_Part_Number GRM155R71H104KE14D; Mouser Part Number 81-GRM155R71H104KE4D
C3, C6, C8: CL10C220JB8NFNC; C_0603_1608Metric
D2, D4, D6, D7, D10, D12, D14, D16, D18, D20: P4KE350CA; DIOAD1036W78L470D235; PARTREV N2104
J1, J2: TBP04R2-500-10BE; PhoenixContact_MCV_1,5_10-G-5.08_1x10_P5.08mm_Vertical
K2, K10: AZ943-1CH-24DEF; AZ9431CH24DE; Manufacturer_Part_Number 833H-1C-F-S-24VDC; Mouser Part Number 893-833H1CFS24VDC
K3, K6, K8, K12, K14, K15: PR14-24V-360-1A; 833H1CFS24VDC; Manufacturer_Part_Number 833H-1C-F-S-24VDC; Mouser Part Number 893-833H1CFS24VDC
LED2, LED3, LED6, LED8, LED10, LED11, LED14, LED15: HSMS-C197; LEDC1608X60N; Manufacturer_Part_Number HSMS-C197
R2, R4, R5, R7, R10, R11, R14, R16: ERJ-3EKF4750V; R_0603_1608Metric; Manufacturer_Part_Number ERJ-3EKF4750V
R18, R98: RC0402FR-0710KL; R_0402_1005Metric_Pad0.72x0.64mm_HandSolder; Manufacturer_Part_Number RC0402FR-0710KL; Mouser Part Number 603-RC0402FR-0710KL
R19, R22, R24, R25, R27, R30, R32, R34: RC0402FR-0710KL; R_0402_1005Metric_Pad0.72x0.64mm_HandSolder
R100, R160: RC0603JR-070RL; R_0603_1608Metric; Manufacturer_Part_Number RC0603JR-070RL; Mouser Part Number 603-RC0603JR-070RL
U1: 74AHC595PW; SN74AHC595PW
U4: SN74LVC540APWR; SOP65P640X120-20N
U6: TBD62083AFWG,EL; SOIC127P1030X265-18N; Manufacturer_Part_Number ULN2803AFWG(C,ELHA; Mouser Part Number 757-ULN2803AFWGCELHA
U38: SN74LVC1G14QDCKRQ1; SOT65P210X110-5N; Manufacturer_Part_Number SN74LVC1G14QDCKRQ1; Mouser Part Number 595-74LVC1G14QDCKRQ1
U39: SN74AUP1T02DCKR; SOT65P210X110-5N; Manufacturer_Part_Number SN74AUP1T02DCKR; Mouser Part Number 595-SN74AUP1T02DCKR

Connections:
+3.3V: C2.1, C10.1, C141.1, C147.1, LED2.2, LED3.2, LED6.2, LED8.2, LED10.2, LED11.2, LED14.2, LED15.2, R100.2, R160.2, U1.10 (~SRCLR), U1.16 (VCC), U4.20 (VCC), U38.5 (VCC), U39.5 (VCC)
+24V: C12.1, K2.1 (COIL_1), K3.1 (COIL_1), K6.1 (COIL_1), K8.1 (COIL_1), K10.1 (COIL_1), K12.1 (COIL_1), K14.1 (COIL_1), K15.1 (COIL_1), U6.10 (COMMON)
DOUT_SD0: U1.9 (QH')
GND: C2.2, C3.1, C6.1, C8.1, C10.2, C12.2, C141.2, C147.2, R18.2, R19.2, R22.2, R24.2, R25.2, R27.2, R30.2, R32.2, R34.2, R98.2, U1.8 (GND), U1.13 (~OE), U4.10 (GND), U6.9 (GND), U38.3 (GND), U39.3 (GND)
unnamed: D2.1, J1.1, K2.3 (NO)
unnamed: D2.2, D4.2, J1.3, K2.5 (COM)
unnamed: D4.1, J1.2, K2.2 (NC)
unnamed: D6.1, J1.6, K3.2 (NO)
unnamed: D6.2, J1.5, K3.5 (COM)
unnamed: D7.1, J1.8, K6.2 (NO)
unnamed: D7.2, J1.7, K6.5 (COM)
unnamed: D10.1, J1.10, K8.2 (NO)
unnamed: D10.2, J1.9, K8.5 (COM)
unnamed: D12.1, J2.2, K10.2 (NC)
unnamed: D12.2, D14.2, J2.3, K10.5 (COM)
unnamed: D14.1, J2.1, K10.3 (NO)
unnamed: D16.1, J2.6, K12.2 (NO)
unnamed: D16.2, J2.5, K12.5 (COM)
unnamed: D18.1, J2.8, K14.2 (NO)
unnamed: D18.2, J2.7, K14.5 (COM)
unnamed: D20.1, J2.10, K15.2 (NO)
unnamed: D20.2, J2.9, K15.5 (COM)
unnamed: K2.4 (COIL_2), U6.18 (O1)
unnamed: K3.4 (COIL_2), U6.17 (O2)
unnamed: K6.4 (COIL_2), U6.16 (O3)
unnamed: K8.4 (COIL_2), U6.15 (O4)
unnamed: K10.4 (COIL_2), U6.14 (O5)
unnamed: K12.4 (COIL_2), U6.13 (O6)
unnamed: K14.4 (COIL_2), U6.12 (O7)
unnamed: K15.4 (COIL_2), U6.11 (O8)
unnamed: LED2.1, R2.2
unnamed: LED3.1, R4.2
unnamed: LED6.1, R5.2
unnamed: LED8.1, R7.2
unnamed: LED10.1, R10.2
unnamed: LED11.1, R11.2
unnamed: LED14.1, R14.2
unnamed: LED15.1, R16.2
unnamed: R2.1, U1.7 (QH), U4.9 (A8)
unnamed: R4.1, U1.6 (QG), U4.8 (A7)
unnamed: R5.1, U1.5 (QF), U4.7 (A6)
unnamed: R7.1, U1.4 (QE), U4.6 (A5)
unnamed: R10.1, U1.3 (QD), U4.5 (A4)
unnamed: R11.1, U1.2 (QC), U4.4 (A3)
unnamed: R14.1, U1.1 (QB), U4.3 (A2)
unnamed: R16.1, U1.15 (QA), U4.2 (A1)
unnamed: R19.1, U4.11 (Y8), U6.8 (I8)
unnamed: R22.1, U4.12 (Y7), U6.7 (I7)
unnamed: R24.1, U4.13 (Y6), U6.6 (I6)
unnamed: R25.1, U4.14 (Y5), U6.5 (I5)
unnamed: R27.1, U4.15 (Y4), U6.4 (I4)
unnamed: R30.1, U4.16 (Y3), U6.3 (I3)
unnamed: R32.1, U4.17 (Y2), U6.2 (I2)
unnamed: R34.1, U4.18 (Y1), U6.1 (I1)
unnamed: R100.1, U4.1 (*OE1), U38.4 (Y)
unnamed: R160.1, U4.19 (*OE2), U39.4 (Y)
SPI1_CLK: C6.2, U1.11 (SRCLK)
SPI1_MOSI: C8.2, U1.14 (SER)
~ADC_CS: R98.1, U39.2 (B)
~DIO_CS: C3.2, R18.1, U1.12 (RCLK), U39.1 (A)
~RELAY_OE: U38.2 (A)
