gasiepgodoy/Open-Source-PLC/Hardware/KiCad Files/Project/Encoder.kicad_sch

## KiCad design Hardware/KiCad Files/Project/Encoder.kicad_sch (2024-05-21)

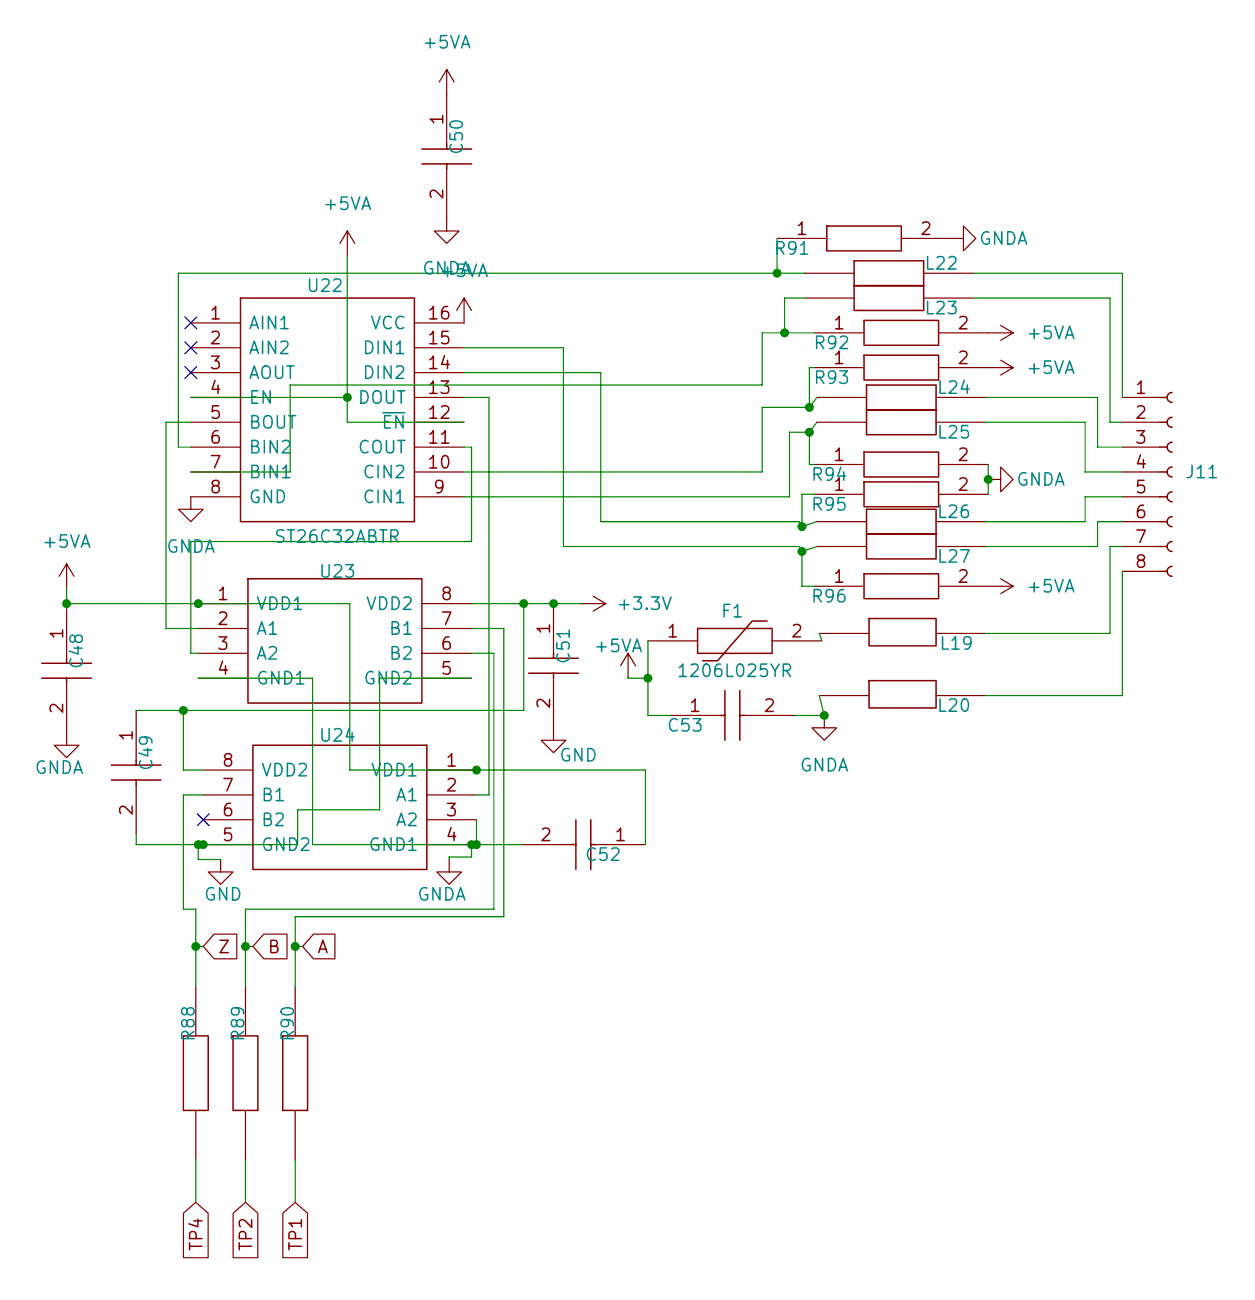
[picture p110: schematic Encoder.kicad_sch]

Parts:
C48, C49, C50, C51, C52, C53: GRM155R71H104KE14D; C_0402_1005Metric; Manufacturer_Part_Number GRM155R71H104KE14D; Mouser Part Number 81-GRM155R71H104KE4D
F1: 1206L025YR; FUSC3216X100N; Manufacturer_Part_Number 1206L025YR; Mouser Part Number 576-1206L025YR
J11: 5441391; SHDRRA8W83P0X350_1X8_2940X920X755P
L19, L20: MPZ2012S331AT000; INDC2012X105N; Manufacturer_Part_Number MPZ2012S331AT; Mouser Part Number N/A
L22, L23, L24, L25, L26, L27: BLM15HG102SN1D; BEADC1005X55N; Manufacturer_Part_Number BLM15HG102SN1D; Mouser Part Number 81-BLM15HG102SN1D
R88, R89, R90: RC0603JR-070RL; R_0603_1608Metric; Manufacturer_Part_Number RC0603JR-070RL; Mouser Part Number 603-RC0603JR-070RL
R91, R92, R93, R94, R95, R96: ERJ-3EKF1001V; R_0603_1608Metric; Manufacturer_Part_Number ERJ-3EKF1001V; Mouser Part Number 667-ERJ-3EKF1001V
U22: ST26C32ABTR; SOP65P640X120-16N; Manufacturer_Part_Number ST26C32ABTR; Mouser Part Number 511-ST26C32AB
U23, U24: SI8620BB-B-ISR; SOIC127P600X175-8N; Manufacturer_Part_Number SI8620BB-B-ISR; Mouser Part Number 634-SI8620BB-B-ISR

Connections:
+3.3V: C49.1, C51.1, U23.8 (VDD2), U24.8 (VDD2)
+5VA: C48.1, C50.1, C52.1, C53.1, F1.1, R92.2, R93.2, R96.2, U22.4 (EN), U22.12 (~EN), U22.16 (VCC), U23.1 (VDD1), U24.1 (VDD1)
A: R90.1, U23.7 (B1)
B: R89.1, U23.6 (B2)
GND: C49.2, C51.2, U23.5 (GND2), U24.5 (GND2)
GNDA: C48.2, C50.2, C52.2, C53.2, L20.1, R91.2, R94.2, R95.2, U22.8 (GND), U23.4 (GND1), U24.3 (A2), U24.4 (GND1)
unnamed: F1.2, L19.1
unnamed: J11.1, L22.2
unnamed: J11.2, L23.2
unnamed: J11.3, L24.2
unnamed: J11.4, L25.2
unnamed: J11.5, L26.2
unnamed: J11.6, L27.2
unnamed: J11.7, L19.2
unnamed: J11.8, L20.2
unnamed: L22.1, R91.1, U22.6 (BIN2)
unnamed: L23.1, R92.1, U22.7 (BIN1)
unnamed: L24.1, R93.1, U22.10 (CIN2)
unnamed: L25.1, R94.1, U22.9 (CIN1)
unnamed: L26.1, R95.1, U22.14 (DIN2)
unnamed: L27.1, R96.1, U22.15 (DIN1)
unnamed: U22.5 (BOUT), U23.2 (A1)
unnamed: U22.11 (COUT), U23.3 (A2)
unnamed: U22.13 (DOUT), U24.2 (A1)
TP1: R90.2
TP2: R89.2
TP4: R88.2
Z: R88.1, U24.7 (B1)
