gasiepgodoy/Open-Source-PLC/Hardware/KiCad Files/Project/PWM.kicad_sch

## KiCad design Hardware/KiCad Files/Project/PWM.kicad_sch (2024-05-21)

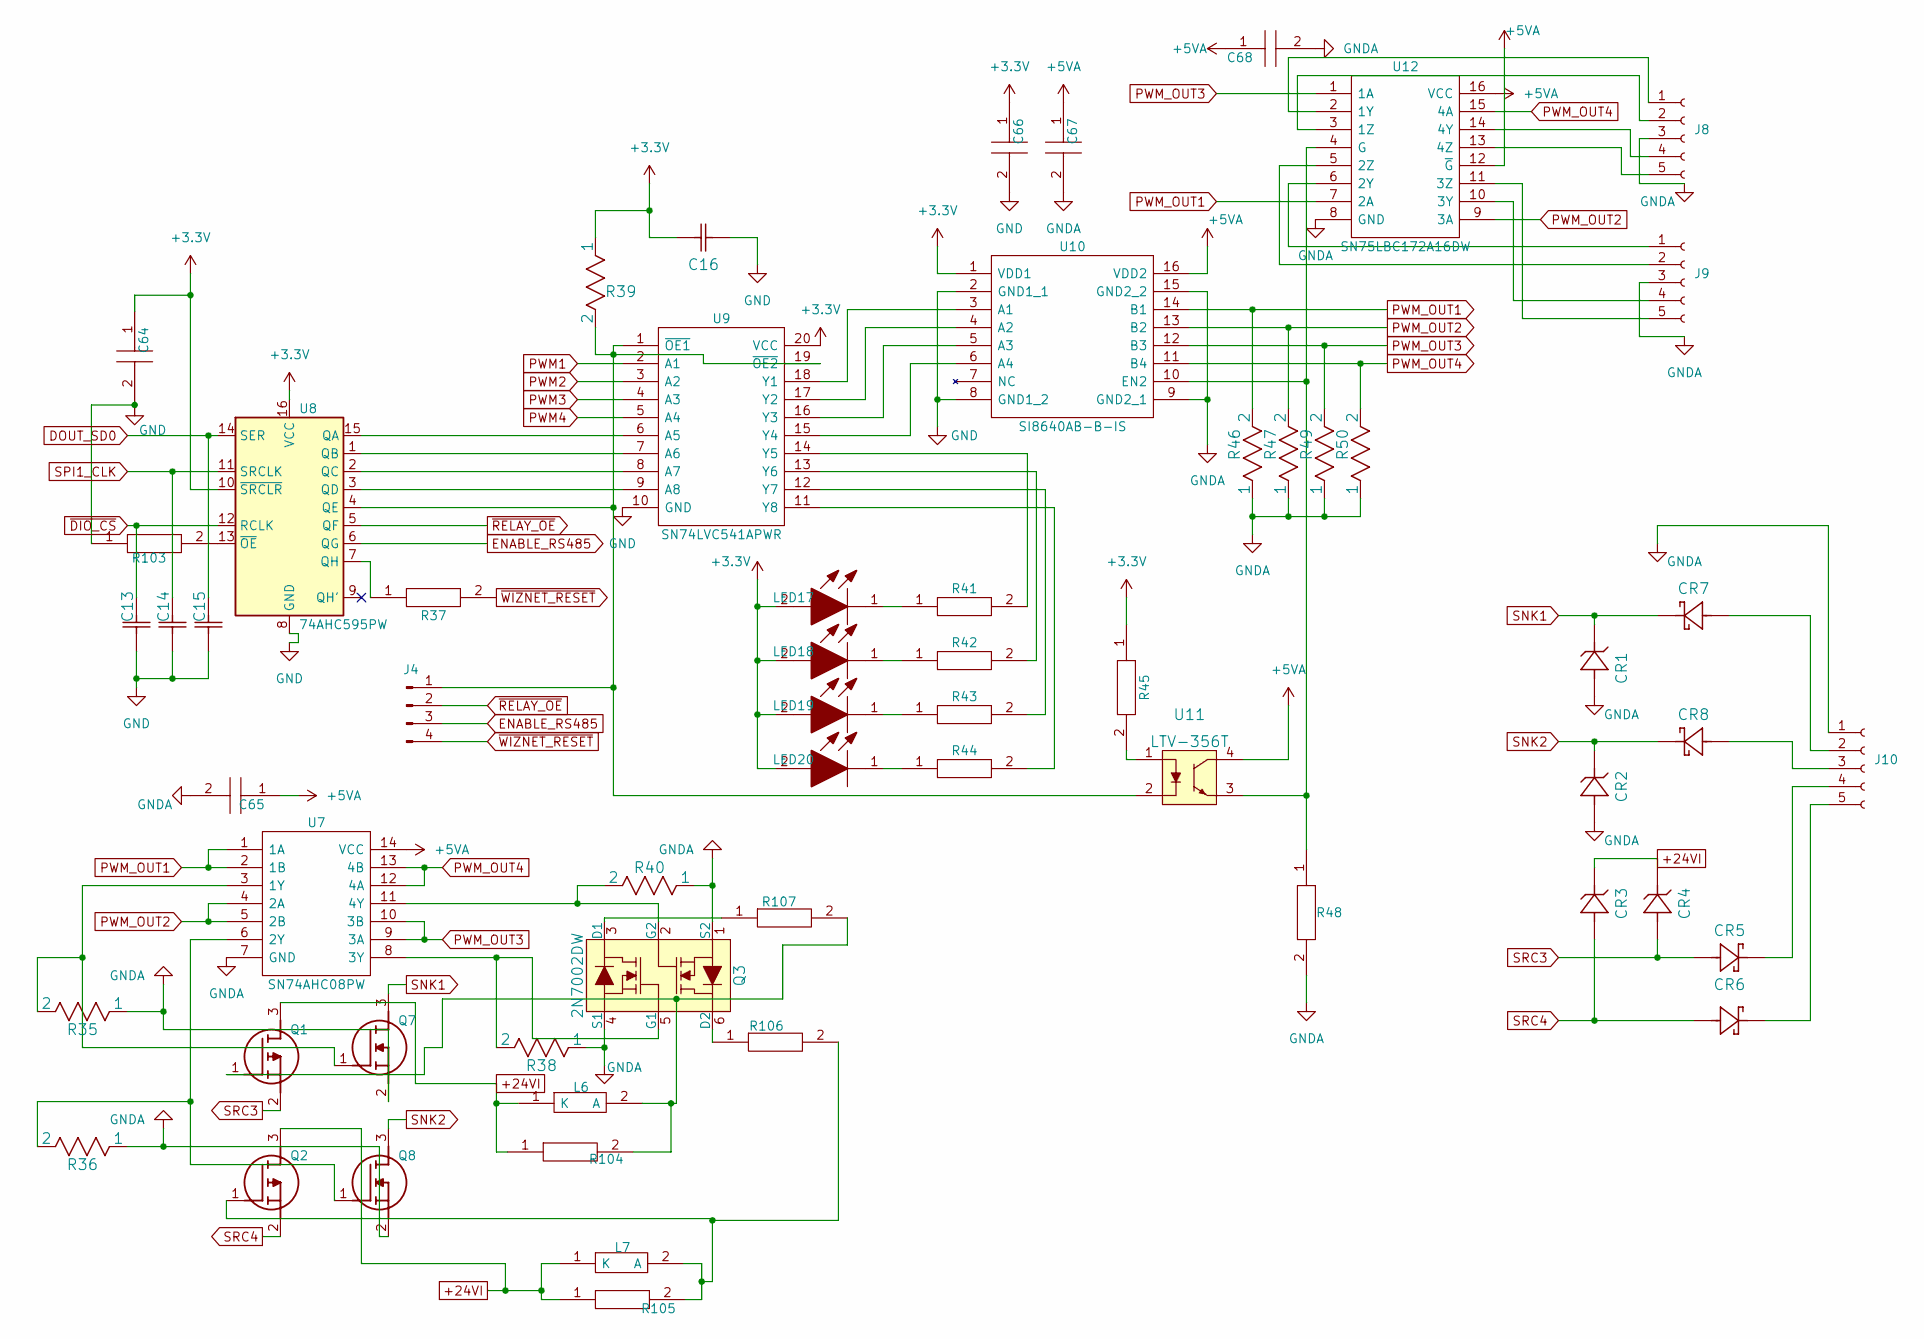
[picture p111: schematic PWM.kicad_sch]

Parts:
C13, C14, C15: CL10C220JB8NFNC; C_0603_1608Metric
C16: C1005X7R1E103K050BB; C_0402_1005Metric
C64, C65, C66, C67, C68: GRM155R71H104KE14D; C_0402_1005Metric; Manufacturer_Part_Number GRM155R71H104KE14D; Mouser Part Number 81-GRM155R71H104KE4D
CR1, CR2, CR3, CR4: SMAJ28A-TR
CR5, CR6, CR7, CR8: SM5819PL-TP
J4: PR20204VBNN; PinHeader_1x04_P2.54mm_Vertical
J8, J9, J10: 284512-5; SHDRRA5W82P0X350_1X5_1980X920X745P
L6, L7: DDZ20ASF-7; SODFL2512X75N; Manufacturer_Part_Number DDZ20ASF-7; Mouser Part Number 621-DDZ20ASF-7
LED17, LED18, LED19, LED20: HSMS-C197; LEDC1608X60N; Manufacturer_Part_Number HSMS-C197
Q1, Q2: DMP6350SQ-7; SOT96P240X110-3N; Manufacturer_Part_Number DMP6350SQ-7; Mouser Part Number 621-DMP6350SQ-7
Q3: 2N7002DW; SOT-363; MPN 2N7002DW; Digi-Key_PN 2N7002DWCT-ND
Q7, Q8: 2N7002L; SOT96P237X111-3N; Manufacturer_Part_Number 2N7002L; Mouser Part Number 512-2N7002L
R35, R36, R38, R40: RC0805JR-071K2L; R_0805_2012Metric
R37: RC0603JR-070RL; R_0603_1608Metric; Manufacturer_Part_Number RC0603JR-070RL; Mouser Part Number 603-RC0603JR-070RL
R39, R46, R47, R49, R50: RC0402FR-0710KL; R_0402_1005Metric_Pad0.72x0.64mm_HandSolder
R41, R42, R43, R44: ERJ-3GEYJ471V; R_0603_1608Metric; Manufacturer_Part_Number ERJ-3GEYJ471V; Mouser Part Number 667-ERJ-3GEYJ471V
R45: ERJ-3EKF6650V; R_0603_1608Metric; Manufacturer_Part_Number ERJ-3EKF6650V; Mouser Part Number 667-ERJ-3EKF6650V
R48, R104, R105: ERJ-6ENF5761V; R_0805_2012Metric; Manufacturer_Part_Number ERJ-6ENF5761V; Mouser Part Number 667-ERJ-6ENF5761V
R103: RC0402FR-0710KL; R_0402_1005Metric_Pad0.72x0.64mm_HandSolder; Manufacturer_Part_Number RC0402FR-0710KL; Mouser Part Number 603-RC0402FR-0710KL
R106, R107: RC0805JR-071K2L; R_0805_2012Metric; Manufacturer_Part_Number RC0805JR-071K2L; Mouser Part Number 603-RC0805JR-071K2L
U7: SN74AHC08PW; SOP65P640X120-14N; Manufacturer_Part_Number SN74AHC08PW; Mouser Part Number 595-SN74AHC08PW
U8: 74AHC595PW; SN74AHC595PW
U9: SN74LVC541APWR; SOP65P640X120-20N; Manufacturer_Part_Number SN74LVC541APWR; Mouser Part Number 595-SN74LVC541APWR
U10: SI8640AB-B-IS; SOIC127P600X175-16N; Manufacturer_Part_Number SI8640AB-B-IS; Mouser Part Number 634-SI8640AB-B-IS
U11: LTV-356T; SMD-4_4.4x3.85mm_P2.54mm; MPN LTV-356T; Digi-Key_PN 160-1337-1-ND
U12: SN75LBC172A16DW; SOIC127P1030X265-16N; Manufacturer_Part_Number SN75LBC172A16DWR; Mouser Part Number 595-SN75LBC172A16DWR

Connections:
+3.3V: C16.1, C64.1, C66.1, LED17.2, LED18.2, LED19.2, LED20.2, R39.1, R45.1, U8.10 (~SRCLR), U8.16 (VCC), U9.20 (VCC), U10.1 (VDD1)
+5VA: C65.1, C67.1, C68.1, U7.14 (VCC), U10.16 (VDD2), U11.4, U12.12 (~G), U12.16 (VCC)
+24VI: CR3.1, CR4.1, L6.1 (K), L7.1 (K), Q1.3 (D), Q2.3 (D), R104.1, R105.1
DOUT_SD0: C15.2, U8.14 (SER)
ENABLE_RS485: J4.3, U8.6 (QG)
GND: C13.1, C14.1, C15.1, C16.2, C64.2, C66.2, R103.1, U8.8 (GND), U9.10 (GND), U10.2 (GND1_1), U10.8 (GND1_2)
GNDA: C65.2, C67.2, C68.2, CR1.2, CR2.2, J8.3, J9.3, J10.1, Q3.1 (S2), Q3.4 (S1), Q7.2 (S), Q8.2 (S), R35.1, R36.1, R38.1, R40.1, R46.1, R47.1, R48.2, R49.1, R50.1, U7.7 (GND), U10.9 (GND2_1), U10.15 (GND2_2), U12.8 (GND)
unnamed: CR5.1, J10.4
unnamed: CR6.1, J10.5
unnamed: CR7.2, J10.2
unnamed: CR8.2, J10.3
unnamed: J4.1, R39.2, U8.4 (QE), U9.1 (~OE1), U9.19 (~OE2), U11.2
unnamed: J8.1, U12.2 (1Y)
unnamed: J8.2, U12.3 (1Z)
unnamed: J8.4, U12.14 (4Y)
unnamed: J8.5, U12.13 (4Z)
unnamed: J9.1, U12.6 (2Y)
unnamed: J9.2, U12.5 (2Z)
unnamed: J9.4, U12.10 (3Y)
unnamed: J9.5, U12.11 (3Z)
unnamed: L6.2 (A), Q1.1 (G), R104.2, R107.2
unnamed: L7.2 (A), Q2.1 (G), R105.2, R106.2
unnamed: LED17.1, R41.1
unnamed: LED18.1, R42.1
unnamed: LED19.1, R43.1
unnamed: LED20.1, R44.1
unnamed: Q3.2 (G2), R40.2, U7.11 (4Y)
unnamed: Q3.3 (D1), R107.1
unnamed: Q3.5 (G1), R38.2, U7.8 (3Y)
unnamed: Q3.6 (D2), R106.1
unnamed: Q7.1 (G), R35.2, U7.3 (1Y)
unnamed: Q8.1 (G), R36.2, U7.6 (2Y)
unnamed: R37.1, U8.7 (QH)
unnamed: R41.2, U9.14 (Y5)
unnamed: R42.2, U9.13 (Y6)
unnamed: R43.2, U9.12 (Y7)
unnamed: R44.2, U9.11 (Y8)
unnamed: R45.2, U11.1
unnamed: R48.1, U10.10 (EN2), U11.3, U12.4 (G)
unnamed: R103.2, U8.13 (~OE)
unnamed: U8.1 (QB), U9.7 (A6)
unnamed: U8.2 (QC), U9.8 (A7)
unnamed: U8.3 (QD), U9.9 (A8)
unnamed: U8.15 (QA), U9.6 (A5)
unnamed: U9.18 (Y1), U10.3 (A1)
unnamed: U9.17 (Y2), U10.4 (A2)
unnamed: U9.16 (Y3), U10.5 (A3)
unnamed: U9.15 (Y4), U10.6 (A4)
PWM1: U9.2 (A1)
PWM2: U9.3 (A2)
PWM3: U9.4 (A3)
PWM4: U9.5 (A4)
PWM_OUT1: R46.2, U7.1 (1A), U7.2 (1B), U10.14 (B1), U12.7 (2A)
PWM_OUT2: R47.2, U7.4 (2A), U7.5 (2B), U10.13 (B2), U12.9 (3A)
PWM_OUT3: R49.2, U7.9 (3A), U7.10 (3B), U10.12 (B3), U12.1 (1A)
PWM_OUT4: R50.2, U7.12 (4A), U7.13 (4B), U10.11 (B4), U12.15 (4A)
SNK1: CR1.1, CR7.1, Q7.3 (D)
SNK2: CR2.1, CR8.1, Q8.3 (D)
SPI1_CLK: C14.2, U8.11 (SRCLK)
SRC3: CR4.2, CR5.2, Q1.2 (S)
SRC4: CR3.2, CR6.2, Q2.2 (S)
~DIO_CS: C13.2, U8.12 (RCLK)
~RELAY_OE: J4.2, U8.5 (QF)
~WIZNET_RESET: J4.4, R37.2
