gasiepgodoy/Open-Source-PLC/Hardware/KiCad Files/Project/Power.kicad_sch

## KiCad design Hardware/KiCad Files/Project/Power.kicad_sch (2024-05-21)

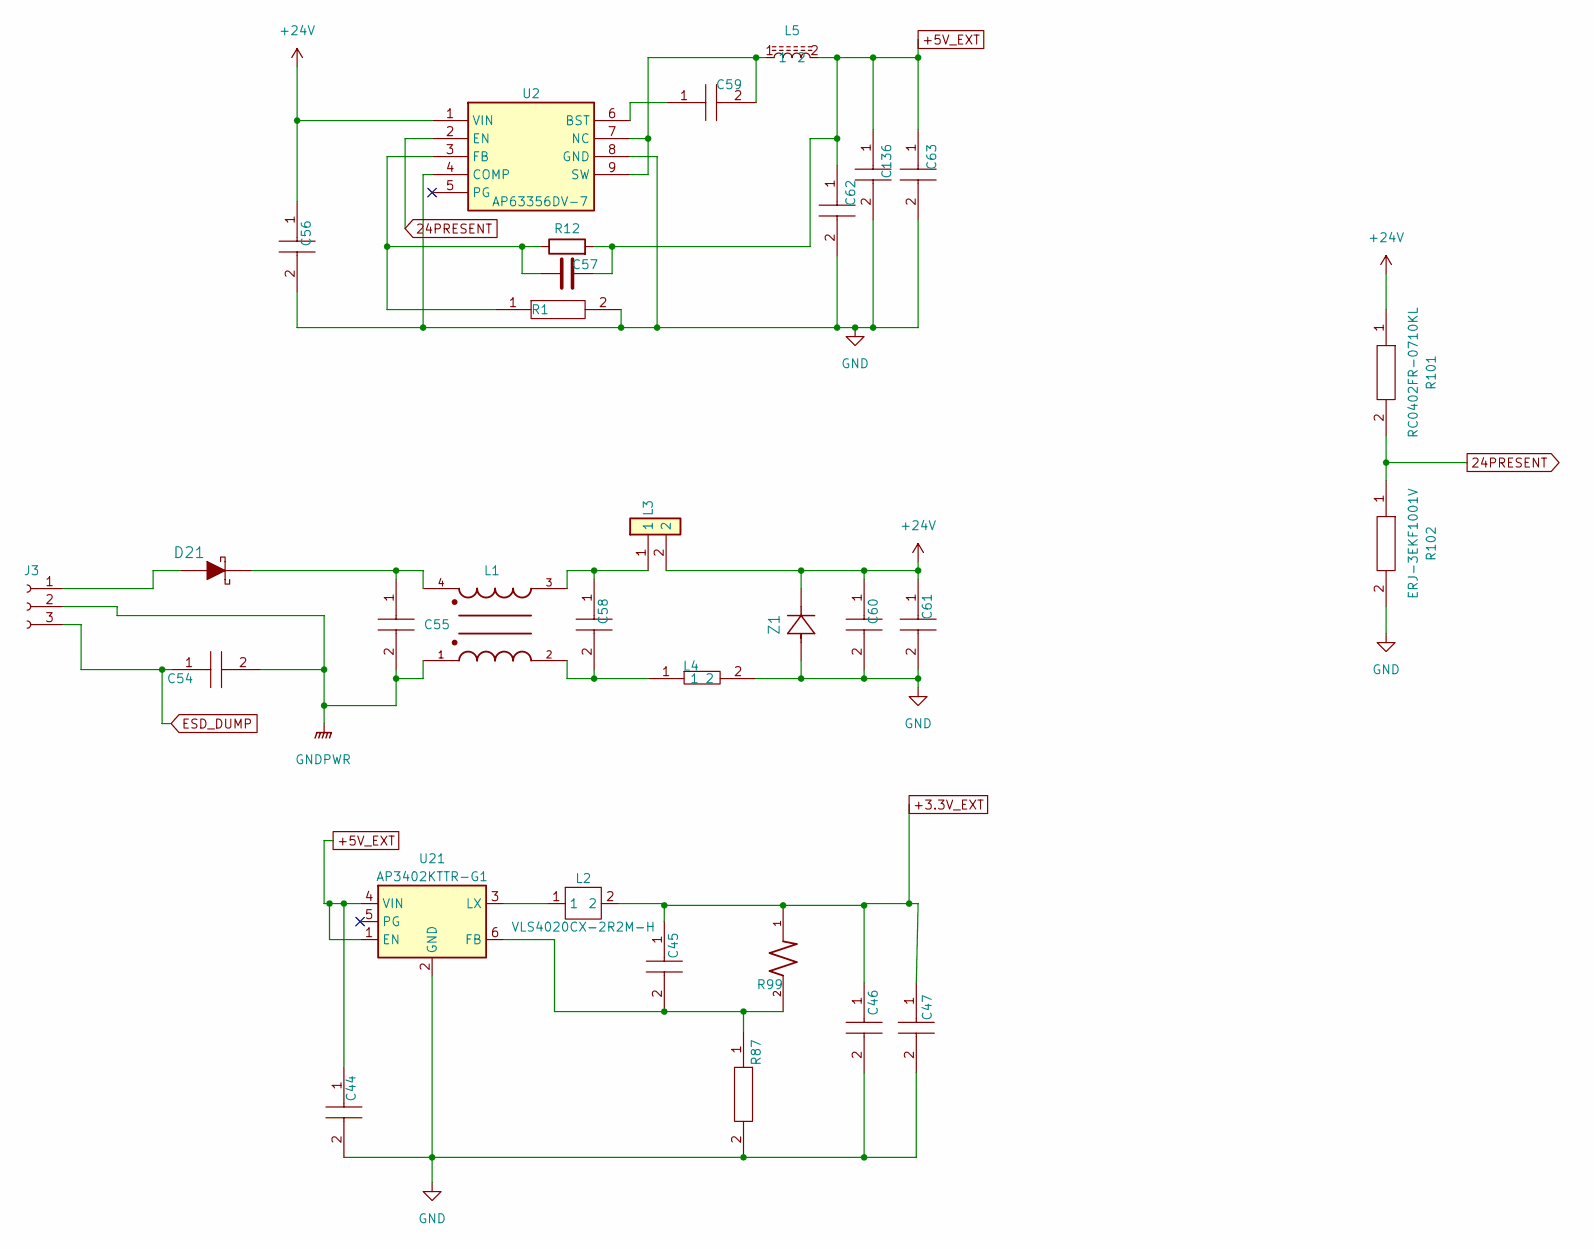
[picture p112: schematic Power.kicad_sch]

Parts:
C44: GRM188R61A106KE69J; C_0603_1608Metric; Manufacturer_Part_Number GRM188R61A106KE69J; Mouser Part Number 81-GRM188R61A106KE9J
C45: CL05C270JB5NNNC; C_0402_1005Metric; Manufacturer_Part_Number GRM1555C1H270JA01D; Mouser Part Number 81-GRM1555C1H270JA1D
C46, C47: CL31A226KAHNNNE; C_1206_3216Metric_Pad1.33x1.80mm_HandSolder; Manufacturer_Part_Number CL31A226KAHNNNE; Mouser Part Number 81-GRM31CR61E226KE5L
C54, C55, C58, C59, C61: GRM155R71H104KE14D; C_0402_1005Metric; Manufacturer_Part_Number GRM155R71H104KE14D; Mouser Part Number 81-GRM155R71H104KE4D
C56, C60: C3216X5R1H106K160AB; C_1206_3216Metric; Manufacturer_Part_Number GRM31CR61H106KA12L; Mouser Part Number 81-GRM31CR61H106KA2L
C57: CC0402JRNPO9BN100; C_0402_1005Metric
C62, C63, C136: CL31A226KAHNNNE; C_1206_3216Metric_Pad1.33x1.80mm_HandSolder; Manufacturer_Part_Number GRM31CR61E226KE15L; Mouser Part Number 81-GRM31CR61E226KE5L
D21: B240A-13-F; DO-214AC; MPN B240A-13-F; Digi-Key_PN B240A-FDICT-ND
J3: 2350514-3; SHDRRA3W90P0X350_1X3_1110X920X691P
L1: DLW5BTM142TQ2L; FIL_DLW5BTM142TQ2L; PARTREV N/A
L2: VLS4020CX-2R2M-H; VLS4020CX
L3: MPZ2012S331AT000; INDC2012X105N; Manufacturer_Part_Number MPZ2012S331AT000; Mouser Part Number 810-MPZ2012S331AT000
L4: MPZ2012S331AT000; INDC2012X105N; Manufacturer_Part_Number MPZ2012S331AT; Mouser Part Number N/A
L5: SRR1240-101M; IND_SRR1240-101M
R1: RR1220P-4751-D-M; R_0805_2012Metric; Manufacturer_Part_Number RR1220P-4751-D-M
R12: RC0402FR-0726K1L; R_0402_1005Metric_Pad0.72x0.64mm_HandSolder
R87, R101: RC0402FR-0710KL; R_0402_1005Metric_Pad0.72x0.64mm_HandSolder; Manufacturer_Part_Number RC0402FR-0710KL; Mouser Part Number 603-RC0402FR-0710KL
R99: RR1220P-4532-D-M; R_0805_2012Metric
R102: ERJ-3EKF1001V; R_0603_1608Metric; Manufacturer_Part_Number ERJ-3EKF1001V; Mouser Part Number 667-ERJ-3EKF1001V
U2: AP63356DV-7; AP63356DV7; Manufacturer_Part_Number AP63356DV-7; Mouser Part Number 621-AP63356DV-7
U21: AP3402KTTR-G1; SOT95P280X100-6N
Z1: SMAJ30CA-E3/61; SMAJ30CA-E3&slash_61

Connections:
24PRESENT: R101.2, R102.1, U2.2 (EN)
+3.3V_EXT: C45.1, C46.1, C47.1, L2.2, R99.1
+5V_EXT: C44.1, C57.2, C62.1, C63.1, C136.1, L5.2, R12.2, U21.1 (EN), U21.4 (VIN)
+24V: C56.1, C60.1, C61.1, L3.2, R101.1, U2.1 (VIN), Z1.1
ESD_DUMP: C54.1, J3.3
GND: C44.2, C46.2, C47.2, C56.2, C60.2, C61.2, C62.2, C63.2, C136.2, L4.2, R1.2, R87.2, R102.2, U2.4 (COMP), U2.8 (GND), U21.2 (GND), Z1.2
GNDPWR: C54.2, C55.2, J3.2, L1.1
unnamed: C45.2, R87.1, R99.2, U21.6 (FB)
unnamed: C55.1, D21.K, L1.4
unnamed: C57.1, R1.1, R12.1, U2.3 (FB)
unnamed: C58.1, L1.3, L3.1
unnamed: C58.2, L1.2, L4.1
unnamed: C59.1, U2.6 (BST)
unnamed: C59.2, L5.1, U2.7 (NC), U2.9 (SW)
unnamed: D21.A, J3.1
unnamed: L2.1, U21.3 (LX)
